SunnyYoshimitsu/CelestiCall/Hardwares/IPModules/USB 1.1/USB 1.1.runs/synth_1/.vivado.begin.rst

<?xml version="1.0"?>
<ProcessHandle Version="1" Minor="0">
    <Process Command="vivado.bat" Owner="Hatsu" Host="DESKTOP-I4589KT" Pid="29064" HostCore="12" HostMemory="034246979584">
    </Process>
</ProcessHandle>
