SunnyYoshimitsu/CelestiCall/Hardwares/IPModules/Sound/Sound Processor/Sound Processor.runs/impl_1/.vivado.begin.rst

<?xml version="1.0"?>
<ProcessHandle Version="1" Minor="0">
    <Process Command="vivado.bat" Owner="Hatsu" Host="DESKTOP-I4589KT" Pid="4896" HostCore="12" HostMemory="034246979584">
    </Process>
</ProcessHandle>
<?xml version="1.0"?>
<ProcessHandle Version="1" Minor="0">
    <Process Command="vivado.bat" Owner="Hatsu" Host="DESKTOP-I4589KT" Pid="36952" HostCore="12" HostMemory="034246979584">
    </Process>
</ProcessHandle>
<?xml version="1.0"?>
<ProcessHandle Version="1" Minor="0">
    <Process Command="vivado.bat" Owner="Hatsu" Host="DESKTOP-I4589KT" Pid="32116" HostCore="12" HostMemory="034246979584">
    </Process>
</ProcessHandle>
<?xml version="1.0"?>
<ProcessHandle Version="1" Minor="0">
    <Process Command="vivado.bat" Owner="Hatsu" Host="DESKTOP-I4589KT" Pid="14284" HostCore="12" HostMemory="034246979584">
    </Process>
</ProcessHandle>
<?xml version="1.0"?>
<ProcessHandle Version="1" Minor="0">
    <Process Command="vivado.bat" Owner="Hatsu" Host="DESKTOP-I4589KT" Pid="36900" HostCore="12" HostMemory="034246979584">
    </Process>
</ProcessHandle>
<?xml version="1.0"?>
<ProcessHandle Version="1" Minor="0">
    <Process Command="vivado.bat" Owner="Hatsu" Host="DESKTOP-I4589KT" Pid="37376" HostCore="12" HostMemory="034246979584">
    </Process>
</ProcessHandle>
<?xml version="1.0"?>
<ProcessHandle Version="1" Minor="0">
    <Process Command="vivado.bat" Owner="Hatsu" Host="DESKTOP-I4589KT" Pid="20940" HostCore="12" HostMemory="034246979584">
    </Process>
</ProcessHandle>
<?xml version="1.0"?>
<ProcessHandle Version="1" Minor="0">
    <Process Command="vivado.bat" Owner="Hatsu" Host="DESKTOP-I4589KT" Pid="10028" HostCore="12" HostMemory="034246979584">
    </Process>
</ProcessHandle>
<?xml version="1.0"?>
<ProcessHandle Version="1" Minor="0">
    <Process Command="vivado.bat" Owner="Hatsu" Host="DESKTOP-I4589KT" Pid="37008" HostCore="12" HostMemory="034246979584">
    </Process>
</ProcessHandle>
<?xml version="1.0"?>
<ProcessHandle Version="1" Minor="0">
    <Process Command="vivado.bat" Owner="Hatsu" Host="DESKTOP-I4589KT" Pid="36076" HostCore="12" HostMemory="034246979584">
    </Process>
</ProcessHandle>
<?xml version="1.0"?>
<ProcessHandle Version="1" Minor="0">
    <Process Command="vivado.bat" Owner="Hatsu" Host="DESKTOP-I4589KT" Pid="30560" HostCore="12" HostMemory="034246979584">
    </Process>
</ProcessHandle>
