SunnyYoshimitsu/CelestiCall/Hardwares/IPModules/Sound/Sound Processor/Sound Processor.runs/impl_1/clockInfo.txt

-------------------------------------
| Tool Version : Vivado v.2024.1
| Date         : Thu Jan  9 15:50:44 2025
| Host         : DESKTOP-I4589KT
| Design       : design_1
| Device       : xc7a100t-csg324-1--
-------------------------------------

For more information on clockInfo.txt clock routing debug file see https://support.xilinx.com/s/article/000035660?language=en_US
