SunnyYoshimitsu/CelestiCall/Hardwares/IPModules/Sound/Sound Processor/Sound Processor.runs/synth_1/.vivado.begin.rst

<?xml version="1.0"?>
<ProcessHandle Version="1" Minor="0">
    <Process Command="vivado.bat" Owner="Hatsu" Host="DESKTOP-I4589KT" Pid="4352" HostCore="12" HostMemory="034246979584">
    </Process>
</ProcessHandle>
