SunnyYoshimitsu/CelestiCall/Hardwares/Library_vivado/ip/hls_gamma_correction_1_0/doc/HLS_Gamma Correction_v1_0.pdf

1300 Henley Court
Pullman, WA 99163
509.334.6306
www.digilentinc.com

## HLS Gamma Correction 1.0 IP Core User Guide

Revised June 21, 2018; Author Ciprian Hegbeli

DOC#: 516-003 | Copyright Digilent, Inc. All rights reserved.
Other product and company names mentioned may be trademarks of their respective owners. | Page 1 of 5

## 1 Introduction

This user guide describes the Digilent Gamma Correction Intellectual Property. This IP interfaces to both the Axi-Lite and Axi-Stream in order to process a video stream and control the resolution and the gamma factor.

## 2 Features

- Axi- Stream 24-bit video input and output
- Axi-Lite interface for gamma and resolution control
- Resolution supported: up to 1920x1080/60Hz (clock: 148.5 MHz)
- Gamma adjustment: 0.4, 0.2, 1, 1.2, 1.4, 1.6, 1.8, 2.0, 2.2

## 3 Performance

The IP has been written in HLS with a target clock frequency of 150 MHz (6.67 ns) for a maximum resolution
of 1920x1080. The maximum latency is at 2081164 ns with
an initiation interval of 2081164 ns which is approximately
one frame. The latency and initiation interval are scaled with the input resolution, meaning that a lower resolution the latency will also be lower.

## 4 Usage

The IP has been initially designed for a xc7z020clg400-1 target device, the resource usage for this FPGA are illustrated in

IP quick facts

Supported device
families | Zynq®-7000, 7 series
Supported user interfaces | Axi-Lite
| Axi-Stream

Provided with core

Design files | C++
Simulation model | HLS Simulation
Constraints file | XDC
Software driver | Automatically
| generated

Tested design flows

Design entry | Vivado™ Design
| Suite 2017.4
Synthesis | Vivado Synthesis
| 2017.4

Sync 1.0 IP Core User Guide
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
