SunnyYoshimitsu/CelestiCall/Possible FPGA SoC Graphics/CelestiSoC.jpg

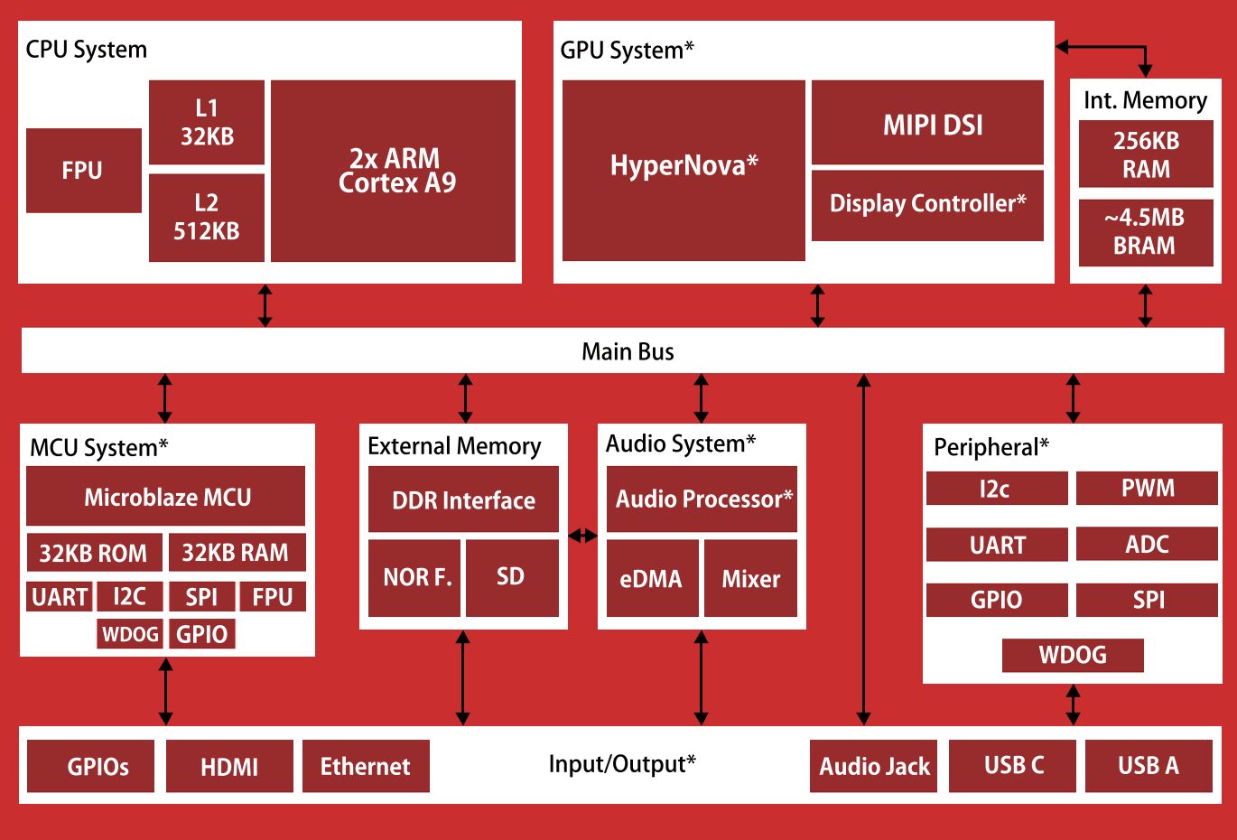
Possible FPGA SoC Graphics/CelestiSoC.jpg
