SunnyYoshimitsu/CelestiCall/Possible FPGA SoC Graphics/Rough Project Timeline.png

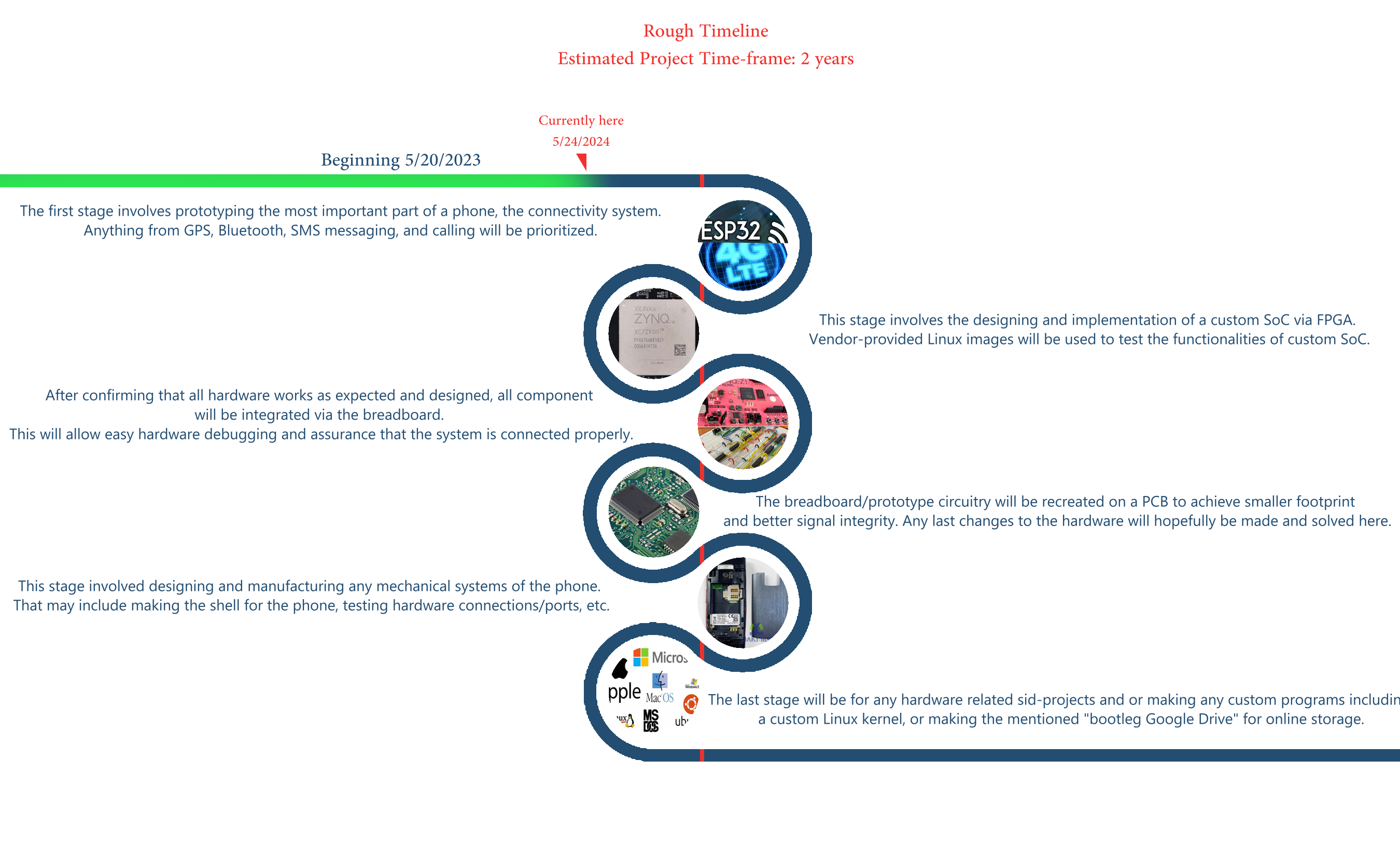
Possible FPGA SoC Graphics/Rough Project Timeline.png
