SunnyYoshimitsu/CelestiCall/Schematic & PCB (pending fixing)/zynqPCB-master/footprints/ESP32-C3 supermini v5.step

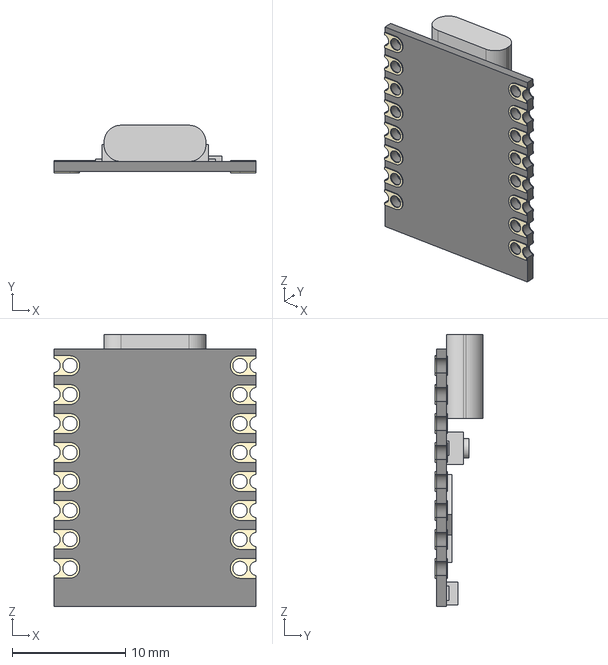
[picture p47: CAD file, 2024-06-05]
Schematic & PCB (pending fixing)/zynqPCB-master/footprints/ESP32-C3 supermini v5.step
17.8 x 4.20 x 24.0 mm
