SunnyYoshimitsu/CelestiCall/Schematic & PCB (pending fixing)/zynqPCB-master/footprints/SIM7100-6-1-15-00-A_REVC.step

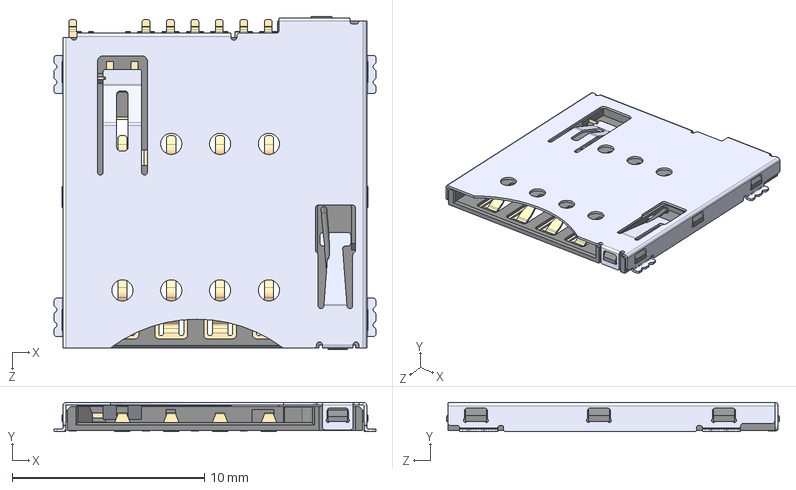
[picture p48: CAD file, 2024-06-05]
Schematic & PCB (pending fixing)/zynqPCB-master/footprints/SIM7100-6-1-15-00-A_REVC.step
16.8 x 1.53 x 17.3 mm
