SunnyYoshimitsu/CelestiCall/Hardwares/Library_vivado/ip/rgb2vga_v1_0/docs/rgb2vga_v1_0.pdf

1300 Henley Court
Pullman, WA 99163
509.334.6306
www.digilentinc.com

## RGB-to-VGA 1.0 IP Core User Guide

Revised April 23, 2015; Author Elod Gyorgy

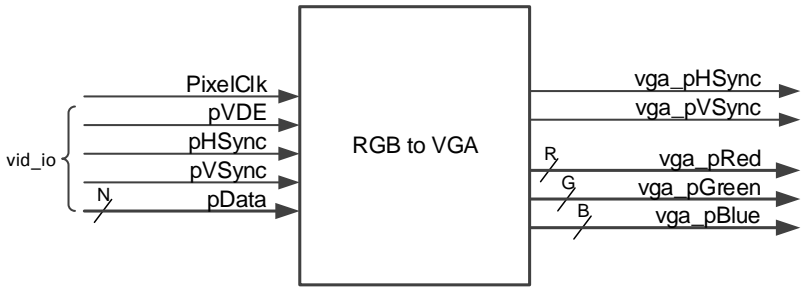
[picture p50: figure]
RGB to VGA; vga_pRed vga_pGreen vga_pBlue; vga_pHSync vga_pVSync; PixelClk pVDE pHSync pVSync pData; vid_io

DOC#: 506-031 | Copyright Digilent, Inc. All rights reserved.
Other product and company names mentioned may be trademarks of their respective owners. | Page 1 of 2

## 1 Overview

This user guide describes the Digilent RGB-to-VGA Intellectual Property. This IP accepts a Xilinx vid_io input and outputs an independently customizable color depth, properly blanked RGB pixel bus to connect to a VGA DAC. On Digilent boards the outputs directly connect to the on-board resistor ladder that serves as VGA DAC. The supported color depth varies between boards and the IP should be configured to match it.

## 2 Performance

The IP itself does not include timing constrains. PixelClk is still expected to be period-constrained from outside.

## 3 Port descriptions

Figure 1. IP top-level diagram.

The signals of the RGB-to-VGA Core are listed and described in Table 1.

IP quick facts

Supported device
families | Zynq®-7000, 7 series

Supported user
interfaces | Xilinx: vid_io

Provided with core

Design files | VHDL
Simulation model | VHDL Behavioral
Constraints file | N/A
Software driver | N/A

Tested design flows

Design entry | Vivado™ Design
| Suite 2014.4
Synthesis | Vivado Synthesis
| 2014.4

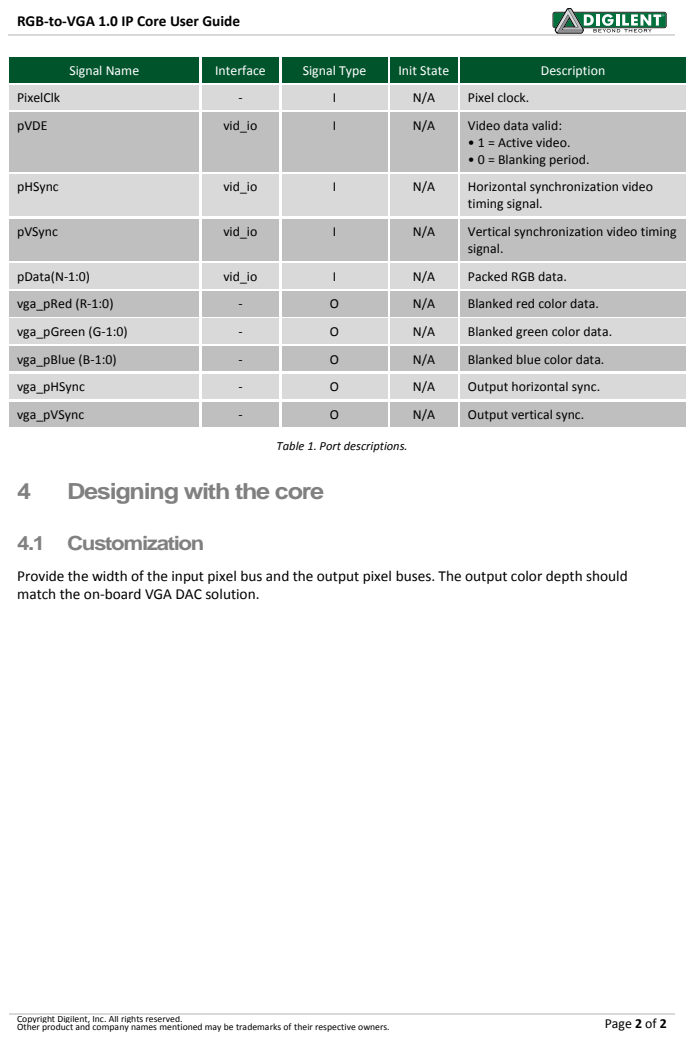
[picture p51: page 2]
Other product and company names mentioned may be trademarks of their respective owners.; Page 2 of 2; Signal Name; Interface; Signal Type; Init State; Description; PixelClk; Pixel clock.; pVDE; vid_io; Video data valid:; • 1 = Active video. • 0 = Blanking period.; pHSync; Horizontal synchronization video; timing signal.; pVSync; Vertical synchronization video timing; signal.; pData(N-1:0); Packed RGB data.; vga_pRed (R-1:0); Blanked red color data.; vga_pGreen (G-1:0)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

RGB-to-VGA 1.0 IP Core User Guide

Table 1. Port descriptions.

4 Designing with the core

Provide the width of the input pixel bus and the output pixel buses. The output color depth should
match the on-board VGA DAC solution.

Copyright Digilent, Inc. All rights reserved.
