SunnyYoshimitsu/CelestiCall/Hardwares/Library_vivado/ip/video_scaler/doc/video_scaler.pdf

1300 Henley Court
Pullman, WA 99163
509.334.6306
www.digilentinc.com

## Video Scaler 1.0 IP Core User Guide

Revised January 28, 2019; Author Elod Gyorgy

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

## 1 Introduction

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

## 2 Features

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

## 3 Designing with the core

## 3.1 Constraints 3.2 Customization

## 4 Register map

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

IP quick facts

Supported device
families | Zynq®-7000, 7 series
Supported user interfaces | Xilinx®: AXI4-Lite,
| AXI-Stream

Provided with core

Design files | VHDL
Simulation model | VHDL Behavioral
Constraints file | XDC
Software driver | standalone

Tested design flows

Design entry | Vivado™ HLS 2018.2
Synthesis | Vivado Synthesis
| 2018.2

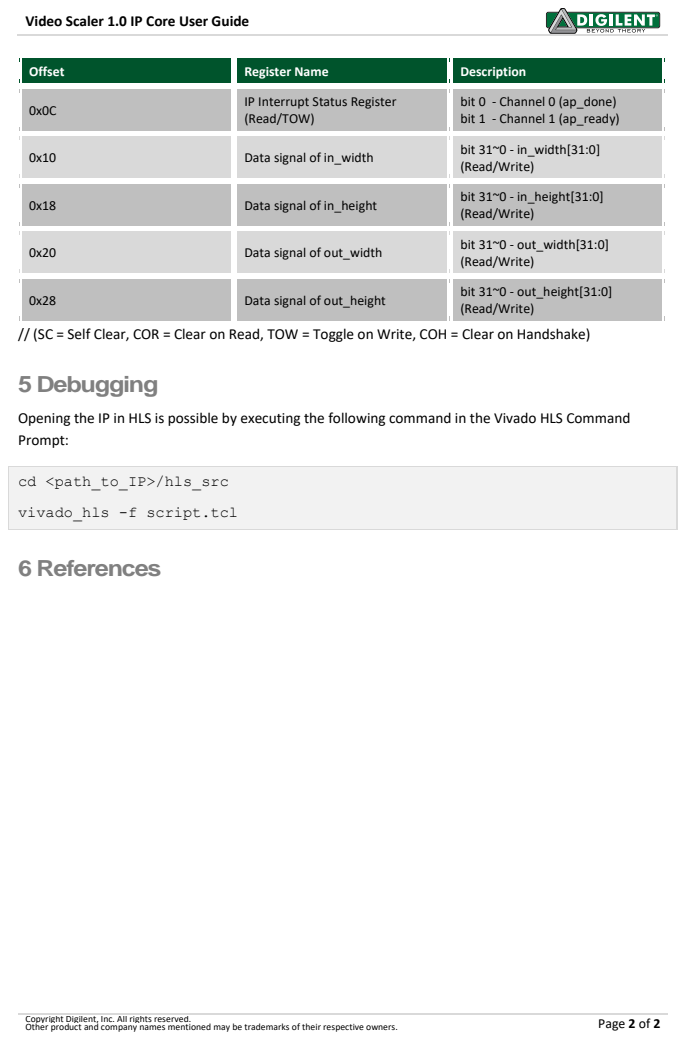
[picture p52: page 2]
Other product and company names mentioned may be trademarks of their respective owners.; Page 2 of 2; Offset; Register Name; Description; IP Interrupt Status Register; (Read/TOW); bit 0 - Channel 0 (ap_done) bit 1 - Channel 1 (ap_ready); Data signal of in_width; bit 31~0 - in_width[31:0]; (Read/Write); Data signal of in_height; bit 31~0 - in_height[31:0]; Data signal of out_width; bit 31~0 - out_width[31:0]; Data signal of out_height; bit 31~0 - out_height[31:0]; 5 Debugging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

Video Scaler 1.0 IP Core User Guide

// (SC = Self Clear, COR = Clear on Read, TOW = Toggle on Write, COH = Clear on Handshake)

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

Copyright Digilent, Inc. All rights reserved.
