SunnyYoshimitsu/CelestiCall/Hardwares/Library_vivado/ip/rgb2dpvid_v1_0/docs/rgb2dpvid_v1_0.pdf

## RGB-to-DPVID 1.0 IP Core User Guide

## 1 Introduction

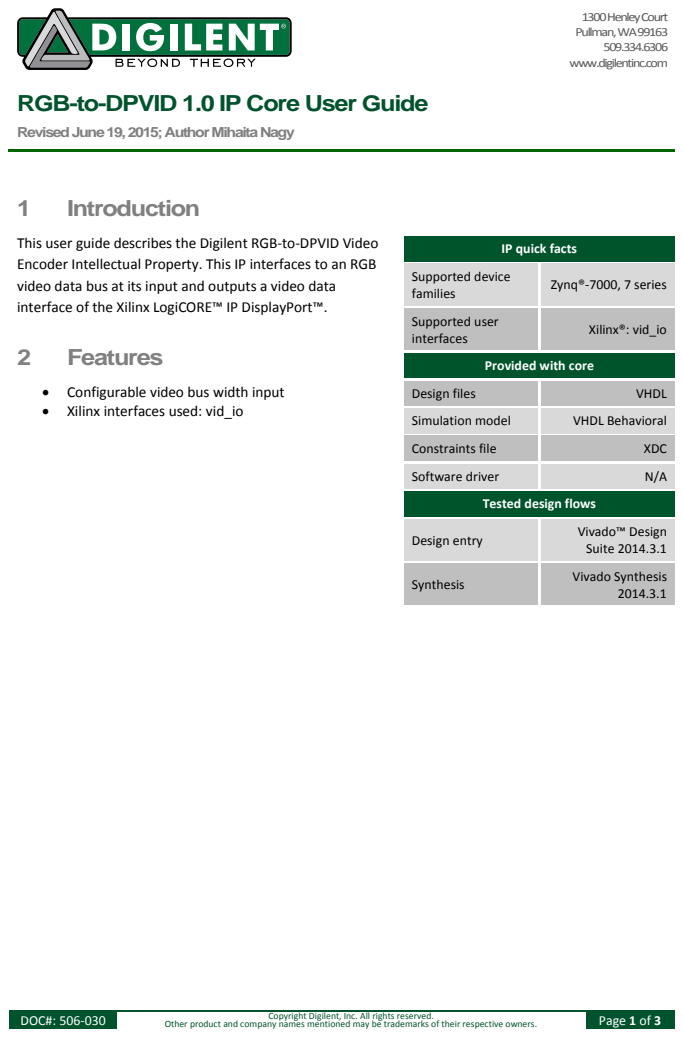
[picture p53: page 1]
DOC#: 506-030; Copyright Digilent, Inc. All rights reserved.; Other product and company names mentioned may be trademarks of their respective owners.; Page 1 of 3; 2 Features; Supported device; families; Zynq®-7000, 7 series; Supported user; interfaces; Xilinx®: vid_io; Design files; VHDL; Simulation model; VHDL Behavioral; Constraints file; XDC; Software driver; Design entry; Vivado™ Design; Suite 2014.3.1; Synthesis; Vivado Synthesis

1300 Henley Court
Pullman, WA 99163
www.digilentinc.com

Revised June 19, 2015; Author Mihaita Nagy

This user guide describes the Digilent RGB-to-DPVID Video
Encoder Intellectual Property. This IP interfaces to an RGB
video data bus at its input and outputs a video data
interface of the Xilinx LogiCORE™ IP DisplayPort™.

IP quick facts

Provided with core

• Configurable video bus width input
• Xilinx interfaces used: vid_io

Tested design flows

## 3 Overview

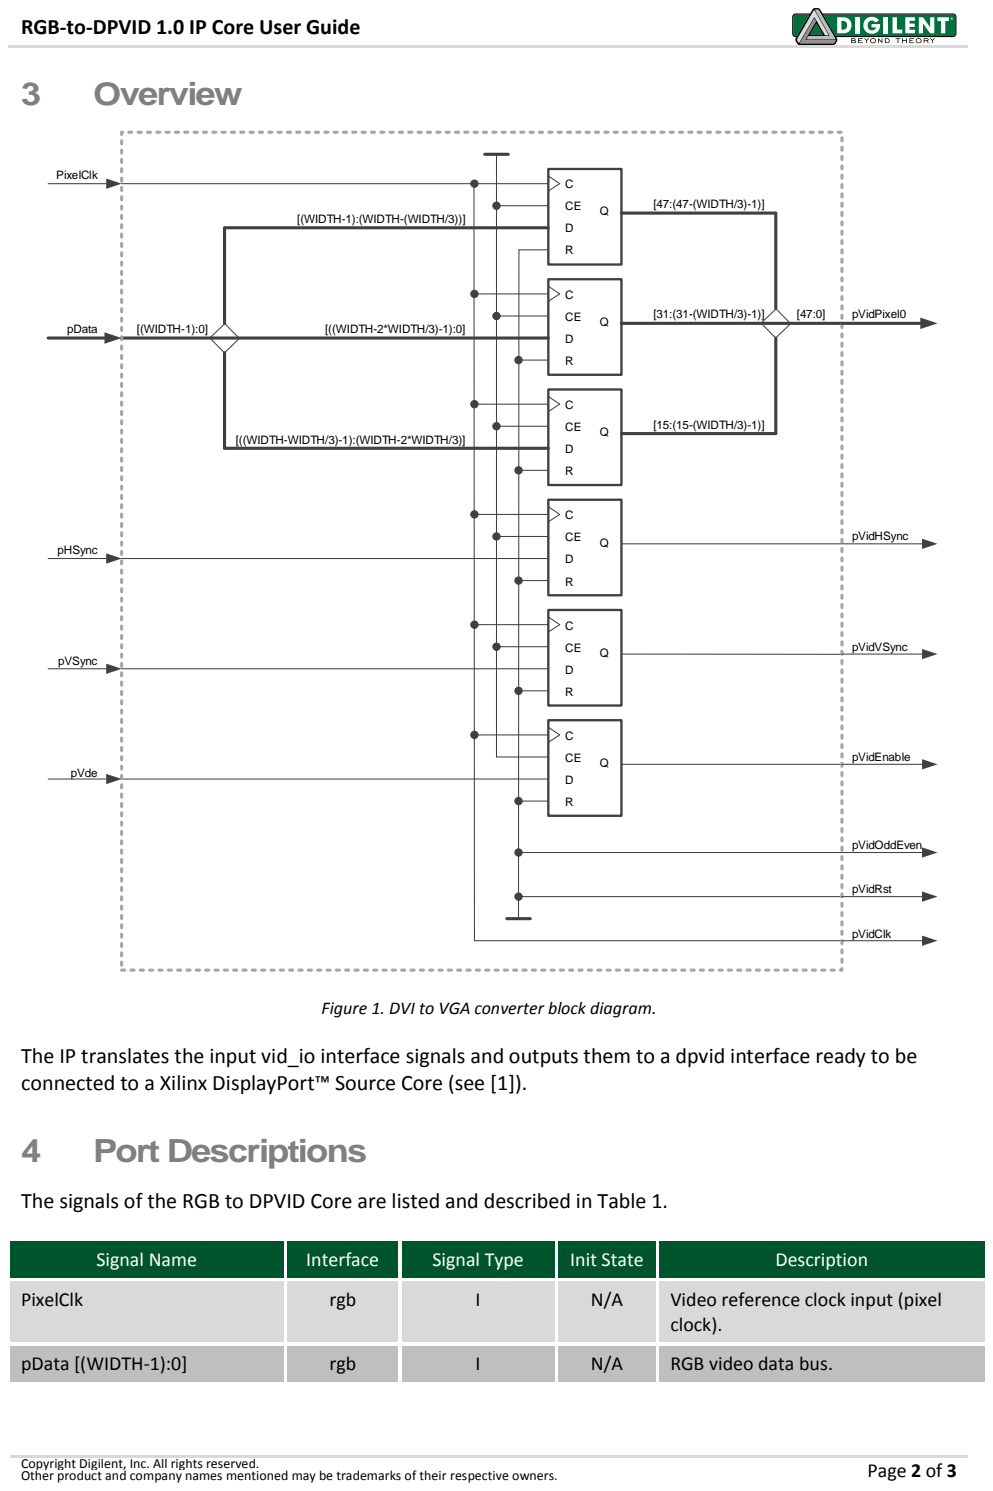
[picture p54: page 2]
Other product and company names mentioned may be trademarks of their respective owners.; Page 2 of 3; [((WIDTH-2*WIDTH/3)-1):0]; [47:(47-(WIDTH/3)-1)]; [31:(31-(WIDTH/3)-1)]; [15:(15-(WIDTH/3)-1)]; [(WIDTH-1):0]; PixelClk; pData; pHSync; pVSync; pVde; pVidPixel0; pVidHSync; pVidVSync; pVidEnable; pVidOddEven; pVidRst; pVidClk; 4 Port Descriptions; Signal Name; Interface; Signal Type; Init State; Description; rgb; Video reference clock input (pixel; clock).; pData [(WIDTH-1):0]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

RGB-to-DPVID 1.0 IP Core User Guide

[(WIDTH-1):(WIDTH-(WIDTH/3))]

[((WIDTH-WIDTH/3)-1):(WIDTH-2*WIDTH/3)]

Figure 1. DVI to VGA converter block diagram.

The IP translates the input vid_io interface signals and outputs them to a dpvid interface ready to be
connected to a Xilinx DisplayPort™ Source Core (see [1]).

The signals of the RGB to DPVID Core are listed and described in Table 1.

Copyright Digilent, Inc. All rights reserved.

RGB-to-DPVID 1.0 IP Core User Guide

Copyright Digilent, Inc. All rights reserved.
Other product and company names mentioned may be trademarks of their respective owners. | Page 3 of 3
pHSync | rgb | I | N/A | Horizontal synchronization video timing signal.
pVSync | rgb | I | N/A | Vertical synchronization video timing signal.
pVde | rgb | I | N/A | Video data valid: • 1 = Active video. • 0 = Blanking period.
pVidClk | dpvid | O | 0 | Forwarded PixelClk signal.
pVidPixel0 [47:0] | dpvid | O | zeros | Video data output.
pVidHSync | dpvid | O | 0 | Horizontal synchronization video timing signal.
pVidVSync | dpvid | O | 0 | Vertical synchronization video timing signal.
pVidEnable | dpvid | O | 0 | Video data qualifier: • 1 = Video data valid. • 0 = Video data not valid.
pVidOddEven | dpvid | O | 0 | Unused.
pVidRst | dpvid | O | 0 | Unused.

Table 1. Port descriptions.

## 5 Parameter Descriptions

The parameters of the RGB to DPVID Core are listed and described in Table 12 below.

Parameter Name | Range | Type | Default | Description
kDataWidth | 0 - 47 | integer | 24 | Sets the input video data bus width containing already the video components. It is limited at a maximum of 48 which is the limit of the dpvid-interface data signal input (see Table 3-3 of [1]).

Table 2. Parameter descriptions.

## 6 References

The following documents provide additional information on the subjects discussed:

1. Xilinx Inc., PG064: DisplayPort LogiCORE IP Product Guide, v6.0, April 1, 2015.
