SunnyYoshimitsu/CelestiCall/Schematic & PCB (pending fixing)/zynqPCB-master/Audio.kicad_sch

## KiCad design Schematic & PCB (pending fixing)/zynqPCB-master/Audio.kicad_sch (2024-07-29)

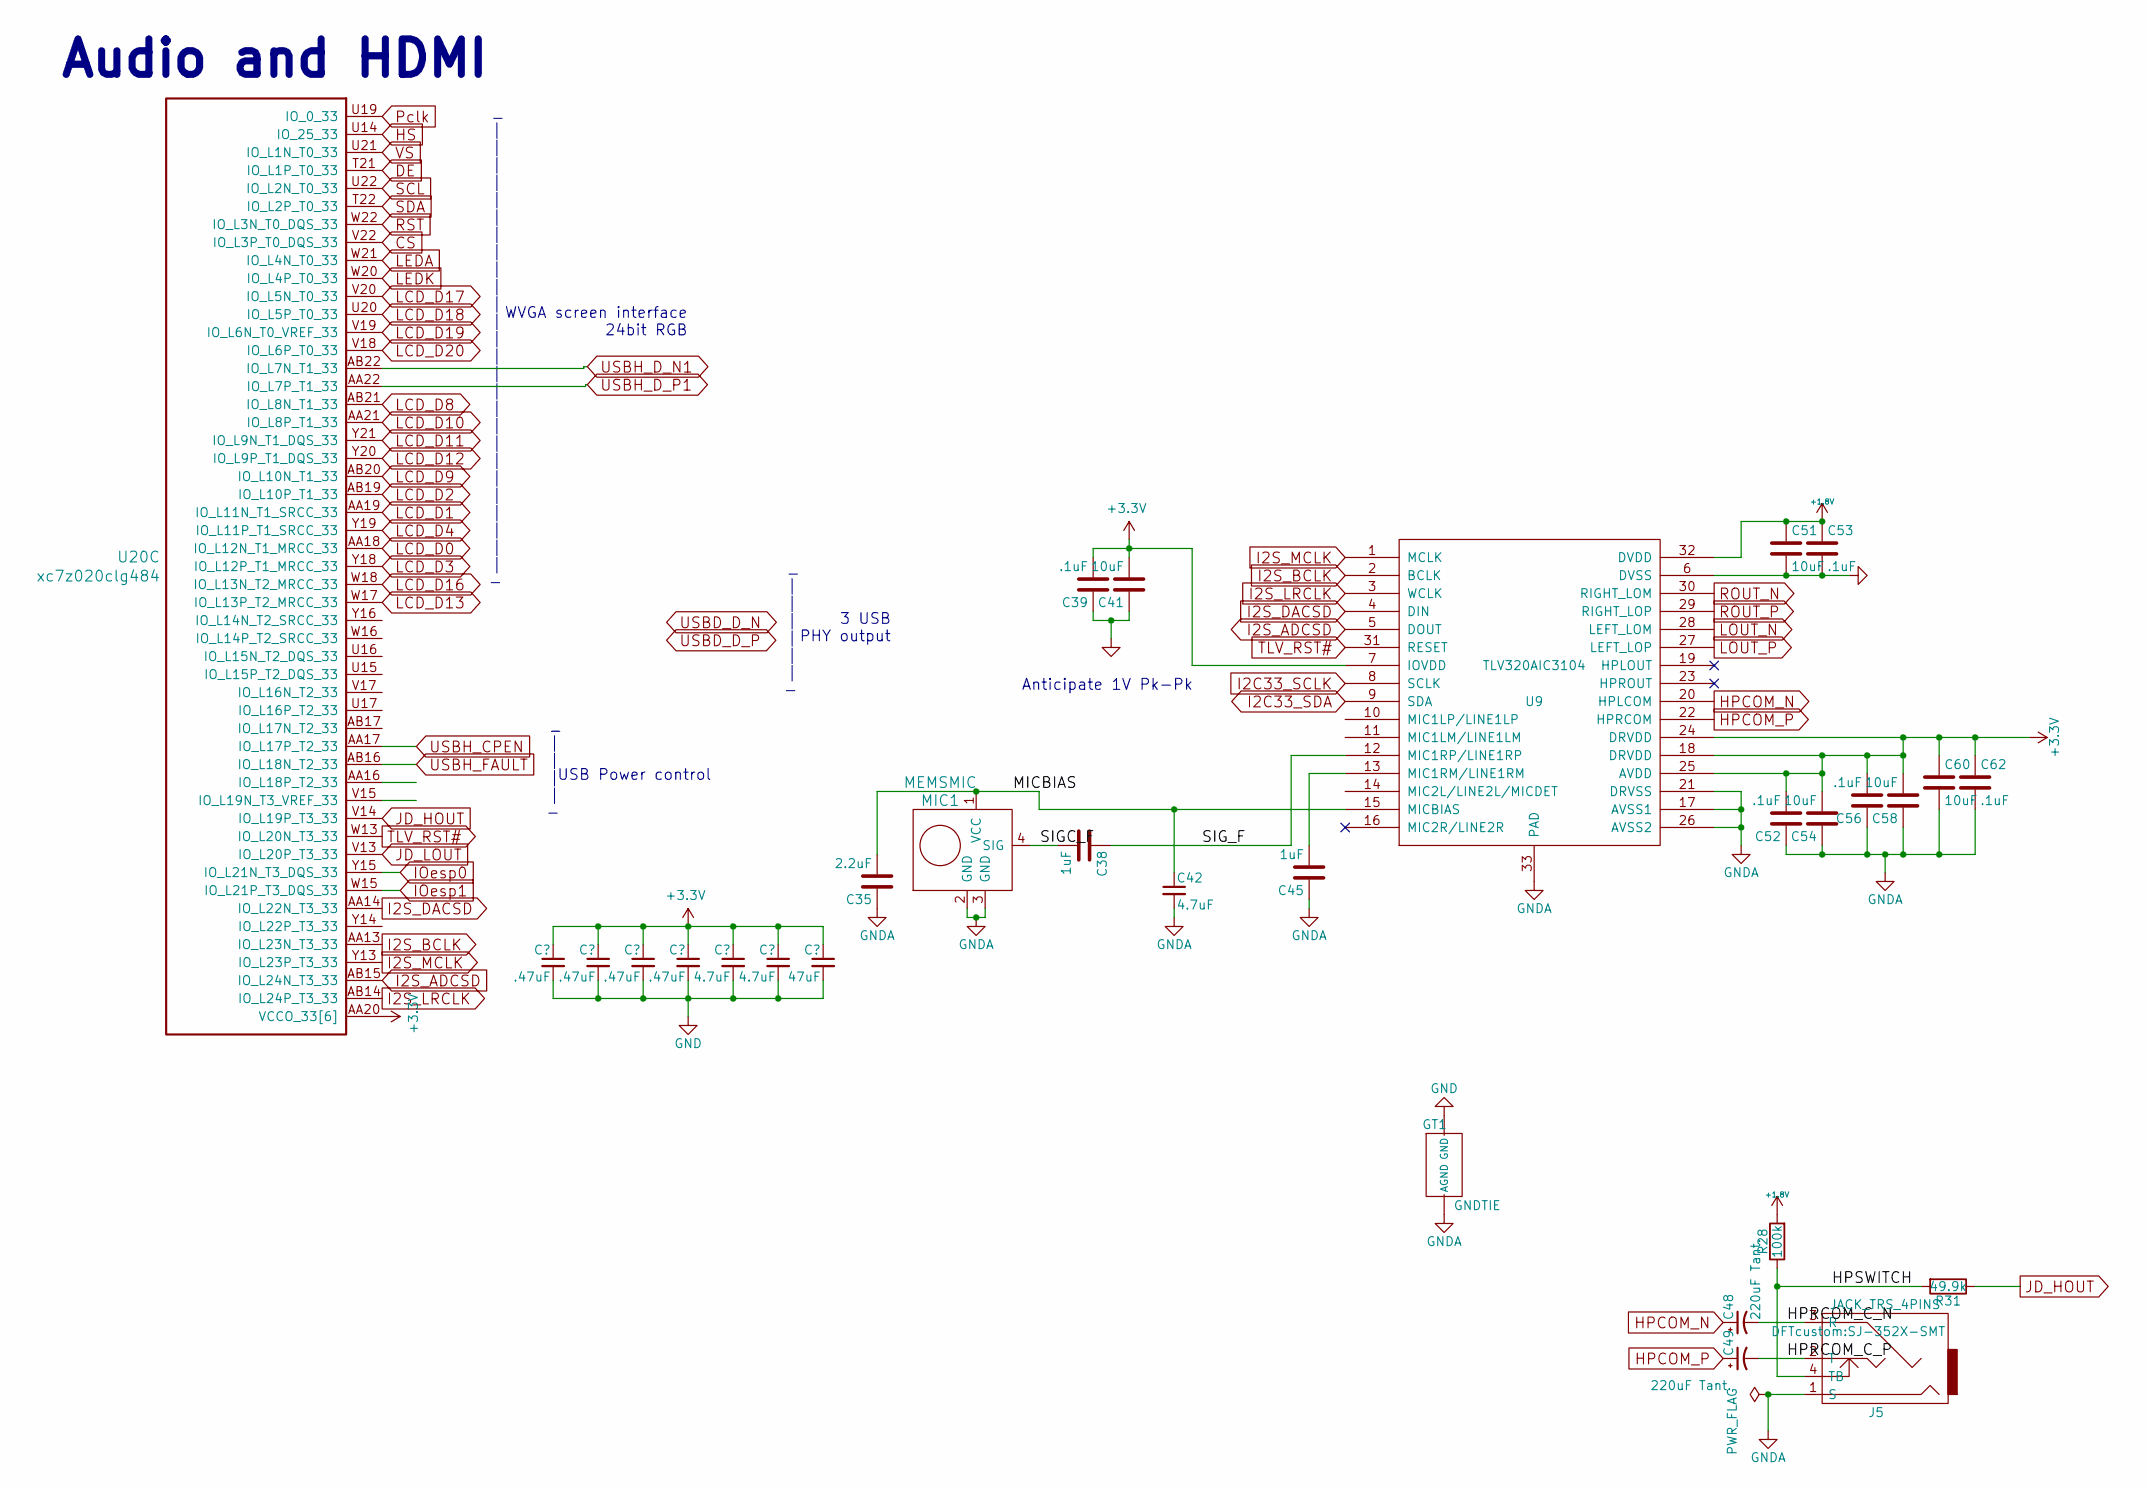
[picture p72: schematic Audio.kicad_sch]

Parts:
C35: 2.2uF; C_0402_1005Metric; MPN GRM155R61A225KE95D
C38, C45: 1uF; C_0402_1005Metric; MPN CC0402KRX5R6BB105
C39, C52, C53, C56, C62: .1uF; C_0402_1005Metric; MPN CC0402KRX7R6BB104
C41, C51, C54, C58, C60: 10uF; C_0603_1608Metric; MPN GRM188R61A106KE69J
C42, C57, C59: 4.7uF; C_0402_1005Metric; MPN GRM155R60G475ME47D
C46, C47, C50, C55: .47uF; C_0402_1005Metric; MPN CC0402KRX5R5BB474
C48, C49: 220uF Tant.; CP_EIA-3528-12_Kemet-T; MPN F930G227KBA
C61: 47uF; C_0805_2012Metric; MPN GRM219R60J476ME44D
GT1: GNDTIE; gndtie
J5: JACK_TRS_4PINS; SJ-352X-SMT; MPN SJ-3524-SMT-TR
MIC1: MEMSMIC; MIC_SPW2430HR5H-B; MPN SPW2430HR5H-B
R28: 100k; R_0402_1005Metric; MPN RC0402FR-07100KL
R31: 49.9k; R_0402_1005Metric; MPN RC0402FR-0749K9L
U9: TLV320AIC3104; QFN-32-1EP_5x5mm_P0.5mm_EP3.65x3.65mm; MPN TLV320AIC3104IRHBR
U20: xc7z020clg484; BGA-484_19.0x19.0mm_Layout22x22_P0.80mm_dia0.40mm; MPN XC7Z020-1CLG484C

Connections:
+1.8V: C51.1, C53.1, R28.2, U9.32 (DVDD)
+3.3V: C39.2, C41.2, C46.1, C47.1, C50.1, C52.2, C54.2, C55.1, C56.2, C57.1, C58.2, C59.1, C60.1, C61.1, C62.1, U9.7 (IOVDD), U9.18 (DRVDD), U9.24 (DRVDD), U9.25 (AVDD), U20.AA20 (VCCO_33[6]), U20.AB13 (VCCO_33[6]), U20.U18 (VCCO_33[6]), U20.V21 (VCCO_33[6]), U20.W14 (VCCO_33[6]), U20.Y17 (VCCO_33[6])
CS: U20.V22 (IO_L3P_T0_DQS_33)
DE: U20.T21 (IO_L1P_T0_33)
GND: C39.1, C41.1, C46.2, C47.2, C50.2, C51.2, C53.2, C55.2, C57.2, C59.2, C61.2, GT1.1 (GND), U9.6 (DVSS)
GNDA: C35.1, C42.2, C45.1, C52.1, C54.1, C56.1, C58.1, C60.2, C62.2, GT1.2 (AGND), J5.1 (S), MIC1.2 (GND), MIC1.3 (GND), U9.17 (AVSS1), U9.21 (DRVSS), U9.26 (AVSS2), U9.33 (PAD)
HPCOM_N: C48.1, U9.20 (HPLCOM)
HPCOM_P: C49.1, U9.22 (HPRCOM)
HPRCOM_C_N: C48.2, J5.3 (R)
HPRCOM_C_P: C49.2, J5.2 (T)
HPSWITCH: J5.4 (TB), R28.1, R31.2
HS: U20.U14 (IO_25_33)
I2C33_SCLK: U9.8 (SCLK)
I2C33_SDA: U9.9 (SDA)
I2S_ADCSD: U9.5 (DOUT), U20.AB15 (IO_L24N_T3_33)
I2S_BCLK: U9.2 (BCLK), U20.AA13 (IO_L23N_T3_33)
I2S_DACSD: U9.4 (DIN), U20.AA14 (IO_L22N_T3_33)
I2S_LRCLK: U9.3 (WCLK), U20.AB14 (IO_L24P_T3_33)
I2S_MCLK: U9.1 (MCLK), U20.Y13 (IO_L23P_T3_33)
IOesp0: U20.Y15 (IO_L21N_T3_DQS_33)
IOesp1: U20.W15 (IO_L21P_T3_DQS_33)
JD_HOUT: R31.1, U20.V14 (IO_L19P_T3_33)
JD_LOUT: U20.V13 (IO_L20P_T3_33)
LCD_D0: U20.AA18 (IO_L12N_T1_MRCC_33)
LCD_D1: U20.AA19 (IO_L11N_T1_SRCC_33)
LCD_D2: U20.AB19 (IO_L10P_T1_33)
LCD_D3: U20.Y18 (IO_L12P_T1_MRCC_33)
LCD_D4: U20.Y19 (IO_L11P_T1_SRCC_33)
LCD_D8: U20.AB21 (IO_L8N_T1_33)
LCD_D9: U20.AB20 (IO_L10N_T1_33)
LCD_D10: U20.AA21 (IO_L8P_T1_33)
LCD_D11: U20.Y21 (IO_L9N_T1_DQS_33)
LCD_D12: U20.Y20 (IO_L9P_T1_DQS_33)
LCD_D13: U20.W17 (IO_L13P_T2_MRCC_33)
LCD_D16: U20.W18 (IO_L13N_T2_MRCC_33)
LCD_D17: U20.V20 (IO_L5N_T0_33)
LCD_D18: U20.U20 (IO_L5P_T0_33)
LCD_D19: U20.V19 (IO_L6N_T0_VREF_33)
LCD_D20: U20.V18 (IO_L6P_T0_33)
LEDA: U20.W21 (IO_L4N_T0_33)
LEDK: U20.W20 (IO_L4P_T0_33)
LOUT_N: U9.28 (LEFT_LOM)
LOUT_P: U9.27 (LEFT_LOP)
MICBIAS: C35.2, C42.1, MIC1.1 (VCC), U9.15 (MICBIAS)
unnamed: C45.2, U9.13 (MIC1RM/LINE1RM)
Pclk: U20.U19 (IO_0_33)
ROUT_N: U9.30 (RIGHT_LOM)
ROUT_P: U9.29 (RIGHT_LOP)
RST: U20.W22 (IO_L3N_T0_DQS_33)
SCL: U20.U22 (IO_L2N_T0_33)
SDA: U20.T22 (IO_L2P_T0_33)
SIGC_F: C38.2, MIC1.4 (SIG)
SIG_F: C38.1, U9.12 (MIC1RP/LINE1RP)
TLV_RST#: U9.31 (RESET), U20.W13 (IO_L20N_T3_33)
USBH_CPEN: U20.AA17 (IO_L17P_T2_33)
USBH_D_N1: U20.AB22 (IO_L7N_T1_33)
USBH_D_P1: U20.AA22 (IO_L7P_T1_33)
USBH_FAULT: U20.AB16 (IO_L18N_T2_33)
VS: U20.U21 (IO_L1N_T0_33)

Notes on the sheet:
USB Power control
_ | | | | | | -
3 USB PHY output
_ | | | | -
Anticipate 1V Pk-Pk
Audio and HDMI
_ | | | | | | | | | | | | | | | | | | | | | | | | | | -
WVGA screen interface 24bit RGB
