SunnyYoshimitsu/CelestiCall/Schematic & PCB (pending fixing)/zynqPCB-master/LCD50.kicad_sch

## KiCad design Schematic & PCB (pending fixing)/zynqPCB-master/LCD50.kicad_sch (2024-07-29)

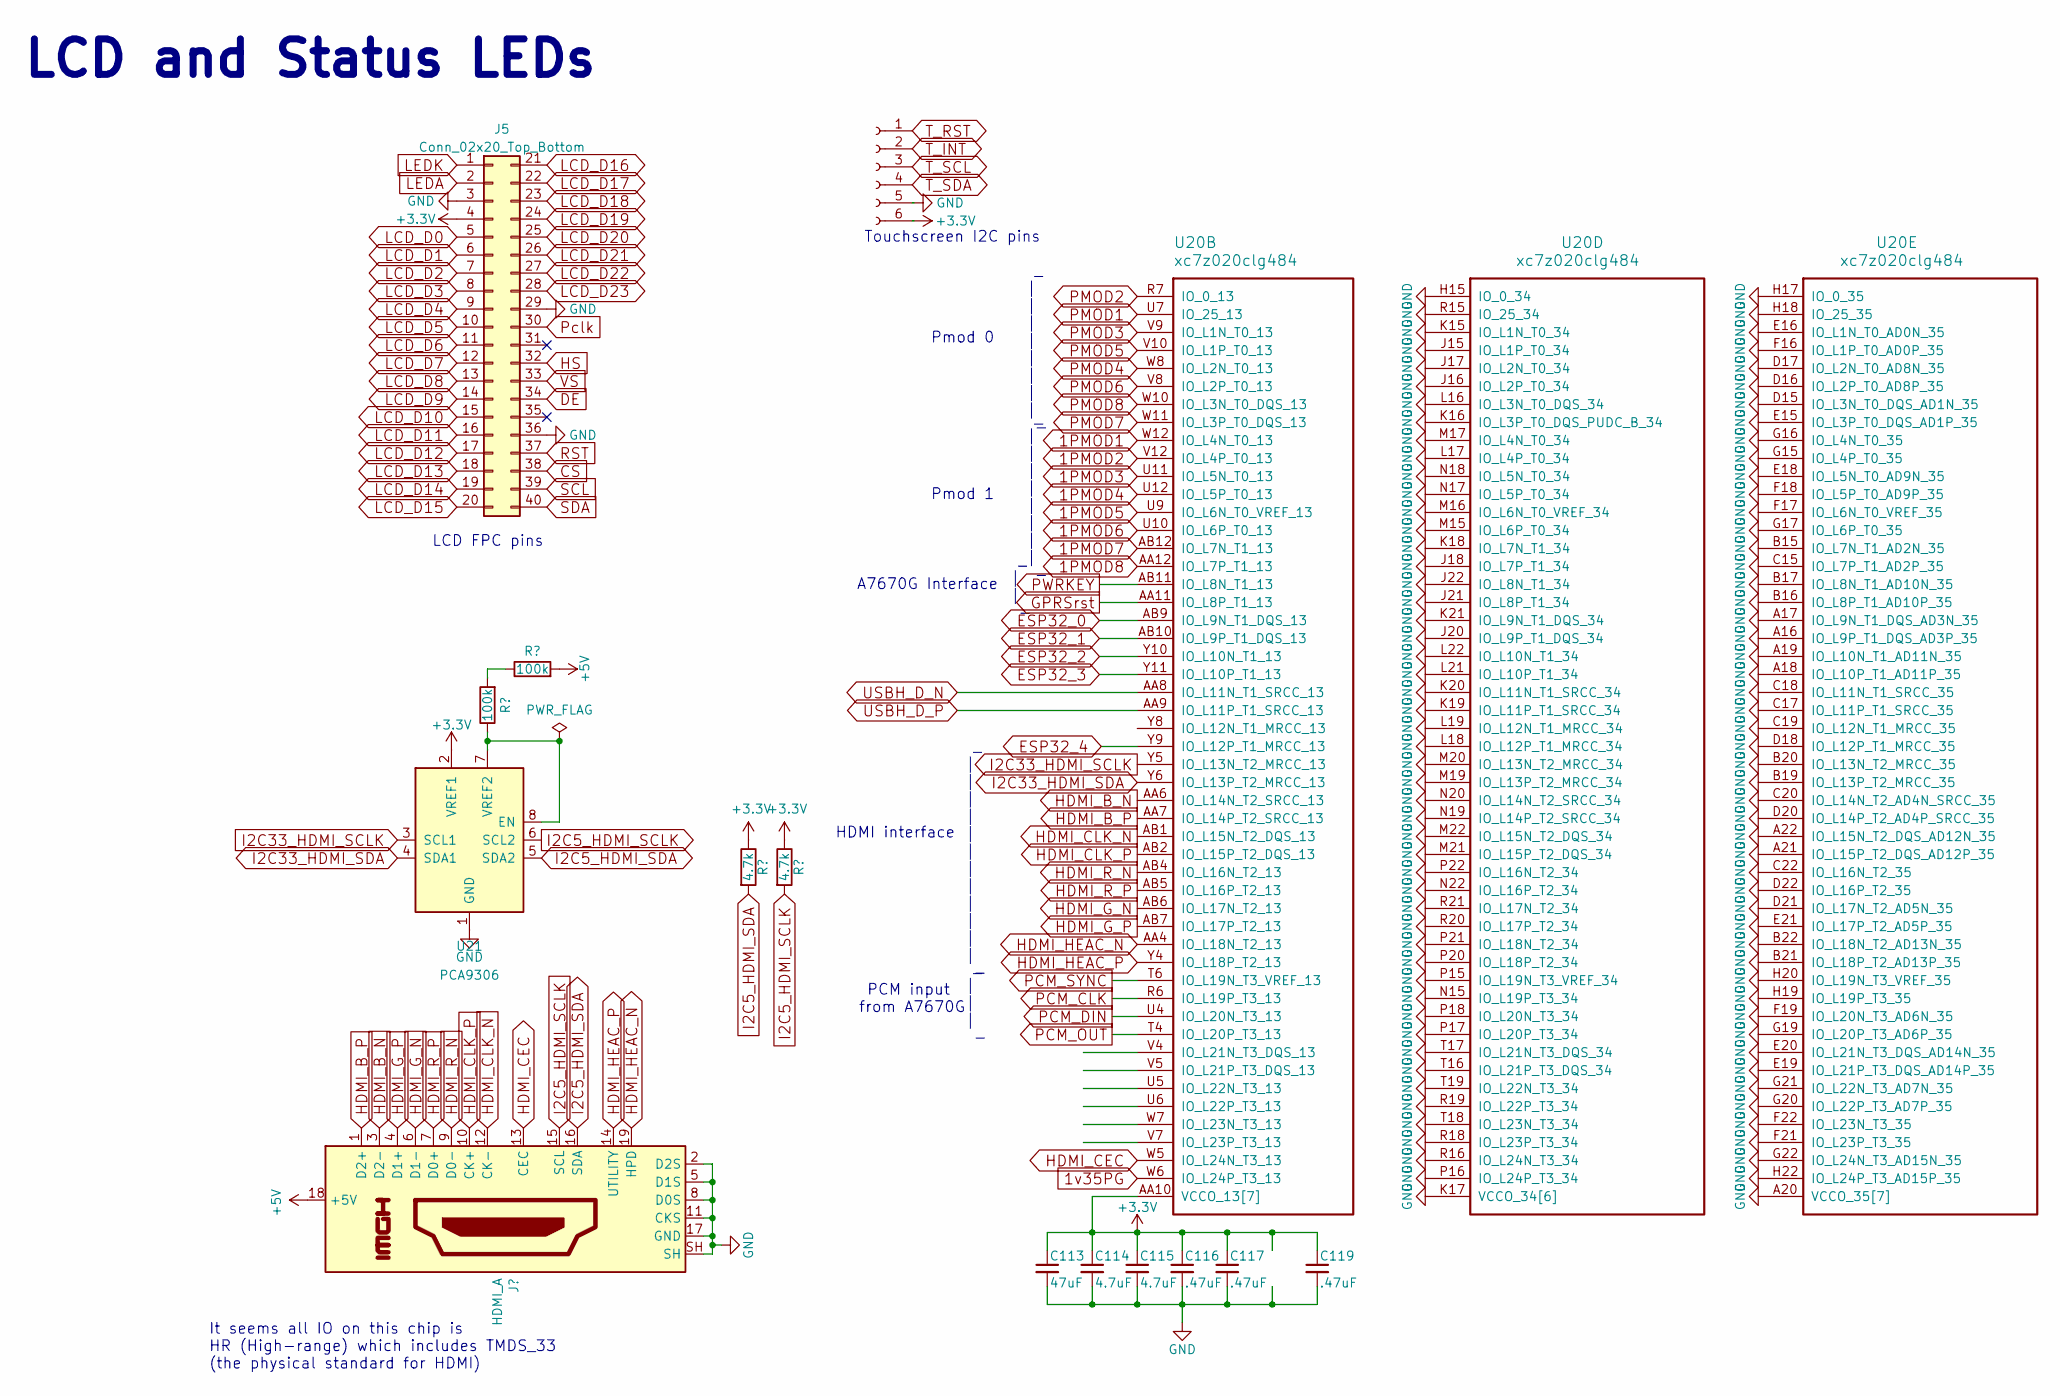
[picture p74: schematic LCD50.kicad_sch]

Parts:
C113: 47uF; C_1210_3225Metric; MPN GRM32ER70J476ME20L
C114, C115: 4.7uF; C_0402_1005Metric; MPN GRM155R60G475ME47D
C116, C117, C119: .47uF; C_0402_1005Metric; MPN CC0402KRX5R5BB474
J4: Conn_01x06_Female; Hirose_FH12-6S-0.5SH_1x06-1MP_P0.50mm_Horizontal
J5: Conn_02x20_Top_Bottom; TE_4-1734839-0_1x40-1MP_P0.5mm_Horizontal
J9: HDMI_A; 10029449-111RLF; MPN 10029449-111RLF
R34, R81: 100k; R_0402_1005Metric; MPN RC0402FR-07100KL
R82, R83: 4.7k; R_0402_1005Metric; MPN RC0402JR-074K7L
U20: xc7z020clg484; BGA-484_19.0x19.0mm_Layout22x22_P0.80mm_dia0.40mm; MPN XC7Z020-1CLG484C
U21: PCA9306; SSOP-8_2.95x2.8mm_P0.65mm; MPN PCA9306DCTR

Connections:
1PMOD1: U20.W12 (IO_L4N_T0_13)
1PMOD2: U20.V12 (IO_L4P_T0_13)
1PMOD3: U20.U11 (IO_L5N_T0_13)
1PMOD4: U20.U12 (IO_L5P_T0_13)
1PMOD5: U20.U9 (IO_L6N_T0_VREF_13)
1PMOD6: U20.U10 (IO_L6P_T0_13)
1PMOD7: U20.AB12 (IO_L7N_T1_13)
1PMOD8: U20.AA12 (IO_L7P_T1_13)
1v35PG: U20.W6 (IO_L24P_T3_13)
+3.3V: C113.1, C114.1, C115.1, C116.1, C117.1, C119.1, J4.6, J5.4, R82.1, R83.1, U20.AA10 (VCCO_13[7]), U20.AB3 (VCCO_13[7]), U20.T5 (VCCO_13[7]), U20.U8 (VCCO_13[7]), U20.V11 (VCCO_13[7]), U20.W4 (VCCO_13[7]), U20.Y7 (VCCO_13[7]), U21.2 (VREF1)
+5V: J9.18 (+5V), R81.2
CS: J5.38
DE: J5.34
ESP32_0: U20.AB9 (IO_L9N_T1_DQS_13)
ESP32_1: U20.AB10 (IO_L9P_T1_DQS_13)
ESP32_2: U20.Y10 (IO_L10N_T1_13)
ESP32_3: U20.Y11 (IO_L10P_T1_13)
ESP32_4: U20.Y9 (IO_L12P_T1_MRCC_13)
GND: C113.2, C114.2, C115.2, C116.2, C117.2, C119.2, J4.5, J5.3, J5.29, J5.36, J9.2 (D2S), J9.5 (D1S), J9.8 (D0S), J9.11 (CKS), J9.17 (GND), J9.SH, U20.A16 (IO_L9P_T1_DQS_AD3P_35), U20.A17 (IO_L9N_T1_DQS_AD3N_35), U20.A18 (IO_L10P_T1_AD11P_35), U20.A19 (IO_L10N_T1_AD11N_35), U20.A20 (VCCO_35[7]), U20.A21 (IO_L15P_T2_DQS_AD12P_35), U20.A22 (IO_L15N_T2_DQS_AD12N_35), U20.B15 (IO_L7N_T1_AD2N_35), U20.B16 (IO_L8P_T1_AD10P_35), U20.B17 (IO_L8N_T1_AD10N_35), U20.B19 (IO_L13P_T2_MRCC_35), U20.B20 (IO_L13N_T2_MRCC_35), U20.B21 (IO_L18P_T2_AD13P_35), U20.B22 (IO_L18N_T2_AD13N_35), U20.C15 (IO_L7P_T1_AD2P_35), U20.C16 (VCCO_35[7]), U20.C17 (IO_L11P_T1_SRCC_35), U20.C18 (IO_L11N_T1_SRCC_35), U20.C19 (IO_L12N_T1_MRCC_35), U20.C20 (IO_L14N_T2_AD4N_SRCC_35), U20.C22 (IO_L16N_T2_35), U20.D15 (IO_L3N_T0_DQS_AD1N_35), U20.D16 (IO_L2P_T0_AD8P_35), U20.D17 (IO_L2N_T0_AD8N_35), U20.D18 (IO_L12P_T1_MRCC_35), U20.D19 (VCCO_35[7]), U20.D20 (IO_L14P_T2_AD4P_SRCC_35), U20.D21 (IO_L17N_T2_AD5N_35), U20.D22 (IO_L16P_T2_35), U20.E15 (IO_L3P_T0_DQS_AD1P_35), U20.E16 (IO_L1N_T0_AD0N_35), U20.E18 (IO_L5N_T0_AD9N_35), U20.E19 (IO_L21P_T3_DQS_AD14P_35), U20.E20 (IO_L21N_T3_DQS_AD14N_35), U20.E21 (IO_L17P_T2_AD5P_35), U20.E22 (VCCO_35[7]), U20.F15 (VCCO_35[7]), U20.F16 (IO_L1P_T0_AD0P_35), U20.F17 (IO_L6N_T0_VREF_35), U20.F18 (IO_L5P_T0_AD9P_35), U20.F19 (IO_L20N_T3_AD6N_35), U20.F21 (IO_L23P_T3_35), U20.F22 (IO_L23N_T3_35), U20.G15 (IO_L4P_T0_35), U20.G16 (IO_L4N_T0_35), U20.G17 (IO_L6P_T0_35), U20.G18 (VCCO_35[7]), U20.G19 (IO_L20P_T3_AD6P_35), U20.G20 (IO_L22P_T3_AD7P_35), U20.G21 (IO_L22N_T3_AD7N_35), U20.G22 (IO_L24N_T3_AD15N_35), U20.H15 (IO_0_34), U20.H17 (IO_0_35), U20.H18 (IO_25_35), U20.H19 (IO_L19P_T3_35), U20.H20 (IO_L19N_T3_VREF_35), U20.H21 (VCCO_35[7]), U20.H22 (IO_L24P_T3_AD15P_35), U20.J15 (IO_L1P_T0_34), U20.J16 (IO_L2P_T0_34), U20.J17 (IO_L2N_T0_34), U20.J18 (IO_L7P_T1_34), U20.J20 (IO_L9P_T1_DQS_34), U20.J21 (IO_L8P_T1_34), U20.J22 (IO_L8N_T1_34), U20.K15 (IO_L1N_T0_34), U20.K16 (IO_L3P_T0_DQS_PUDC_B_34), U20.K17 (VCCO_34[6]), U20.K18 (IO_L7N_T1_34), U20.K19 (IO_L11P_T1_SRCC_34), U20.K20 (IO_L11N_T1_SRCC_34), U20.K21 (IO_L9N_T1_DQS_34), U20.L16 (IO_L3N_T0_DQS_34), U20.L17 (IO_L4P_T0_34), U20.L18 (IO_L12P_T1_MRCC_34), U20.L19 (IO_L12N_T1_MRCC_34), U20.L20 (VCCO_34[6]), U20.L21 (IO_L10P_T1_34), U20.L22 (IO_L10N_T1_34), U20.M15 (IO_L6P_T0_34), U20.M16 (IO_L6N_T0_VREF_34), U20.M17 (IO_L4N_T0_34), U20.M19 (IO_L13P_T2_MRCC_34), U20.M20 (IO_L13N_T2_MRCC_34), U20.M21 (IO_L15P_T2_DQS_34), U20.M22 (IO_L15N_T2_DQS_34), U20.N15 (IO_L19P_T3_34), U20.N16 (VCCO_34[6]), U20.N17 (IO_L5P_T0_34), U20.N18 (IO_L5N_T0_34), U20.N19 (IO_L14P_T2_SRCC_34), U20.N20 (IO_L14N_T2_SRCC_34), U20.N22 (IO_L16P_T2_34), U20.P15 (IO_L19N_T3_VREF_34), U20.P16 (IO_L24P_T3_34), U20.P17 (IO_L20P_T3_34), U20.P18 (IO_L20N_T3_34), U20.P19 (VCCO_34[6]), U20.P20 (IO_L18P_T2_34), U20.P21 (IO_L18N_T2_34), U20.P22 (IO_L16N_T2_34), U20.R15 (IO_25_34), U20.R16 (IO_L24N_T3_34), U20.R18 (IO_L23P_T3_34), U20.R19 (IO_L22P_T3_34), U20.R20 (IO_L17P_T2_34), U20.R21 (IO_L17N_T2_34), U20.R22 (VCCO_34[6]), U20.T15 (VCCO_34[6]), U20.T16 (IO_L21P_T3_DQS_34), U20.T17 (IO_L21N_T3_DQS_34), U20.T18 (IO_L23N_T3_34), U20.T19 (IO_L22N_T3_34), U21.1 (GND)
GPRSrst: U20.AA11 (IO_L8P_T1_13)
HDMI_B_N: J9.3 (D2-), U20.AA6 (IO_L14N_T2_SRCC_13)
HDMI_B_P: J9.1 (D2+), U20.AA7 (IO_L14P_T2_SRCC_13)
HDMI_CEC: J9.13 (CEC), U20.W5 (IO_L24N_T3_13)
HDMI_CLK_N: J9.12 (CK-), U20.AB1 (IO_L15N_T2_DQS_13)
HDMI_CLK_P: J9.10 (CK+), U20.AB2 (IO_L15P_T2_DQS_13)
HDMI_G_N: J9.6 (D1-), U20.AB6 (IO_L17N_T2_13)
HDMI_G_P: J9.4 (D1+), U20.AB7 (IO_L17P_T2_13)
HDMI_HEAC_N: J9.19 (HPD), U20.AA4 (IO_L18N_T2_13)
HDMI_HEAC_P: J9.14 (UTILITY), U20.Y4 (IO_L18P_T2_13)
HDMI_R_N: J9.9 (D0-), U20.AB4 (IO_L16N_T2_13)
HDMI_R_P: J9.7 (D0+), U20.AB5 (IO_L16P_T2_13)
HS: J5.32
I2C5_HDMI_SCLK: J9.15 (SCL), R83.2, U21.6 (SCL2)
I2C5_HDMI_SDA: J9.16 (SDA), R82.2, U21.5 (SDA2)
I2C33_HDMI_SCLK: U20.Y5 (IO_L13N_T2_MRCC_13), U21.3 (SCL1)
I2C33_HDMI_SDA: U20.Y6 (IO_L13P_T2_MRCC_13), U21.4 (SDA1)
LCD_D0: J5.5
LCD_D1: J5.6
LCD_D2: J5.7
LCD_D3: J5.8
LCD_D4: J5.9
LCD_D5: J5.10
LCD_D6: J5.11
LCD_D7: J5.12
LCD_D8: J5.13
LCD_D9: J5.14
LCD_D10: J5.15
LCD_D11: J5.16
LCD_D12: J5.17
LCD_D13: J5.18
LCD_D14: J5.19
LCD_D15: J5.20
LCD_D16: J5.21
LCD_D17: J5.22
LCD_D18: J5.23
LCD_D19: J5.24
LCD_D20: J5.25
LCD_D21: J5.26
LCD_D22: J5.27
LCD_D23: J5.28
LEDA: J5.2
LEDK: J5.1
unnamed: R34.1, U21.7 (VREF2), U21.8 (EN)
unnamed: R34.2, R81.1
PCM_CLK: U20.R6 (IO_L19P_T3_13)
PCM_DIN: U20.U4 (IO_L20N_T3_13)
PCM_OUT: U20.T4 (IO_L20P_T3_13)
PCM_SYNC: U20.T6 (IO_L19N_T3_VREF_13)
PMOD1: U20.U7 (IO_25_13)
PMOD2: U20.R7 (IO_0_13)
PMOD3: U20.V9 (IO_L1N_T0_13)
PMOD4: U20.W8 (IO_L2N_T0_13)
PMOD5: U20.V10 (IO_L1P_T0_13)
PMOD6: U20.V8 (IO_L2P_T0_13)
PMOD7: U20.W11 (IO_L3P_T0_DQS_13)
PMOD8: U20.W10 (IO_L3N_T0_DQS_13)
PWRKEY: U20.AB11 (IO_L8N_T1_13)
Pclk: J5.30
RST: J5.37
SCL: J5.39
SDA: J5.40
T_INT: J4.2
T_RST: J4.1
T_SCL: J4.3
T_SDA: J4.4
USBH_D_N: U20.AA8 (IO_L11N_T1_SRCC_13)
USBH_D_P: U20.AA9 (IO_L11P_T1_SRCC_13)
VS: J5.33

Notes on the sheet:
Pmod 0
PCM input from A7670G
It seems all IO on this chip is HR (High-range) which includes TMDS_33 (the physical standard for HDMI)
_ | | | | | | | | -
LCD FPC pins
A7670G Interface
_ | | | | | | | | | | | | -
Touchscreen I2C pins
_ | | -
LCD and Status LEDs
_ | | | -
Pmod 1
HDMI interface
