SunnyYoshimitsu/CelestiCall/Schematic & PCB (pending fixing)/zynqPCB-master/USB.kicad_sch

## KiCad design Schematic & PCB (pending fixing)/zynqPCB-master/USB.kicad_sch (2024-07-29)

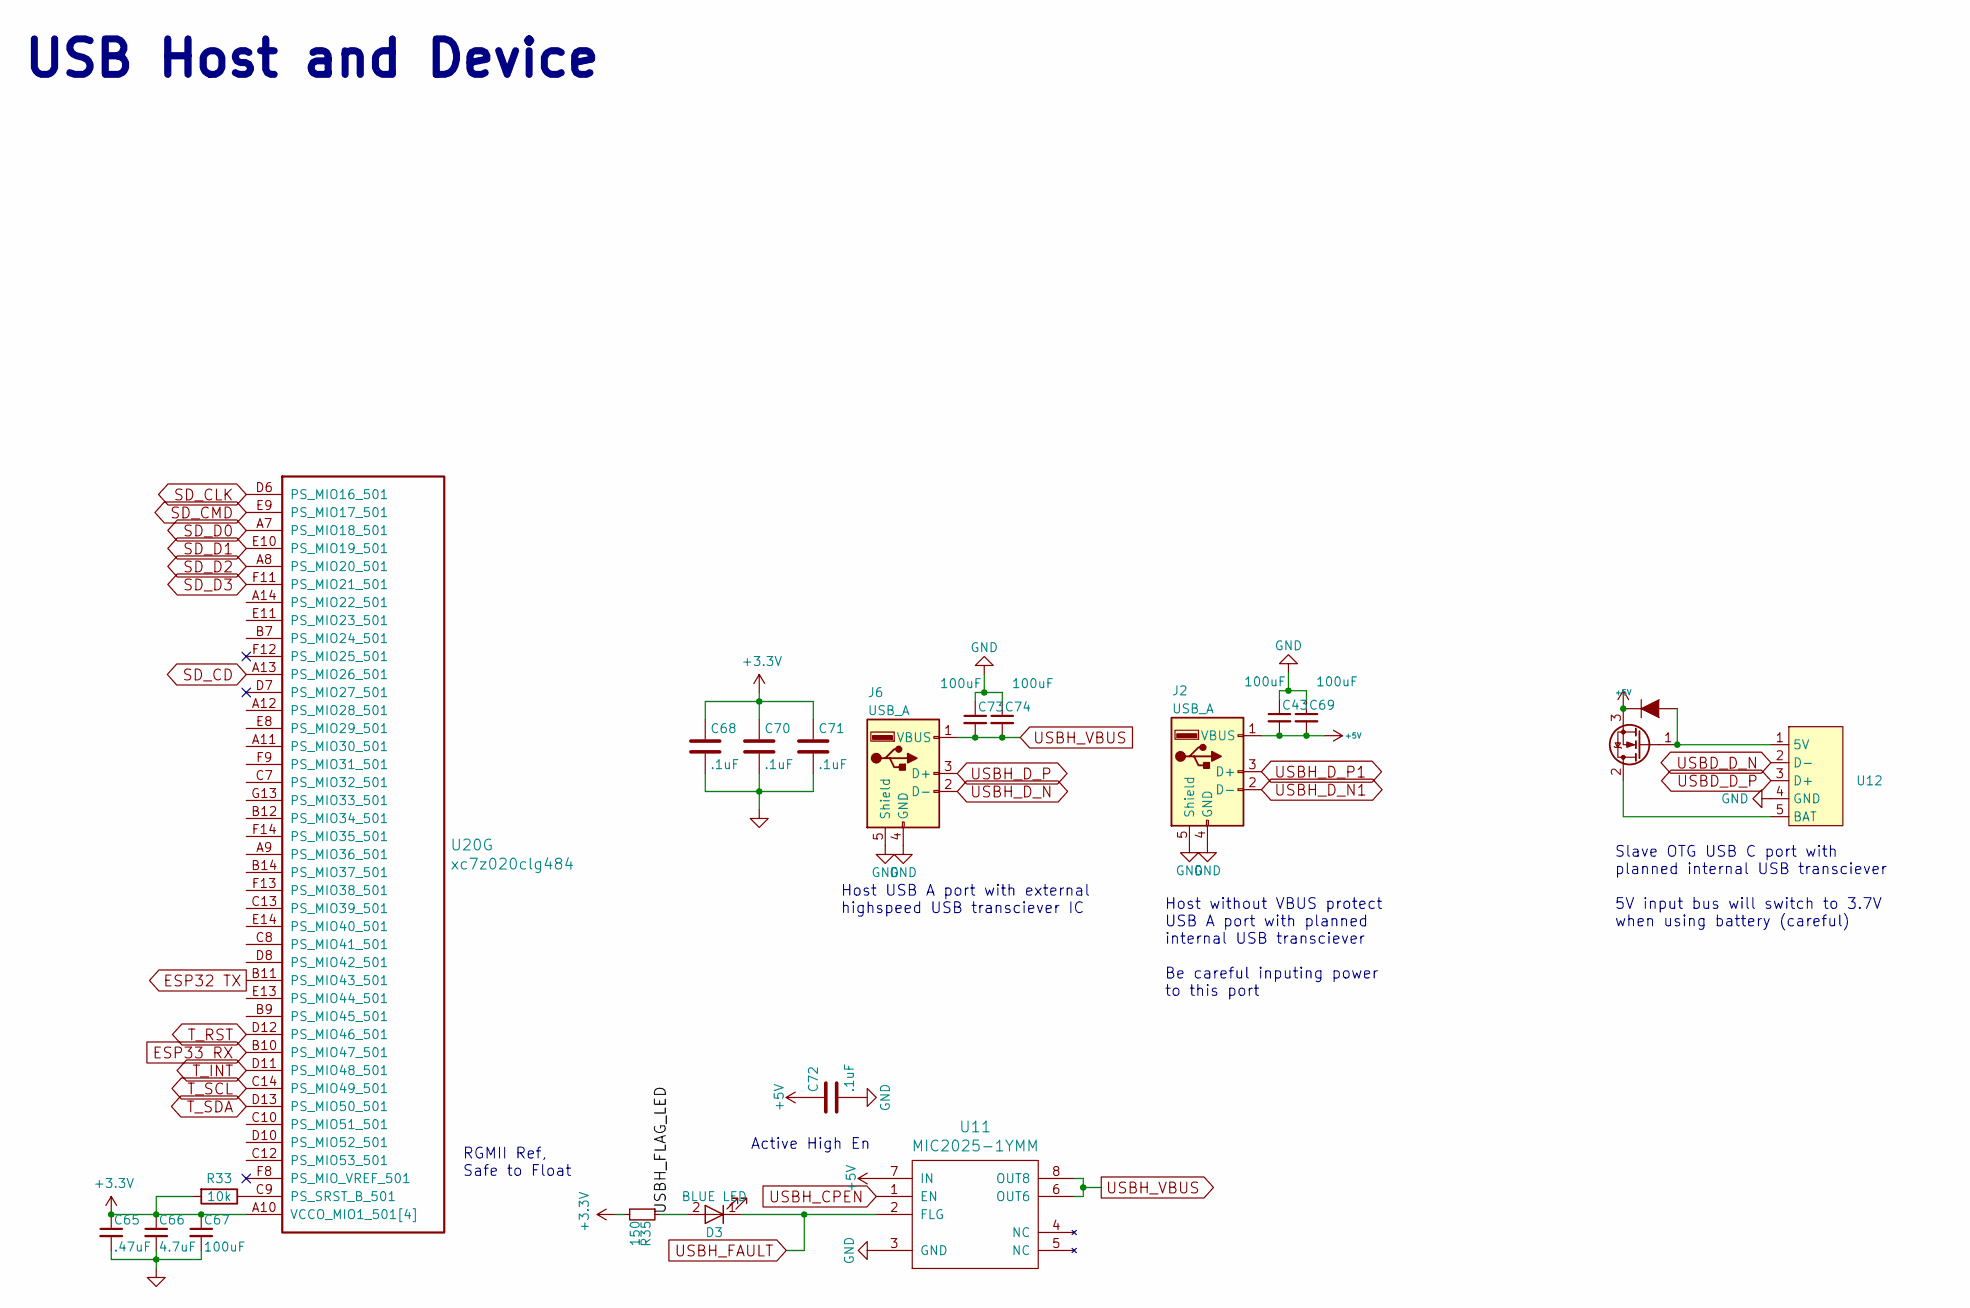
[picture p76: schematic USB.kicad_sch]

Parts:
C43, C67, C69, C73, C74: 100uF; C_1210_3225Metric; MPN JMK325ABJ107MM-P
C65: .47uF; C_0402_1005Metric; MPN CC0402KRX5R5BB474
C66: 4.7uF; C_0402_1005Metric; MPN GRM155R60G475ME47D
C68, C70, C71, C72: .1uF; C_0402_1005Metric; MPN CC0402KRX7R6BB104
D3: BLUE LED; C_0603_1608Metric; MPN VLMB1300-GS08
J2, J6: USB_A; USB-A-Receptacle-FCI_87583; MPN 87583-2010RLF
Q1: NDT452AP; SOT-223-3_TabPin2
R33: 10k; R_0402_1005Metric; MPN RC0402FR-0710KL
R35: 150; R_0402_1005Metric; MPN RC0402FR-07150RL
S8KC-13: D; D_SMC
U11: MIC2025-1YMM; SOP65P490X110-8N; MPN MIC2025-1YMM-TR
U12: Micro Lipo
U20: xc7z020clg484; BGA-484_19.0x19.0mm_Layout22x22_P0.80mm_dia0.40mm; MPN XC7Z020-1CLG484C

Connections:
+3.3V: C65.1, C66.1, C67.1, C68.1, C70.1, C71.1, R33.2, R35.2, U20.A10 (VCCO_MIO1_501[4]), U20.B13 (VCCO_MIO1_501[4]), U20.D9 (VCCO_MIO1_501[4]), U20.E12 (VCCO_MIO1_501[4])
+5V: C43.2, C69.2, C72.1, J2.1 (VBUS), Q1.3 (S), S8KC-13.1 (K), U11.7 (IN)
ESP32 TX: U20.B11 (PS_MIO43_501)
ESP33 RX: U20.B10 (PS_MIO47_501)
GND: C43.1, C65.2, C66.2, C67.2, C68.2, C69.1, C70.2, C71.2, C72.2, C73.1, C74.1, J2.4 (GND), J2.5 (Shield), J6.4 (GND), J6.5 (Shield), U11.3 (GND), U12.4 (GND)
unnamed: Q1.1 (G), S8KC-13.2 (A), U12.1 (5V)
unnamed: Q1.2 (D), U12.5 (BAT)
unnamed: R33.1, U20.C9 (PS_SRST_B_501)
SD_CD: U20.A13 (PS_MIO26_501)
SD_CLK: U20.D6 (PS_MIO16_501)
SD_CMD: U20.E9 (PS_MIO17_501)
SD_D0: U20.A7 (PS_MIO18_501)
SD_D1: U20.E10 (PS_MIO19_501)
SD_D2: U20.A8 (PS_MIO20_501)
SD_D3: U20.F11 (PS_MIO21_501)
T_INT: U20.D11 (PS_MIO48_501)
T_RST: U20.D12 (PS_MIO46_501)
T_SCL: U20.C14 (PS_MIO49_501)
T_SDA: U20.D13 (PS_MIO50_501)
USBD_D_N: U12.2 (D-)
USBD_D_P: U12.3 (D+)
USBH_CPEN: U11.1 (EN)
USBH_D_N: J6.2 (D-)
USBH_D_N1: J2.2 (D-)
USBH_D_P: J6.3 (D+)
USBH_D_P1: J2.3 (D+)
USBH_FAULT: D3.1 (K), U11.2 (FLG)
USBH_FLAG_LED: D3.2 (A), R35.1
USBH_VBUS: C73.2, C74.2, J6.1 (VBUS), U11.6 (OUT6), U11.8 (OUT8)

Notes on the sheet:
Host without VBUS protect USB A port with planned internal USB transciever Be careful inputing power to this port
RGMII Ref, Safe to Float
Active High En
USB Host and Device
Slave OTG USB C port with planned internal USB transciever 5V input bus will switch to 3.7V when using battery (careful)
Host USB A port with external highspeed USB transciever IC
