SunnyYoshimitsu/CelestiCall/Schematic & PCB (pending fixing)/zynqPCB-master/comm_sch.kicad_sch

## KiCad design Schematic & PCB (pending fixing)/zynqPCB-master/comm_sch.kicad_sch (2024-07-29)

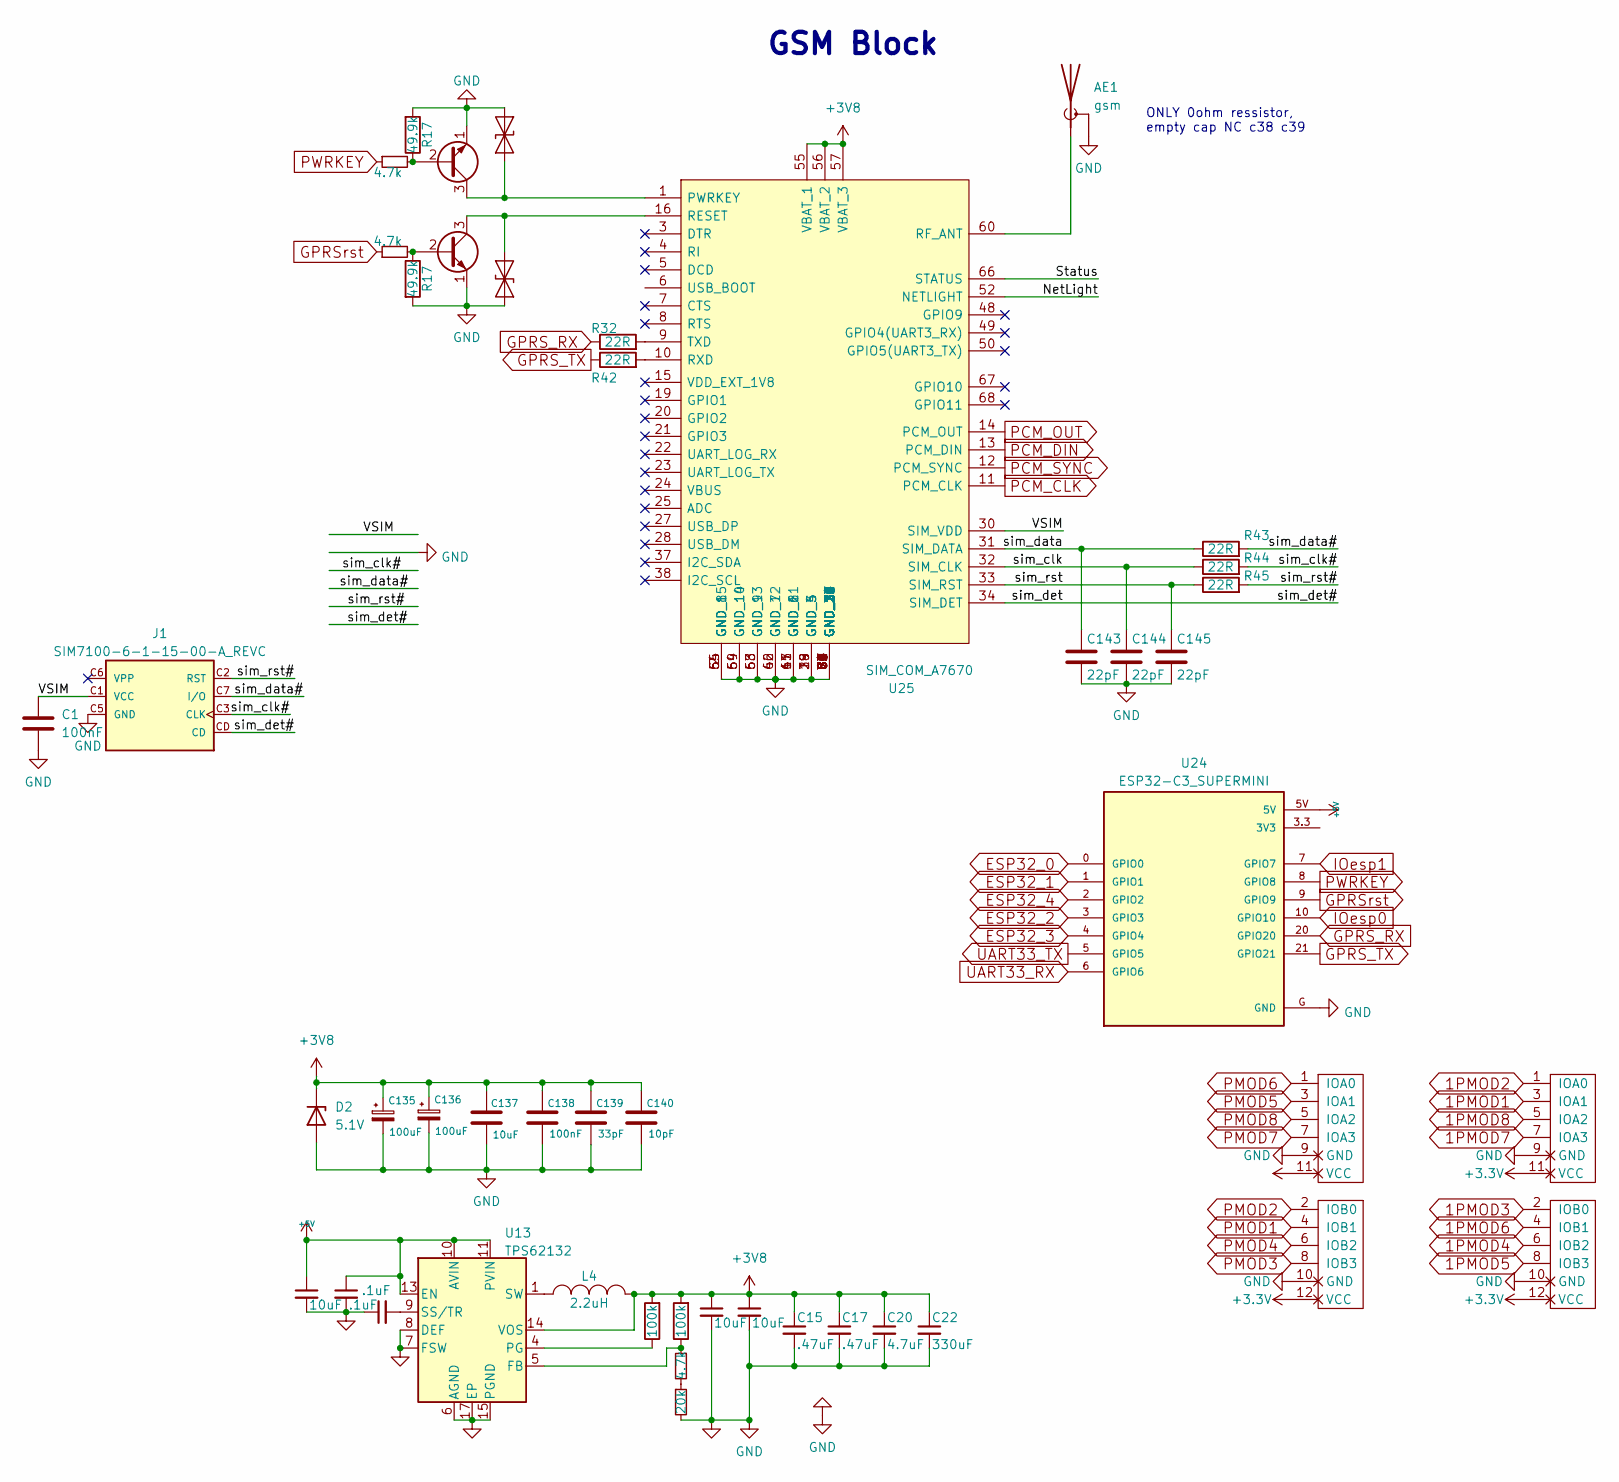
[picture p77: schematic comm_sch.kicad_sch]

Parts:
AE1: gsm; IPEX
C1, C138: 100nF; C_0805_2012Metric
C3: 10uF; C_0603_1608Metric; MPN GRM188R61A106KE69J
C15, C17: .47uF; C_0402_1005Metric; MPN CC0402KRX5R5BB474
C16: .1uF; C_0402_1005Metric; MPN CC0402KRX7R6BB104
C20: 4.7uF; C_0402_1005Metric; MPN GRM155R60G475ME47D
C22: 330uF; C_1206_3216Metric; MPN F950G337MAAAQ2
C135, C136: 100uF; CP_EIA-6032-15_Kemet-U
C137: 10uF; C_0805_2012Metric
C139: 33pF; C_0805_2012Metric
C140: 10pF; C_0805_2012Metric
C143, C144, C145: 22pF; R_0805_2012Metric
D2: 5.1V; D_SOD-123
D10, D11: ESD9B5.0ST5G; D_SOD-923
J1: SIM7100-6-1-15-00-A_REVC; nanoSIM; PARTREV C
L4: 2.2uH; C_1812_4532Metric; MPN LQH43PN2R2M26L
PMOD1: PMOD-Host-x2-GPIO; SAMTEC-SMH-106-02-X-D
Q2, Q11: MMBTA14-7-F; SOT-23-3
R5: 100k; R_0402_1005Metric; MPN RC0402FR-07100KL
R8, R9: 4.7k; R_0402_1005Metric; MPN RC0402JR-074K7L
R17: 49.9k; R_0402_1005Metric; MPN RC0402FR-0749K9L
R32, R42, R43, R44, R45: 22R; R_0805_2012Metric
R91: 20k; R_0402_1005Metric; MPN RT0402BRD0720KL
U13: TPS62132; VQFN-16-1EP_3x3mm_P0.5mm_EP1.68x1.68mm_ThermalVias
U24: ESP32-C3_SUPERMINI; MODULE_ESP32-C3_SUPERMINI
U25: SIM_COM_A7670; A7670C; Manufacturer_Part_Number SIM COM A7670

Connections:
1PMOD1: PMOD1.3 (IOA1)
1PMOD2: PMOD1.1 (IOA0)
1PMOD3: PMOD1.2 (IOB0)
1PMOD4: PMOD1.6 (IOB2)
1PMOD5: PMOD1.8 (IOB3)
1PMOD6: PMOD1.4 (IOB1)
1PMOD7: PMOD1.7 (IOA3)
1PMOD8: PMOD1.5 (IOA2)
+3.3V: PMOD1.11 (VCC), PMOD1.12 (VCC)
+3V8: C3.1, C15.1, C17.1, C20.1, C22.1, C135.1, C136.1, C137.1, C138.1, C139.1, C140.1, D2.1 (K), L4.2, R5.2, U13.14 (VOS), U25.55 (VBAT_1), U25.56 (VBAT_2), U25.57 (VBAT_3)
+5V: C3.1, C16.1, U13.10 (AVIN), U13.11 (PVIN), U13.12 (PVIN), U13.13 (EN), U24.5V
ESP32_0: U24.0 (GPIO0)
ESP32_1: U24.1 (GPIO1)
ESP32_2: U24.3 (GPIO3)
ESP32_3: U24.4 (GPIO4)
ESP32_4: U24.2 (GPIO2)
GND: AE1.2 (Shield), AE1.3 (Shield), C1.2, C3.2, C15.2, C16.1, C16.2, C17.2, C20.2, C22.2, C135.2, C136.2, C137.2, C138.2, C139.2, C140.2, C143.2, C144.2, C145.2, D2.2 (A), D10.1 (A1), D11.1 (A1), J1.1 (GND), J1.C5 (GND), PMOD1.9 (GND), PMOD1.10 (GND), Q2.1 (E), Q11.1 (E), R17.2, R91.2, U13.6 (AGND), U13.7 (FSW), U13.8 (DEF), U13.15 (PGND), U13.16 (PGND), U13.17 (EP), U24.G (GND), U25.2 (GND_1), U25.17 (GND_2), U25.18 (GND_3), U25.29 (GND_4), U25.39 (GND_5), U25.45 (GND_6), U25.46 (GND_7), U25.54 (GND_8), U25.58 (GND_9), U25.59 (GND_10), U25.61 (GND_11), U25.62 (GND_12), U25.63 (GND_13), U25.64 (GND_14), U25.65 (GND_15), U25.69 (GND_16), U25.70 (GND_17), U25.71 (GND_18), U25.72 (GND_19), U25.73 (GND_20), U25.74 (GND_21), U25.75 (GND_22), U25.76 (GND_23), U25.77 (GND_24), U25.78 (GND_25), U25.79 (GND_26), U25.80 (GND_27), U25.81 (GND_28), U25.82 (GND_29), U25.83 (GND_30), U25.84 (GND_31), U25.85 (GND_32), U25.86 (GND_33), U25.87 (GND_34), U25.88 (GND_35)
GPRS_RX: R32.1, U24.20 (GPIO20)
GPRS_TX: R42.1, U24.21 (GPIO21)
GPRSrst: R8.1, U24.9 (GPIO9)
IOesp0: U24.10 (GPIO10)
IOesp1: U24.7 (GPIO7)
unnamed: AE1.1 (A), U25.60 (RF_ANT)
unnamed: C16.2, U13.9 (SS/TR)
unnamed: D10.2 (A2), Q2.3 (C), U25.1 (PWRKEY)
unnamed: D11.2 (A2), Q11.3 (C), U25.16 (RESET)
unnamed: L4.1, U13.1 (SW), U13.2 (SW), U13.3 (SW)
unnamed: Q2.2 (B), R8.2, R17.1
unnamed: Q11.2 (B), R8.2, R17.1
unnamed: R5.1, R9.1, U13.4 (PG), U13.5 (FB)
unnamed: R9.2, R91.1
unnamed: R32.2, U25.9 (TXD)
unnamed: R42.2, U25.10 (RXD)
unnamed: U25.26 (NC_1), U25.41 (NC_5), U25.42 (NC_6), U25.43 (NC_7), U25.44 (NC_8)
unnamed: U25.35 (NC_2), U25.51 (NC_10)
unnamed: U25.36 (NC_3), U25.53 (NC_11)
unnamed: U25.40 (NC_4), U25.47 (NC_9)
NetLight: U25.52 (NETLIGHT)
PCM_CLK: U25.11 (PCM_CLK)
PCM_DIN: U25.13 (PCM_DIN)
PCM_OUT: U25.14 (PCM_OUT)
PCM_SYNC: U25.12 (PCM_SYNC)
PMOD1: PMOD1.4 (IOB1)
PMOD2: PMOD1.2 (IOB0)
PMOD3: PMOD1.8 (IOB3)
PMOD4: PMOD1.6 (IOB2)
PMOD5: PMOD1.3 (IOA1)
PMOD6: PMOD1.1 (IOA0)
PMOD7: PMOD1.7 (IOA3)
PMOD8: PMOD1.5 (IOA2)
PWRKEY: R8.1, U24.8 (GPIO8)
Status: U25.66 (STATUS)
UART33_RX: U24.6 (GPIO6)
UART33_TX: U24.5 (GPIO5)
VSIM: C1.1, J1.C1 (VCC), U25.30 (SIM_VDD)
sim_clk: C144.1, R44.1, U25.32 (SIM_CLK)
sim_clk#: J1.C3 (CLK), R44.2
sim_data: C143.1, R43.1, U25.31 (SIM_DATA)
sim_data#: J1.C7 (I/O), R43.2
sim_det: J1.CD, U25.34 (SIM_DET)
sim_rst: C145.1, R45.1, U25.33 (SIM_RST)
sim_rst#: J1.C2 (RST), R45.2

Notes on the sheet:
ONLY 0ohm ressistor, empty cap NC c38 c39
GSM Block
