SunnyYoshimitsu/CelestiCall/Schematic & PCB (pending fixing)/zynqPCB-master/hdmi.sch

## KiCad design Schematic & PCB (pending fixing)/zynqPCB-master/hdmi.sch (2024-05-25)

Schematic: hdmi.sch

Parts:
C108: 47uF; C_1210
C109, C110: 4.7uF; C_0805
C111, C112, C113, C114: .47uF; C_0603_1608Metric
C115: .01uF; C_0402
C151: 15pF; C_0402
U1: xc7a50tftg256; BGA-256
X1: FXO-HC73; 4-SMD
