SunnyYoshimitsu/CelestiCall/Schematic & PCB (pending fixing)/zynqPCB-master/sensors.kicad_sch

## KiCad design Schematic & PCB (pending fixing)/zynqPCB-master/sensors.kicad_sch (2024-06-05)

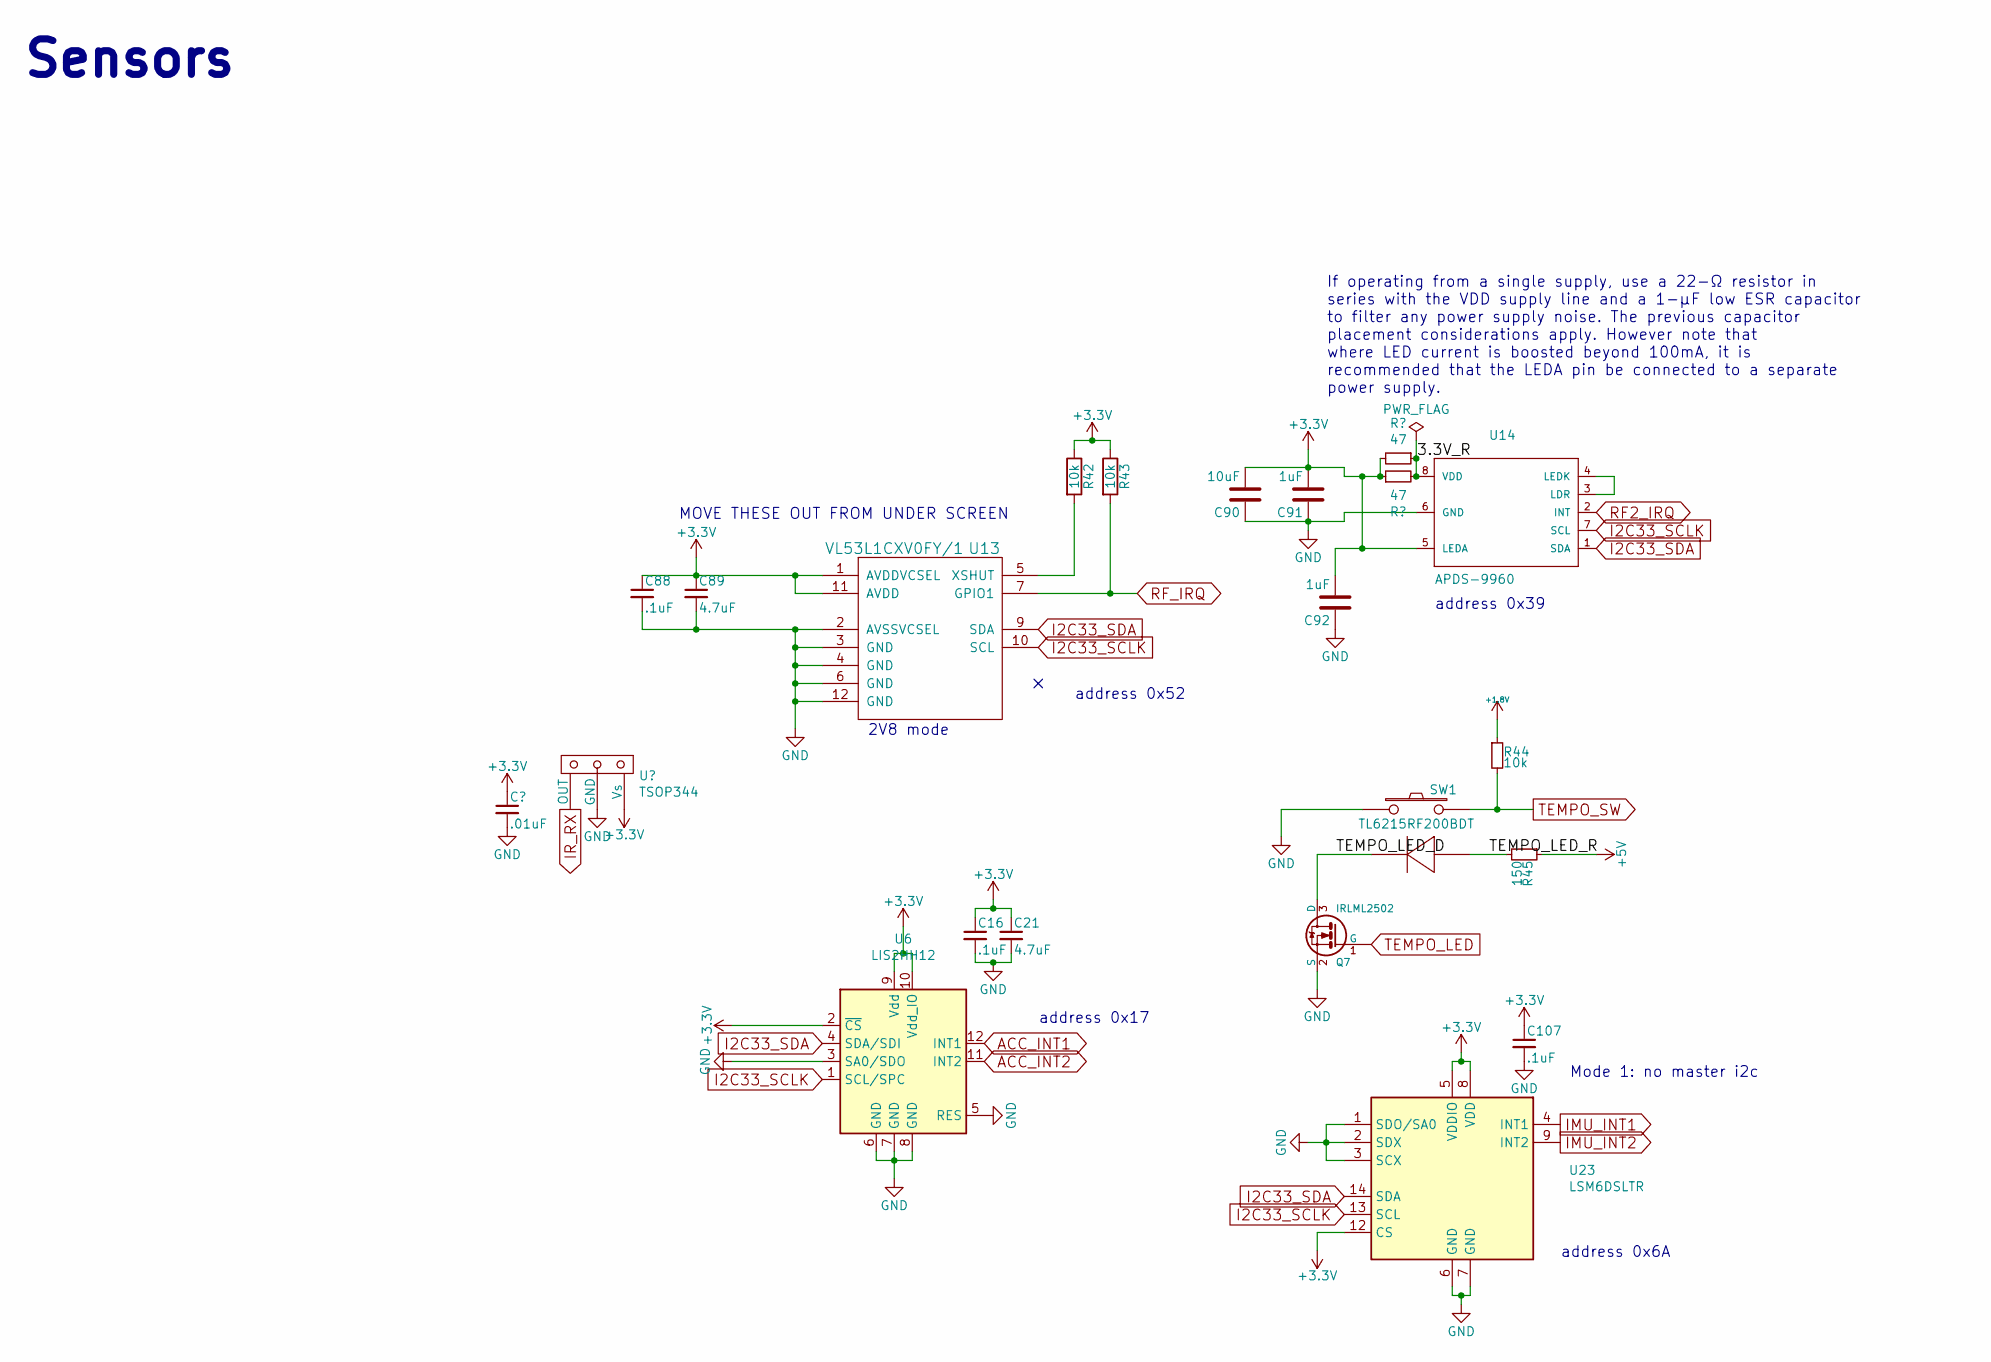
[picture p79: schematic sensors.kicad_sch]

Parts:
C16, C88, C107: .1uF; C_0402_1005Metric; MPN CC0402KRX7R6BB104
C21, C89: 4.7uF; C_0402_1005Metric; MPN GRM155R60G475ME47D
C90: 10uF; C_0603_1608Metric; MPN GRM188R61A106KE69J
C91, C92: 1uF; C_0402_1005Metric; MPN CC0402KRX5R6BB105
C111: .01uF; C_0402_1005Metric; MPN GRM155R71H103KA88J
Q7: IRLML2502; SOT-23; MPN IRLML2502TRPBF
R42, R43, R44: 10k; R_0402_1005Metric; MPN RC0402FR-0710KL
R45: 150; R_0402_1005Metric; MPN RC0402FR-07150RL
R84, R87: 47; R_0402_1005Metric; MPN RC0402JR-0747RL
SW1: TL6215RF200BDT; tl6215_right_angle; MPN TL6215RF200BDT
U6: LIS2HH12; LGA-12_2x2mm_P0.5mm; MPN LIS2HH12TR
U13: VL53L1CXV0FY/1; Optical_LGA12; MPN VL53L1CXV0FY/1
U14: APDS-9960; APDS_9960; MPN APDS-9960
U22: TSOP344; JUMPER_3PIN; MPN TSOP34438
U23: LSM6DSLTR; LGA-14_3x2.5mm_P0.5mm_LayoutBorder3x4y; MPN LSM6DSLTR

Connections:
3.3V_R: R84.1, R87.2, U14.8 (VDD)
+1.8V: R44.1
+3.3V: C16.1, C21.1, C88.1, C89.1, C90.2, C91.2, C92.2, C107.1, C111.1, R42.1, R43.1, R84.2, R87.1, U6.2 (~CS), U6.9 (Vdd), U6.10 (Vdd_IO), U13.1 (AVDDVCSEL), U13.11 (AVDD), U14.5 (LEDA), U22.3 (Vs), U23.5 (VDDIO), U23.8 (VDD), U23.12 (CS)
+5V: R45.1
ACC_INT1: U6.12 (INT1)
ACC_INT2: U6.11 (INT2)
GND: C16.2, C21.2, C88.2, C89.2, C90.1, C91.1, C92.1, C107.2, C111.2, Q7.2 (S), SW1.1, U6.3 (SA0/SDO), U6.5 (RES), U6.6 (GND), U6.7 (GND), U6.8 (GND), U13.2 (AVSSVCSEL), U13.3 (GND), U13.4 (GND), U13.6 (GND), U13.12 (GND), U14.6 (GND), U22.2 (GND), U23.1 (SDO/SA0), U23.2 (SDX), U23.3 (SCX), U23.6 (GND), U23.7 (GND)
I2C33_SCLK: U6.1 (SCL/SPC), U13.10 (SCL), U14.7 (SCL), U23.13 (SCL)
I2C33_SDA: U6.4 (SDA/SDI), U13.9 (SDA), U14.1 (SDA), U23.14 (SDA)
IMU_INT1: U23.4 (INT1)
IMU_INT2: U23.9 (INT2)
IR_RX: U22.1 (OUT)
unnamed: R42.2, U13.5 (XSHUT)
unnamed: U14.3 (LDR), U14.4 (LEDK)
RF2_IRQ: U14.2 (INT)
RF_IRQ: R43.2, U13.7 (GPIO1)
TEMPO_LED: Q7.1 (G)
TEMPO_LED_D: Q7.3 (D), SW1.3
TEMPO_LED_R: R45.2, SW1.4
TEMPO_SW: R44.2, SW1.2

Notes on the sheet:
2V8 mode
address 0x52
MOVE THESE OUT FROM UNDER SCREEN
address 0x6A
Mode 1: no master i2c
address 0x17
address 0x39
Sensors
If operating from a single supply, use a 22-Ω resistor in series with the VDD supply line and a 1-μF low ESR capacitor to filter any power supply noise. The previous capacitor placement considerations apply. However note that where LED current is boosted beyond 100mA, it is recommended that the LED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
