SunnyYoshimitsu/CelestiCall/Hardwares/IPModules/Sound Processor/Sound Processor.runs/synth_1/.Xil/I2S_Mic_Wrapper_propImpl.xdc

set_property SRC_FILE_INFO {cfile:{D:/CelestiCall/Hardwares/IPModules/Sound Processor/Sound Processor.srcs/constrs_1/new/xdcfix.xdc} rfile:{../../../Sound Processor.srcs/constrs_1/new/xdcfix.xdc} id:1} [current_design]
set_property src_info {type:XDC file:1 line:7 export:INPUT save:INPUT read:READ} [current_design]
set_property -dict { PACKAGE_PIN E3    IOSTANDARD LVCMOS33 } [get_ports { clk }]; #IO_L12P_T1_MRCC_35 Sch=clk100mhz
set_property src_info {type:XDC file:1 line:13 export:INPUT save:INPUT read:READ} [current_design]
set_property -dict { PACKAGE_PIN J15   IOSTANDARD LVCMOS33 } [get_ports { reset }]; #IO_L24N_T3_RS0_15 Sch=sw[0]
set_property src_info {type:XDC file:1 line:95 export:INPUT save:INPUT read:READ} [current_design]
set_property -dict { PACKAGE_PIN C17   IOSTANDARD LVCMOS33 } [get_ports { mclk }]; #IO_L20N_T3_A19_15 Sch=ja[1]
set_property src_info {type:XDC file:1 line:96 export:INPUT save:INPUT read:READ} [current_design]
set_property -dict { PACKAGE_PIN D18   IOSTANDARD LVCMOS33 } [get_ports { i2s_data }]; #IO_L21N_T3_DQS_A18_15 Sch=ja[2]
set_property src_info {type:XDC file:1 line:97 export:INPUT save:INPUT read:READ} [current_design]
set_property -dict { PACKAGE_PIN E18   IOSTANDARD LVCMOS33 } [get_ports { 1 }]; #IO_L21P_T3_DQS_15 Sch=ja[3]
set_property src_info {type:XDC file:1 line:212 export:INPUT save:INPUT read:READ} [current_design]
set_property -dict { PACKAGE_PIN A11   IOSTANDARD LVCMOS33 } [get_ports { data_o }]; #IO_L4N_T0_15 Sch=aud_pwm
set_property src_info {type:XDC file:1 line:213 export:INPUT save:INPUT read:READ} [current_design]
set_property -dict { PACKAGE_PIN D12   IOSTANDARD LVCMOS33 } [get_ports { 1 }]; #IO_L6P_T0_15 Sch=aud_sd
