SunnyYoshimitsu/CelestiCall/Hardwares/IPModules/HyperNovae GPU/HyperNovae GPU.gen/sources_1/ip/clk_wiz_0/clk_wiz_0.v

// file: clk_wiz_0.v
// (c) Copyright 2017-2018, 2023 Advanced Micro Devices, Inc. All rights reserved.
//
// This file contains confidential and proprietary information
// of AMD and is protected under U.S. and international copyright
// and other intellectual property laws.
//
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
// CRITICAL APPLICATIONS
// AMD products are not designed or intended to be fail-
// safe, or for use in any application requiring fail-safe
// performance, such as life-support or safety devices or
// systems, Class III medical devices, nuclear facilities,
// applications related to the deployment of airbags, or any
// other applications that could lead to death, personal
// injury, or severe property or environmental damage
// (individually and collectively, "Critical
// Applications"). Customer assumes the sole risk and
// liability of any use of AMD products in Critical
// Applications, subject only to applicable laws and
// regulations governing limitations on product liability.
//
// THIS COPYRIGHT NOTICE AND DISCLAIMER MUST BE RETAINED AS
// PART OF THIS FILE AT ALL TIMES.
//----------------------------------------------------------------------------
// User entered comments
//----------------------------------------------------------------------------
// None
//
//----------------------------------------------------------------------------
//  Output     Output      Phase    Duty Cycle   Pk-to-Pk     Phase
//   Clock     Freq (MHz)  (degrees)    (%)     Jitter (ps)  Error (ps)
//----------------------------------------------------------------------------
// clk_out1__25.00000______0.000______50.0______181.828____104.359
//
//----------------------------------------------------------------------------
// Input Clock   Freq (MHz)    Input Jitter (UI)
//----------------------------------------------------------------------------
// __primary_________100.000____________0.010

`timescale 1ps/1ps

(* CORE_GENERATION_INFO = "clk_wiz_0,clk_wiz_v6_0_13_0_0,{component_name=clk_wiz_0,use_phase_alignment=true,use_min_o_jitter=false,use_max_i_jitter=false,use_dyn_phase_shift=false,use_inclk_switchover=false,use_dyn_reconfig=false,enable_axi=0,feedback_source=FDBK_AUTO,PRIMITIVE=MMCM,num_out_clk=1,clkin1_period=10.000,clkin2_period=10.000,use_power_down=false,use_reset=true,use_locked=true,use_inclk_stopped=false,feedback_type=SINGLE,CLOCK_MGR_TYPE=NA,manual_override=false}" *)

module clk_wiz_0 
 (
  // Clock out ports
  output        clk_out1,
  // Status and control signals
  input         reset,
  output        locked,
 // Clock in ports
  input         clk_in1
 );

  clk_wiz_0_clk_wiz inst
  (
  // Clock out ports  
  .clk_out1(clk_out1),
  // Status and control signals               
  .reset(reset), 
  .locked(locked),
 // Clock in ports
  .clk_in1(clk_in1)
  );

endmodule
