SunnyYoshimitsu/CelestiCall/Hardwares/IPModules/Sound Processor/Sound Processor.gen/sources_1/ip/microblaze_mcs_0/bd_0/ip/ip_6/synth/bd_fc5c_0_lmb_bram_I_0.vhd

-- (c) Copyright 1986-2022 Xilinx, Inc. All Rights Reserved.
-- (c) Copyright 2022-2025 Advanced Micro Devices, Inc. All rights reserved.
-- 
-- This file contains confidential and proprietary information
-- of AMD and is protected under U.S. and international copyright
-- and other intellectual property laws.
-- 
-- DISCLAIMER
-- This disclaimer is not a license and does not grant any
-- rights to the materials distributed herewith. Except as
-- otherwise provided in a valid license issued to you by
-- AMD, and to the maximum extent permitted by applicable
-- law: (1) THESE MATERIALS ARE MADE AVAILABLE "AS IS" AND
-- WITH ALL FAULTS, AND AMD HEREBY DISCLAIMS ALL WARRANTIES
-- AND CONDITIONS, EXPRESS, IMPLIED, OR STATUTORY, INCLUDING
-- BUT NOT LIMITED TO WARRANTIES OF MERCHANTABILITY, NON-
-- INFRINGEMENT, OR FITNESS FOR ANY PARTICULAR PURPOSE; and
-- (2) AMD shall not be liable (whether in contract or tort,
-- including negligence, or under any other theory of
-- liability) for any loss or damage of any kind or nature
-- related to, arising under or in connection with these
-- materials, including for any direct, or any indirect,
-- special, incidental, or consequential loss or damage
-- (including loss of data, profits, goodwill, or any type of
-- loss or damage suffered as a result of any action brought
-- by a third party) even if such damage or loss was
-- reasonably foreseeable or AMD had been advised of the
-- possibility of the same.
-- 
-- CRITICAL APPLICATIONS
-- AMD products are not designed or intended to be fail-
-- safe, or for use in any application requiring fail-safe
-- performance, such as life-support or safety devices or
-- systems, Class III medical devices, nuclear facilities,
-- applications related to the deployment of airbags, or any
-- other applications that could lead to death, personal
-- injury, or severe property or environmental damage
-- (individually and collectively, "Critical
-- Applications"). Customer assumes the sole risk and
-- liability of any use of AMD products in Critical
-- Applications, subject only to applicable laws and
-- regulations governing limitations on product liability.
-- 
-- THIS COPYRIGHT NOTICE AND DISCLAIMER MUST BE RETAINED AS
-- PART OF THIS FILE AT ALL TIMES.
-- 
-- DO NOT MODIFY THIS FILE.

-- IP VLNV: xilinx.com:ip:blk_mem_gen:8.4
-- IP Revision: 7

LIBRARY ieee;
USE ieee.std_logic_1164.ALL;
USE ieee.numeric_std.ALL;

LIBRARY blk_mem_gen_v8_4_7;
USE blk_mem_gen_v8_4_7.blk_mem_gen_v8_4_7;

ENTITY bd_fc5c_0_lmb_bram_I_0 IS
  PORT (
    clka : IN STD_LOGIC;
    rsta : IN STD_LOGIC;
    ena : IN STD_LOGIC;
    wea : IN STD_LOGIC_VECTOR(3 DOWNTO 0);
    addra : IN STD_LOGIC_VECTOR(31 DOWNTO 0);
    dina : IN STD_LOGIC_VECTOR(31 DOWNTO 0);
    douta : OUT STD_LOGIC_VECTOR(31 DOWNTO 0);
    clkb : IN STD_LOGIC;
    rstb : IN STD_LOGIC;
    enb : IN STD_LOGIC;
    web : IN STD_LOGIC_VECTOR(3 DOWNTO 0);
    addrb : IN STD_LOGIC_VECTOR(31 DOWNTO 0);
    dinb : IN STD_LOGIC_VECTOR(31 DOWNTO 0);
    doutb : OUT STD_LOGIC_VECTOR(31 DOWNTO 0);
    rsta_busy : OUT STD_LOGIC;
    rstb_busy : OUT STD_LOGIC
  );
END bd_fc5c_0_lmb_bram_I_0;

ARCHITECTURE bd_fc5c_0_lmb_bram_I_0_arch OF bd_fc5c_0_lmb_bram_I_0 IS
  ATTRIBUTE DowngradeIPIdentifiedWarnings : STRING;
  ATTRIBUTE DowngradeIPIdentifiedWarnings OF bd_fc5c_0_lmb_bram_I_0_arch: ARCHITECTURE IS "yes";
  COMPONENT blk_mem_gen_v8_4_7 IS
    GENERIC (
      C_FAMILY : STRING;
      C_XDEVICEFAMILY : STRING;
      C_ELABORATION_DIR : STRING;
      C_INTERFACE_TYPE : INTEGER;
      C_AXI_TYPE : INTEGER;
      C_AXI_SLAVE_TYPE : INTEGER;
      C_USE_BRAM_BLOCK : INTEGER;
      C_ENABLE_32BIT_ADDRESS : INTEGER;
      C_CTRL_ECC_ALGO : STRING;
      C_HAS_AXI_ID : INTEGER;
      C_AXI_ID_WIDTH : INTEGER;
      C_MEM_TYPE : INTEGER;
      C_BYTE_SIZE : INTEGER;
      C_ALGORITHM : INTEGER;
      C_PRIM_TYPE : INTEGER;
      C_LOAD_INIT_FILE : INTEGER;
      C_INIT_FILE_NAME : STRING;
      C_INIT_FILE : STRING;
      C_USE_DEFAULT_DATA : INTEGER;
      C_DEFAULT_DATA : STRING;
      C_HAS_RSTA : INTEGER;
      C_RST_PRIORITY_A : STRING;
      C_RSTRAM_A : INTEGER;
      C_INITA_VAL : STRING;
      C_HAS_ENA : INTEGER;
      C_HAS_REGCEA : INTEGER;
      C_USE_BYTE_WEA : INTEGER;
      C_WEA_WIDTH : INTEGER;
      C_WRITE_MODE_A : STRING;
      C_WRITE_WIDTH_A : INTEGER;
      C_READ_WIDTH_A : INTEGER;
      C_WRITE_DEPTH_A : INTEGER;
      C_READ_DEPTH_A : INTEGER;
      C_ADDRA_WIDTH : INTEGER;
      C_HAS_RSTB : INTEGER;
      C_RST_PRIORITY_B : STRING;
      C_RSTRAM_B : INTEGER;
      C_INITB_VAL : STRING;
      C_HAS_ENB : INTEGER;
      C_HAS_REGCEB : INTEGER;
      C_USE_BYTE_WEB : INTEGER;
      C_WEB_WIDTH : INTEGER;
      C_WRITE_MODE_B : STRING;
      C_WRITE_WIDTH_B : INTEGER;
      C_READ_WIDTH_B : INTEGER;
      C_WRITE_DEPTH_B : INTEGER;
      C_READ_DEPTH_B : INTEGER;
      C_ADDRB_WIDTH : INTEGER;
      C_HAS_MEM_OUTPUT_REGS_A : INTEGER;
      C_HAS_MEM_OUTPUT_REGS_B : INTEGER;
      C_HAS_MUX_OUTPUT_REGS_A : INTEGER;
      C_HAS_MUX_OUTPUT_REGS_B : INTEGER;
      C_MUX_PIPELINE_STAGES : INTEGER;
      C_HAS_SOFTECC_INPUT_REGS_A : INTEGER;
      C_HAS_SOFTECC_OUTPUT_REGS_B : INTEGER;
      C_USE_SOFTECC : INTEGER;
      C_USE_ECC : INTEGER;
      C_EN_ECC_PIPE : INTEGER;
      C_READ_LATENCY_A : INTEGER;
      C_READ_LATENCY_B : INTEGER;
      C_HAS_INJECTERR : INTEGER;
      C_SIM_COLLISION_CHECK : STRING;
      C_COMMON_CLK : INTEGER;
      C_DISABLE_WARN_BHV_COLL : INTEGER;
      C_EN_SLEEP_PIN : INTEGER;
      C_USE_URAM : INTEGER;
      C_EN_RDADDRA_CHG : INTEGER;
      C_EN_RDADDRB_CHG : INTEGER;
      C_EN_DEEPSLEEP_PIN : INTEGER;
      C_EN_SHUTDOWN_PIN : INTEGER;
      C_EN_SAFETY_CKT : INTEGER;
      C_DISABLE_WARN_BHV_RANGE : INTEGER;
      C_COUNT_36K_BRAM : STRING;
      C_COUNT_18K_BRAM : STRING;
      C_EST_POWER_SUMMARY : STRING
    );
    PORT (
      clka : IN STD_LOGIC;
      rsta : IN STD_LOGIC;
      ena : IN STD_LOGIC;
      regcea : IN STD_LOGIC;
      wea : IN STD_LOGIC_VECTOR(3 DOWNTO 0);
      addra : IN STD_LOGIC_VECTOR(31 DOWNTO 0);
      dina : IN STD_LOGIC_VECTOR(31 DOWNTO 0);
      douta : OUT STD_LOGIC_VECTOR(31 DOWNTO 0);
      clkb : IN STD_LOGIC;
      rstb : IN STD_LOGIC;
      enb : IN STD_LOGIC;
      regceb : IN STD_LOGIC;
      web : IN STD_LOGIC_VECTOR(3 DOWNTO 0);
      addrb : IN STD_LOGIC_VECTOR(31 DOWNTO 0);
      dinb : IN STD_LOGIC_VECTOR(31 DOWNTO 0);
      doutb : OUT STD_LOGIC_VECTOR(31 DOWNTO 0);
      injectsbiterr : IN STD_LOGIC;
      injectdbiterr : IN STD_LOGIC;
      eccpipece : IN STD_LOGIC;
      sbiterr : OUT STD_LOGIC;
      dbiterr : OUT STD_LOGIC;
      rdaddrecc : OUT STD_LOGIC_VECTOR(31 DOWNTO 0);
      sleep : IN STD_LOGIC;
      deepsleep : IN STD_LOGIC;
      shutdown : IN STD_LOGIC;
      rsta_busy : OUT STD_LOGIC;
      rstb_busy : OUT STD_LOGIC;
      s_aclk : IN STD_LOGIC;
      s_aresetn : IN STD_LOGIC;
      s_axi_awid : IN STD_LOGIC_VECTOR(3 DOWNTO 0);
      s_axi_awaddr : IN STD_LOGIC_VECTOR(31 DOWNTO 0);
      s_axi_awlen : IN STD_LOGIC_VECTOR(7 DOWNTO 0);
      s_axi_awsize : IN STD_LOGIC_VECTOR(2 DOWNTO 0);
      s_axi_awburst : IN STD_LOGIC_VECTOR(1 DOWNTO 0);
      s_axi_awvalid : IN STD_LOGIC;
      s_axi_awready : OUT STD_LOGIC;
      s_axi_wdata : IN STD_LOGIC_VECTOR(31 DOWNTO 0);
      s_axi_wstrb : IN STD_LOGIC_VECTOR(3 DOWNTO 0);
      s_axi_wlast : IN STD_LOGIC;
      s_axi_wvalid : IN STD_LOGIC;
      s_axi_wready : OUT STD_LOGIC;
      s_axi_bid : OUT STD_LOGIC_VECTOR(3 DOWNTO 0);
      s_axi_bresp : OUT STD_LOGIC_VECTOR(1 DOWNTO 0);
      s_axi_bvalid : OUT STD_LOGIC;
      s_axi_bready : IN STD_LOGIC;
      s_axi_arid : IN STD_LOGIC_VECTOR(3 DOWNTO 0);
      s_axi_araddr : IN STD_LOGIC_VECTOR(31 DOWNTO 0);
      s_axi_arlen : IN STD_LOGIC_VECTOR(7 DOWNTO 0);
      s_axi_arsize : IN STD_LOGIC_VECTOR(2 DOWNTO 0);
      s_axi_arburst : IN STD_LOGIC_VECTOR(1 DOWNTO 0);
      s_axi_arvalid : IN STD_LOGIC;
      s_axi_arready : OUT STD_LOGIC;
      s_axi_rid : OUT STD_LOGIC_VECTOR(3 DOWNTO 0);
      s_axi_rdata : OUT STD_LOGIC_VECTOR(31 DOWNTO 0);
      s_axi_rresp : OUT STD_LOGIC_VECTOR(1 DOWNTO 0);
      s_axi_rlast : OUT STD_LOGIC;
      s_axi_rvalid : OUT STD_LOGIC;
      s_axi_rready : IN STD_LOGIC;
      s_axi_injectsbiterr : IN STD_LOGIC;
      s_axi_injectdbiterr : IN STD_LOGIC;
      s_axi_sbiterr : OUT STD_LOGIC;
      s_axi_dbiterr : OUT STD_LOGIC;
      s_axi_rdaddrecc : OUT STD_LOGIC_VECTOR(31 DOWNTO 0)
    );
  END COMPONENT blk_mem_gen_v8_4_7;
  ATTRIBUTE X_CORE_INFO : STRING;
  ATTRIBUTE X_CORE_INFO OF bd_fc5c_0_lmb_bram_I_0_arch: ARCHITECTURE IS "blk_mem_gen_v8_4_7,Vivado 2023.2";
  ATTRIBUTE CHECK_LICENSE_TYPE : STRING;
  ATTRIBUTE CHECK_LICENSE_TYPE OF bd_fc5c_0_lmb_bram_I_0_arch : ARCHITECTURE IS "bd_fc5c_0_lmb_bram_I_0,blk_mem_gen_v8_4_7,{}";
  ATTRIBUTE CORE_GENERATION_INFO : STRING;
  ATTRIBUTE CORE_GENERATION_INFO OF bd_fc5c_0_lmb_bram_I_0_arch: ARCHITECTURE IS "bd_fc5c_0_lmb_bram_I_0,blk_mem_gen_v8_4_7,{x_ipProduct=Vivado 2023.2,x_ipVendor=xilinx.com,x_ipLibrary=ip,x_ipName=blk_mem_gen,x_ipVersion=8.4,x_ipCoreRevision=7,x_ipLanguage=VERILOG,x_ipSimLanguage=MIXED,C_FAMILY=zynq,C_XDEVICEFAMILY=zynq,C_ELABORATION_DIR=./,C_INTERFACE_TYPE=0,C_AXI_TYPE=1,C_AXI_SLAVE_TYPE=0,C_USE_BRAM_BLOCK=1,C_ENABLE_32BIT_ADDRESS=1,C_CTRL_ECC_ALGO=NONE,C_HAS_AXI_ID=0,C_AXI_ID_WIDTH=4,C_MEM_TYPE=2,C_BYTE_SIZE=8,C_ALGORITHM=1,C_PRIM_TYPE=1,C_LOAD_INIT_FILE=0,C_INIT_FILE_NAME=" & 
"no_coe_file_loaded,C_INIT_FILE=bd_fc5c_0_lmb_bram_I_0.mem,C_USE_DEFAULT_DATA=0,C_DEFAULT_DATA=0,C_HAS_RSTA=1,C_RST_PRIORITY_A=CE,C_RSTRAM_A=0,C_INITA_VAL=0,C_HAS_ENA=1,C_HAS_REGCEA=0,C_USE_BYTE_WEA=1,C_WEA_WIDTH=4,C_WRITE_MODE_A=WRITE_FIRST,C_WRITE_WIDTH_A=32,C_READ_WIDTH_A=32,C_WRITE_DEPTH_A=32768,C_READ_DEPTH_A=32768,C_ADDRA_WIDTH=32,C_HAS_RSTB=1,C_RST_PRIORITY_B=CE,C_RSTRAM_B=0,C_INITB_VAL=0,C_HAS_ENB=1,C_HAS_REGCEB=0,C_USE_BYTE_WEB=1,C_WEB_WIDTH=4,C_WRITE_MODE_B=WRITE_FIRST,C_WRITE_WIDTH_B=3" & 
"2,C_READ_WIDTH_B=32,C_WRITE_DEPTH_B=32768,C_READ_DEPTH_B=32768,C_ADDRB_WIDTH=32,C_HAS_MEM_OUTPUT_REGS_A=0,C_HAS_MEM_OUTPUT_REGS_B=0,C_HAS_MUX_OUTPUT_REGS_A=0,C_HAS_MUX_OUTPUT_REGS_B=0,C_MUX_PIPELINE_STAGES=0,C_HAS_SOFTECC_INPUT_REGS_A=0,C_HAS_SOFTECC_OUTPUT_REGS_B=0,C_USE_SOFTECC=0,C_USE_ECC=0,C_EN_ECC_PIPE=0,C_READ_LATENCY_A=1,C_READ_LATENCY_B=1,C_HAS_INJECTERR=0,C_SIM_COLLISION_CHECK=ALL,C_COMMON_CLK=0,C_DISABLE_WARN_BHV_COLL=0,C_EN_SLEEP_PIN=0,C_USE_URAM=0,C_EN_RDADDRA_CHG=0,C_EN_RDADDRB_CHG=" & 
"0,C_EN_DEEPSLEEP_PIN=0,C_EN_SHUTDOWN_PIN=0,C_EN_SAFETY_CKT=1,C_DISABLE_WARN_BHV_RANGE=0,C_COUNT_36K_BRAM=32,C_COUNT_18K_BRAM=0,C_EST_POWER_SUMMARY=Estimated Power for IP     _     20.388 mW}";
  ATTRIBUTE X_INTERFACE_INFO : STRING;
  ATTRIBUTE X_INTERFACE_PARAMETER : STRING;
  ATTRIBUTE X_INTERFACE_INFO OF addra: SIGNAL IS "xilinx.com:interface:bram:1.0 BRAM_PORTA ADDR";
  ATTRIBUTE X_INTERFACE_INFO OF addrb: SIGNAL IS "xilinx.com:interface:bram:1.0 BRAM_PORTB ADDR";
  ATTRIBUTE X_INTERFACE_PARAMETER OF clka: SIGNAL IS "XIL_INTERFACENAME BRAM_PORTA, MEM_SIZE 131072, MEM_WIDTH 32, MEM_ECC NONE, MASTER_TYPE BRAM_CTRL, READ_WRITE_MODE READ_WRITE, READ_LATENCY 1";
  ATTRIBUTE X_INTERFACE_INFO OF clka: SIGNAL IS "xilinx.com:interface:bram:1.0 BRAM_PORTA CLK";
  ATTRIBUTE X_INTERFACE_PARAMETER OF clkb: SIGNAL IS "XIL_INTERFACENAME BRAM_PORTB, MEM_SIZE 131072, MEM_WIDTH 32, MEM_ECC NONE, MASTER_TYPE BRAM_CTRL, READ_WRITE_MODE READ_WRITE, READ_LATENCY 1";
  ATTRIBUTE X_INTERFACE_INFO OF clkb: SIGNAL IS "xilinx.com:interface:bram:1.0 BRAM_PORTB CLK";
  ATTRIBUTE X_INTERFACE_INFO OF dina: SIGNAL IS "xilinx.com:interface:bram:1.0 BRAM_PORTA DIN";
  ATTRIBUTE X_INTERFACE_INFO OF dinb: SIGNAL IS "xilinx.com:interface:bram:1.0 BRAM_PORTB DIN";
  ATTRIBUTE X_INTERFACE_INFO OF douta: SIGNAL IS "xilinx.com:interface:bram:1.0 BRAM_PORTA DOUT";
  ATTRIBUTE X_INTERFACE_INFO OF doutb: SIGNAL IS "xilinx.com:interface:bram:1.0 BRAM_PORTB DOUT";
  ATTRIBUTE X_INTERFACE_INFO OF ena: SIGNAL IS "xilinx.com:interface:bram:1.0 BRAM_PORTA EN";
  ATTRIBUTE X_INTERFACE_INFO OF enb: SIGNAL IS "xilinx.com:interface:bram:1.0 BRAM_PORTB EN";
  ATTRIBUTE X_INTERFACE_INFO OF rsta: SIGNAL IS "xilinx.com:interface:bram:1.0 BRAM_PORTA RST";
  ATTRIBUTE X_INTERFACE_INFO OF rstb: SIGNAL IS "xilinx.com:interface:bram:1.0 BRAM_PORTB RST";
  ATTRIBUTE X_INTERFACE_INFO OF wea: SIGNAL IS "xilinx.com:interface:bram:1.0 BRAM_PORTA WE";
  ATTRIBUTE X_INTERFACE_INFO OF web: SIGNAL IS "xilinx.com:interface:bram:1.0 BRAM_PORTB WE";
BEGIN
  U0 : blk_mem_gen_v8_4_7
    GENERIC MAP (
      C_FAMILY => "zynq",
      C_XDEVICEFAMILY => "zynq",
      C_ELABORATION_DIR => "./",
      C_INTERFACE_TYPE => 0,
      C_AXI_TYPE => 1,
      C_AXI_SLAVE_TYPE => 0,
      C_USE_BRAM_BLOCK => 1,
      C_ENABLE_32BIT_ADDRESS => 1,
      C_CTRL_ECC_ALGO => "NONE",
      C_HAS_AXI_ID => 0,
      C_AXI_ID_WIDTH => 4,
      C_MEM_TYPE => 2,
      C_BYTE_SIZE => 8,
      C_ALGORITHM => 1,
      C_PRIM_TYPE => 1,
      C_LOAD_INIT_FILE => 0,
      C_INIT_FILE_NAME => "no_coe_file_loaded",
      C_INIT_FILE => "bd_fc5c_0_lmb_bram_I_0.mem",
      C_USE_DEFAULT_DATA => 0,
      C_DEFAULT_DATA => "0",
      C_HAS_RSTA => 1,
      C_RST_PRIORITY_A => "CE",
      C_RSTRAM_A => 0,
      C_INITA_VAL => "0",
      C_HAS_ENA => 1,
      C_HAS_REGCEA => 0,
      C_USE_BYTE_WEA => 1,
      C_WEA_WIDTH => 4,
      C_WRITE_MODE_A => "WRITE_FIRST",
      C_WRITE_WIDTH_A => 32,
      C_READ_WIDTH_A => 32,
      C_WRITE_DEPTH_A => 32768,
      C_READ_DEPTH_A => 32768,
      C_ADDRA_WIDTH => 32,
      C_HAS_RSTB => 1,
      C_RST_PRIORITY_B => "CE",
      C_RSTRAM_B => 0,
      C_INITB_VAL => "0",
      C_HAS_ENB => 1,
      C_HAS_REGCEB => 0,
      C_USE_BYTE_WEB => 1,
      C_WEB_WIDTH => 4,
      C_WRITE_MODE_B => "WRITE_FIRST",
      C_WRITE_WIDTH_B => 32,
      C_READ_WIDTH_B => 32,
      C_WRITE_DEPTH_B => 32768,
      C_READ_DEPTH_B => 32768,
      C_ADDRB_WIDTH => 32,
      C_HAS_MEM_OUTPUT_REGS_A => 0,
      C_HAS_MEM_OUTPUT_REGS_B => 0,
      C_HAS_MUX_OUTPUT_REGS_A => 0,
      C_HAS_MUX_OUTPUT_REGS_B => 0,
      C_MUX_PIPELINE_STAGES => 0,
      C_HAS_SOFTECC_INPUT_REGS_A => 0,
      C_HAS_SOFTECC_OUTPUT_REGS_B => 0,
      C_USE_SOFTECC => 0,
      C_USE_ECC => 0,
      C_EN_ECC_PIPE => 0,
      C_READ_LATENCY_A => 1,
      C_READ_LATENCY_B => 1,
      C_HAS_INJECTERR => 0,
      C_SIM_COLLISION_CHECK => "ALL",
      C_COMMON_CLK => 0,
      C_DISABLE_WARN_BHV_COLL => 0,
      C_EN_SLEEP_PIN => 0,
      C_USE_URAM => 0,
      C_EN_RDADDRA_CHG => 0,
      C_EN_RDADDRB_CHG => 0,
      C_EN_DEEPSLEEP_PIN => 0,
      C_EN_SHUTDOWN_PIN => 0,
      C_EN_SAFETY_CKT => 1,
      C_DISABLE_WARN_BHV_RANGE => 0,
      C_COUNT_36K_BRAM => "32",
      C_COUNT_18K_BRAM => "0",
      C_EST_POWER_SUMMARY => "Estimated Power for IP     :     20.388 mW"
    )
    PORT MAP (
      clka => clka,
      rsta => rsta,
      ena => ena,
      regcea => '0',
      wea => wea,
      addra => addra,
      dina => dina,
      douta => douta,
      clkb => clkb,
      rstb => rstb,
      enb => enb,
      regceb => '0',
      web => web,
      addrb => addrb,
      dinb => dinb,
      doutb => doutb,
      injectsbiterr => '0',
      injectdbiterr => '0',
      eccpipece => '0',
      sleep => '0',
      deepsleep => '0',
      shutdown => '0',
      rsta_busy => rsta_busy,
      rstb_busy => rstb_busy,
      s_aclk => '0',
      s_aresetn => '0',
      s_axi_awid => STD_LOGIC_VECTOR(TO_UNSIGNED(0, 4)),
      s_axi_awaddr => STD_LOGIC_VECTOR(TO_UNSIGNED(0, 32)),
      s_axi_awlen => STD_LOGIC_VECTOR(TO_UNSIGNED(0, 8)),
      s_axi_awsize => STD_LOGIC_VECTOR(TO_UNSIGNED(0, 3)),
      s_axi_awburst => STD_LOGIC_VECTOR(TO_UNSIGNED(0, 2)),
      s_axi_awvalid => '0',
      s_axi_wdata => STD_LOGIC_VECTOR(TO_UNSIGNED(0, 32)),
      s_axi_wstrb => STD_LOGIC_VECTOR(TO_UNSIGNED(0, 4)),
      s_axi_wlast => '0',
      s_axi_wvalid => '0',
      s_axi_bready => '0',
      s_axi_arid => STD_LOGIC_VECTOR(TO_UNSIGNED(0, 4)),
      s_axi_araddr => STD_LOGIC_VECTOR(TO_UNSIGNED(0, 32)),
      s_axi_arlen => STD_LOGIC_VECTOR(TO_UNSIGNED(0, 8)),
      s_axi_arsize => STD_LOGIC_VECTOR(TO_UNSIGNED(0, 3)),
      s_axi_arburst => STD_LOGIC_VECTOR(TO_UNSIGNED(0, 2)),
      s_axi_arvalid => '0',
      s_axi_rready => '0',
      s_axi_injectsbiterr => '0',
      s_axi_injectdbiterr => '0'
    );
END bd_fc5c_0_lmb_bram_I_0_arch;
