SunnyYoshimitsu/CelestiCall/Hardwares/IPModules/Sound Processor/Sound Processor.gen/sources_1/ip/processing_system7_0/synth/processing_system7_0.v

// (c) Copyright 1986-2022 Xilinx, Inc. All Rights Reserved.
// (c) Copyright 2022-2025 Advanced Micro Devices, Inc. All rights reserved.
// 
// This file contains confidential and proprietary information
// of AMD and is protected under U.S. and international copyright
// and other intellectual property laws.
// 
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
// CRITICAL APPLICATIONS
// AMD products are not designed or intended to be fail-
// safe, or for use in any application requiring fail-safe
// performance, such as life-support or safety devices or
// systems, Class III medical devices, nuclear facilities,
// applications related to the deployment of airbags, or any
// other applications that could lead to death, personal
// injury, or severe property or environmental damage
// (individually and collectively, "Critical
// Applications"). Customer assumes the sole risk and
// liability of any use of AMD products in Critical
// Applications, subject only to applicable laws and
// regulations governing limitations on product liability.
// 
// THIS COPYRIGHT NOTICE AND DISCLAIMER MUST BE RETAINED AS
// PART OF THIS FILE AT ALL TIMES.
// 
// DO NOT MODIFY THIS FILE.


// IP VLNV: xilinx.com:ip:processing_system7:5.5
// IP Revision: 6

(* X_CORE_INFO = "processing_system7_v5_5_processing_system7,Vivado 2023.2" *)
(* CHECK_LICENSE_TYPE = "processing_system7_0,processing_system7_v5_5_processing_system7,{}" *)
(* CORE_GENERATION_INFO = "processing_system7_0,processing_system7_v5_5_processing_system7,{x_ipProduct=Vivado 2023.2,x_ipVendor=xilinx.com,x_ipLibrary=ip,x_ipName=processing_system7,x_ipVersion=5.5,x_ipCoreRevision=6,x_ipLanguage=VERILOG,x_ipSimLanguage=MIXED,C_EN_EMIO_PJTAG=0,C_EN_EMIO_ENET0=0,C_EN_EMIO_ENET1=0,C_EN_EMIO_TRACE=0,C_INCLUDE_TRACE_BUFFER=0,C_TRACE_BUFFER_FIFO_SIZE=128,USE_TRACE_DATA_EDGE_DETECTOR=0,C_TRACE_PIPELINE_WIDTH=8,C_TRACE_BUFFER_CLOCK_DELAY=12,C_EMIO_GPIO_WIDTH=64,C_INCLUDE_ACP_TRANS_CHECK=0,C_USE\
_DEFAULT_ACP_USER_VAL=0,C_S_AXI_ACP_ARUSER_VAL=31,C_S_AXI_ACP_AWUSER_VAL=31,C_M_AXI_GP0_ID_WIDTH=12,C_M_AXI_GP0_ENABLE_STATIC_REMAP=0,C_M_AXI_GP1_ID_WIDTH=12,C_M_AXI_GP1_ENABLE_STATIC_REMAP=0,C_S_AXI_GP0_ID_WIDTH=6,C_S_AXI_GP1_ID_WIDTH=6,C_S_AXI_ACP_ID_WIDTH=3,C_S_AXI_HP0_ID_WIDTH=6,C_S_AXI_HP0_DATA_WIDTH=64,C_S_AXI_HP1_ID_WIDTH=6,C_S_AXI_HP1_DATA_WIDTH=64,C_S_AXI_HP2_ID_WIDTH=6,C_S_AXI_HP2_DATA_WIDTH=64,C_S_AXI_HP3_ID_WIDTH=6,C_S_AXI_HP3_DATA_WIDTH=64,C_M_AXI_GP0_THREAD_ID_WIDTH=12,C_M_AXI_GP1_\
THREAD_ID_WIDTH=12,C_NUM_F2P_INTR_INPUTS=1,C_IRQ_F2P_MODE=DIRECT,C_DQ_WIDTH=16,C_DQS_WIDTH=2,C_DM_WIDTH=2,C_MIO_PRIMITIVE=32,C_TRACE_INTERNAL_WIDTH=2,C_USE_AXI_NONSECURE=0,C_USE_M_AXI_GP0=1,C_USE_M_AXI_GP1=0,C_USE_S_AXI_GP0=1,C_USE_S_AXI_GP1=1,C_USE_S_AXI_HP0=0,C_USE_S_AXI_HP1=0,C_USE_S_AXI_HP2=0,C_USE_S_AXI_HP3=0,C_USE_S_AXI_ACP=0,C_PS7_SI_REV=PRODUCTION,C_FCLK_CLK0_BUF=TRUE,C_FCLK_CLK1_BUF=FALSE,C_FCLK_CLK2_BUF=FALSE,C_FCLK_CLK3_BUF=FALSE,C_PACKAGE_NAME=clg225,C_GP0_EN_MODIFIABLE_TXN=1,C_GP1_E\
N_MODIFIABLE_TXN=1}" *)
(* DowngradeIPIdentifiedWarnings = "yes" *)
module processing_system7_0 (
  M_AXI_GP0_ARVALID,
  M_AXI_GP0_AWVALID,
  M_AXI_GP0_BREADY,
  M_AXI_GP0_RREADY,
  M_AXI_GP0_WLAST,
  M_AXI_GP0_WVALID,
  M_AXI_GP0_ARID,
  M_AXI_GP0_AWID,
  M_AXI_GP0_WID,
  M_AXI_GP0_ARBURST,
  M_AXI_GP0_ARLOCK,
  M_AXI_GP0_ARSIZE,
  M_AXI_GP0_AWBURST,
  M_AXI_GP0_AWLOCK,
  M_AXI_GP0_AWSIZE,
  M_AXI_GP0_ARPROT,
  M_AXI_GP0_AWPROT,
  M_AXI_GP0_ARADDR,
  M_AXI_GP0_AWADDR,
  M_AXI_GP0_WDATA,
  M_AXI_GP0_ARCACHE,
  M_AXI_GP0_ARLEN,
  M_AXI_GP0_ARQOS,
  M_AXI_GP0_AWCACHE,
  M_AXI_GP0_AWLEN,
  M_AXI_GP0_AWQOS,
  M_AXI_GP0_WSTRB,
  M_AXI_GP0_ACLK,
  M_AXI_GP0_ARREADY,
  M_AXI_GP0_AWREADY,
  M_AXI_GP0_BVALID,
  M_AXI_GP0_RLAST,
  M_AXI_GP0_RVALID,
  M_AXI_GP0_WREADY,
  M_AXI_GP0_BID,
  M_AXI_GP0_RID,
  M_AXI_GP0_BRESP,
  M_AXI_GP0_RRESP,
  M_AXI_GP0_RDATA,
  S_AXI_GP0_ARREADY,
  S_AXI_GP0_AWREADY,
  S_AXI_GP0_BVALID,
  S_AXI_GP0_RLAST,
  S_AXI_GP0_RVALID,
  S_AXI_GP0_WREADY,
  S_AXI_GP0_BRESP,
  S_AXI_GP0_RRESP,
  S_AXI_GP0_RDATA,
  S_AXI_GP0_BID,
  S_AXI_GP0_RID,
  S_AXI_GP0_ACLK,
  S_AXI_GP0_ARVALID,
  S_AXI_GP0_AWVALID,
  S_AXI_GP0_BREADY,
  S_AXI_GP0_RREADY,
  S_AXI_GP0_WLAST,
  S_AXI_GP0_WVALID,
  S_AXI_GP0_ARBURST,
  S_AXI_GP0_ARLOCK,
  S_AXI_GP0_ARSIZE,
  S_AXI_GP0_AWBURST,
  S_AXI_GP0_AWLOCK,
  S_AXI_GP0_AWSIZE,
  S_AXI_GP0_ARPROT,
  S_AXI_GP0_AWPROT,
  S_AXI_GP0_ARADDR,
  S_AXI_GP0_AWADDR,
  S_AXI_GP0_WDATA,
  S_AXI_GP0_ARCACHE,
  S_AXI_GP0_ARLEN,
  S_AXI_GP0_ARQOS,
  S_AXI_GP0_AWCACHE,
  S_AXI_GP0_AWLEN,
  S_AXI_GP0_AWQOS,
  S_AXI_GP0_WSTRB,
  S_AXI_GP0_ARID,
  S_AXI_GP0_AWID,
  S_AXI_GP0_WID,
  S_AXI_GP1_ARREADY,
  S_AXI_GP1_AWREADY,
  S_AXI_GP1_BVALID,
  S_AXI_GP1_RLAST,
  S_AXI_GP1_RVALID,
  S_AXI_GP1_WREADY,
  S_AXI_GP1_BRESP,
  S_AXI_GP1_RRESP,
  S_AXI_GP1_RDATA,
  S_AXI_GP1_BID,
  S_AXI_GP1_RID,
  S_AXI_GP1_ACLK,
  S_AXI_GP1_ARVALID,
  S_AXI_GP1_AWVALID,
  S_AXI_GP1_BREADY,
  S_AXI_GP1_RREADY,
  S_AXI_GP1_WLAST,
  S_AXI_GP1_WVALID,
  S_AXI_GP1_ARBURST,
  S_AXI_GP1_ARLOCK,
  S_AXI_GP1_ARSIZE,
  S_AXI_GP1_AWBURST,
  S_AXI_GP1_AWLOCK,
  S_AXI_GP1_AWSIZE,
  S_AXI_GP1_ARPROT,
  S_AXI_GP1_AWPROT,
  S_AXI_GP1_ARADDR,
  S_AXI_GP1_AWADDR,
  S_AXI_GP1_WDATA,
  S_AXI_GP1_ARCACHE,
  S_AXI_GP1_ARLEN,
  S_AXI_GP1_ARQOS,
  S_AXI_GP1_AWCACHE,
  S_AXI_GP1_AWLEN,
  S_AXI_GP1_AWQOS,
  S_AXI_GP1_WSTRB,
  S_AXI_GP1_ARID,
  S_AXI_GP1_AWID,
  S_AXI_GP1_WID,
  FCLK_CLK0,
  FCLK_RESET0_N,
  MIO,
  DDR_CAS_n,
  DDR_CKE,
  DDR_Clk_n,
  DDR_Clk,
  DDR_CS_n,
  DDR_DRSTB,
  DDR_ODT,
  DDR_RAS_n,
  DDR_WEB,
  DDR_BankAddr,
  DDR_Addr,
  DDR_VRN,
  DDR_VRP,
  DDR_DM,
  DDR_DQ,
  DDR_DQS_n,
  DDR_DQS,
  PS_SRSTB,
  PS_CLK,
  PS_PORB
);

(* X_INTERFACE_INFO = "xilinx.com:interface:aximm:1.0 M_AXI_GP0 ARVALID" *)
output wire M_AXI_GP0_ARVALID;
(* X_INTERFACE_INFO = "xilinx.com:interface:aximm:1.0 M_AXI_GP0 AWVALID" *)
output wire M_AXI_GP0_AWVALID;
(* X_INTERFACE_INFO = "xilinx.com:interface:aximm:1.0 M_AXI_GP0 BREADY" *)
output wire M_AXI_GP0_BREADY;
(* X_INTERFACE_INFO = "xilinx.com:interface:aximm:1.0 M_AXI_GP0 RREADY" *)
output wire M_AXI_GP0_RREADY;
(* X_INTERFACE_INFO = "xilinx.com:interface:aximm:1.0 M_AXI_GP0 WLAST" *)
output wire M_AXI_GP0_WLAST;
(* X_INTERFACE_INFO = "xilinx.com:interface:aximm:1.0 M_AXI_GP0 WVALID" *)
output wire M_AXI_GP0_WVALID;
(* X_INTERFACE_INFO = "xilinx.com:interface:aximm:1.0 M_AXI_GP0 ARID" *)
output wire [11 : 0] M_AXI_GP0_ARID;
(* X_INTERFACE_INFO = "xilinx.com:interface:aximm:1.0 M_AXI_GP0 AWID" *)
output wire [11 : 0] M_AXI_GP0_AWID;
(* X_INTERFACE_INFO = "xilinx.com:interface:aximm:1.0 M_AXI_GP0 WID" *)
output wire [11 : 0] M_AXI_GP0_WID;
(* X_INTERFACE_INFO = "xilinx.com:interface:aximm:1.0 M_AXI_GP0 ARBURST" *)
output wire [1 : 0] M_AXI_GP0_ARBURST;
(* X_INTERFACE_INFO = "xilinx.com:interface:aximm:1.0 M_AXI_GP0 ARLOCK" *)
output wire [1 : 0] M_AXI_GP0_ARLOCK;
(* X_INTERFACE_INFO = "xilinx.com:interface:aximm:1.0 M_AXI_GP0 ARSIZE" *)
output wire [2 : 0] M_AXI_GP0_ARSIZE;
(* X_INTERFACE_INFO = "xilinx.com:interface:aximm:1.0 M_AXI_GP0 AWBURST" *)
output wire [1 : 0] M_AXI_GP0_AWBURST;
(* X_INTERFACE_INFO = "xilinx.com:interface:aximm:1.0 M_AXI_GP0 AWLOCK" *)
output wire [1 : 0] M_AXI_GP0_AWLOCK;
(* X_INTERFACE_INFO = "xilinx.com:interface:aximm:1.0 M_AXI_GP0 AWSIZE" *)
output wire [2 : 0] M_AXI_GP0_AWSIZE;
(* X_INTERFACE_INFO = "xilinx.com:interface:aximm:1.0 M_AXI_GP0 ARPROT" *)
output wire [2 : 0] M_AXI_GP0_ARPROT;
(* X_INTERFACE_INFO = "xilinx.com:interface:aximm:1.0 M_AXI_GP0 AWPROT" *)
output wire [2 : 0] M_AXI_GP0_AWPROT;
(* X_INTERFACE_INFO = "xilinx.com:interface:aximm:1.0 M_AXI_GP0 ARADDR" *)
output wire [31 : 0] M_AXI_GP0_ARADDR;
(* X_INTERFACE_INFO = "xilinx.com:interface:aximm:1.0 M_AXI_GP0 AWADDR" *)
output wire [31 : 0] M_AXI_GP0_AWADDR;
(* X_INTERFACE_INFO = "xilinx.com:interface:aximm:1.0 M_AXI_GP0 WDATA" *)
output wire [31 : 0] M_AXI_GP0_WDATA;
(* X_INTERFACE_INFO = "xilinx.com:interface:aximm:1.0 M_AXI_GP0 ARCACHE" *)
output wire [3 : 0] M_AXI_GP0_ARCACHE;
(* X_INTERFACE_INFO = "xilinx.com:interface:aximm:1.0 M_AXI_GP0 ARLEN" *)
output wire [3 : 0] M_AXI_GP0_ARLEN;
(* X_INTERFACE_INFO = "xilinx.com:interface:aximm:1.0 M_AXI_GP0 ARQOS" *)
output wire [3 : 0] M_AXI_GP0_ARQOS;
(* X_INTERFACE_INFO = "xilinx.com:interface:aximm:1.0 M_AXI_GP0 AWCACHE" *)
output wire [3 : 0] M_AXI_GP0_AWCACHE;
(* X_INTERFACE_INFO = "xilinx.com:interface:aximm:1.0 M_AXI_GP0 AWLEN" *)
output wire [3 : 0] M_AXI_GP0_AWLEN;
(* X_INTERFACE_INFO = "xilinx.com:interface:aximm:1.0 M_AXI_GP0 AWQOS" *)
output wire [3 : 0] M_AXI_GP0_AWQOS;
(* X_INTERFACE_INFO = "xilinx.com:interface:aximm:1.0 M_AXI_GP0 WSTRB" *)
output wire [3 : 0] M_AXI_GP0_WSTRB;
(* X_INTERFACE_PARAMETER = "XIL_INTERFACENAME M_AXI_GP0_ACLK, ASSOCIATED_BUSIF M_AXI_GP0, FREQ_HZ 100000000, FREQ_TOLERANCE_HZ 0, PHASE 0.0, INSERT_VIP 0" *)
(* X_INTERFACE_INFO = "xilinx.com:signal:clock:1.0 M_AXI_GP0_ACLK CLK" *)
input wire M_AXI_GP0_ACLK;
(* X_INTERFACE_INFO = "xilinx.com:interface:aximm:1.0 M_AXI_GP0 ARREADY" *)
input wire M_AXI_GP0_ARREADY;
(* X_INTERFACE_INFO = "xilinx.com:interface:aximm:1.0 M_AXI_GP0 AWREADY" *)
input wire M_AXI_GP0_AWREADY;
(* X_INTERFACE_INFO = "xilinx.com:interface:aximm:1.0 M_AXI_GP0 BVALID" *)
input wire M_AXI_GP0_BVALID;
(* X_INTERFACE_INFO = "xilinx.com:interface:aximm:1.0 M_AXI_GP0 RLAST" *)
input wire M_AXI_GP0_RLAST;
(* X_INTERFACE_INFO = "xilinx.com:interface:aximm:1.0 M_AXI_GP0 RVALID" *)
input wire M_AXI_GP0_RVALID;
(* X_INTERFACE_INFO = "xilinx.com:interface:aximm:1.0 M_AXI_GP0 WREADY" *)
input wire M_AXI_GP0_WREADY;
(* X_INTERFACE_INFO = "xilinx.com:interface:aximm:1.0 M_AXI_GP0 BID" *)
input wire [11 : 0] M_AXI_GP0_BID;
(* X_INTERFACE_INFO = "xilinx.com:interface:aximm:1.0 M_AXI_GP0 RID" *)
input wire [11 : 0] M_AXI_GP0_RID;
(* X_INTERFACE_INFO = "xilinx.com:interface:aximm:1.0 M_AXI_GP0 BRESP" *)
input wire [1 : 0] M_AXI_GP0_BRESP;
(* X_INTERFACE_INFO = "xilinx.com:interface:aximm:1.0 M_AXI_GP0 RRESP" *)
input wire [1 : 0] M_AXI_GP0_RRESP;
(* X_INTERFACE_PARAMETER = "XIL_INTERFACENAME M_AXI_GP0, SUPPORTS_NARROW_BURST 1, NUM_WRITE_OUTSTANDING 8, NUM_READ_OUTSTANDING 8, DATA_WIDTH 32, PROTOCOL AXI3, FREQ_HZ 100000000, ID_WIDTH 12, ADDR_WIDTH 32, AWUSER_WIDTH 0, ARUSER_WIDTH 0, WUSER_WIDTH 0, RUSER_WIDTH 0, BUSER_WIDTH 0, READ_WRITE_MODE READ_WRITE, HAS_BURST 1, HAS_LOCK 1, HAS_PROT 1, HAS_CACHE 1, HAS_QOS 1, HAS_REGION 0, HAS_WSTRB 1, HAS_BRESP 1, HAS_RRESP 1, MAX_BURST_LENGTH 16, PHASE 0.0, NUM_READ_THREADS 1, NUM_WRITE_THREADS 1, RUSER_BITS_PER_BYTE 0, WUSER\
_BITS_PER_BYTE 0, INSERT_VIP 0" *)
(* X_INTERFACE_INFO = "xilinx.com:interface:aximm:1.0 M_AXI_GP0 RDATA" *)
input wire [31 : 0] M_AXI_GP0_RDATA;
(* X_INTERFACE_INFO = "xilinx.com:interface:aximm:1.0 S_AXI_GP0 ARREADY" *)
output wire S_AXI_GP0_ARREADY;
(* X_INTERFACE_INFO = "xilinx.com:interface:aximm:1.0 S_AXI_GP0 AWREADY" *)
output wire S_AXI_GP0_AWREADY;
(* X_INTERFACE_INFO = "xilinx.com:interface:aximm:1.0 S_AXI_GP0 BVALID" *)
output wire S_AXI_GP0_BVALID;
(* X_INTERFACE_INFO = "xilinx.com:interface:aximm:1.0 S_AXI_GP0 RLAST" *)
output wire S_AXI_GP0_RLAST;
(* X_INTERFACE_INFO = "xilinx.com:interface:aximm:1.0 S_AXI_GP0 RVALID" *)
output wire S_AXI_GP0_RVALID;
(* X_INTERFACE_INFO = "xilinx.com:interface:aximm:1.0 S_AXI_GP0 WREADY" *)
output wire S_AXI_GP0_WREADY;
(* X_INTERFACE_INFO = "xilinx.com:interface:aximm:1.0 S_AXI_GP0 BRESP" *)
output wire [1 : 0] S_AXI_GP0_BRESP;
(* X_INTERFACE_INFO = "xilinx.com:interface:aximm:1.0 S_AXI_GP0 RRESP" *)
output wire [1 : 0] S_AXI_GP0_RRESP;
(* X_INTERFACE_INFO = "xilinx.com:interface:aximm:1.0 S_AXI_GP0 RDATA" *)
output wire [31 : 0] S_AXI_GP0_RDATA;
(* X_INTERFACE_INFO = "xilinx.com:interface:aximm:1.0 S_AXI_GP0 BID" *)
output wire [5 : 0] S_AXI_GP0_BID;
(* X_INTERFACE_INFO = "xilinx.com:interface:aximm:1.0 S_AXI_GP0 RID" *)
output wire [5 : 0] S_AXI_GP0_RID;
(* X_INTERFACE_PARAMETER = "XIL_INTERFACENAME S_AXI_GP0_ACLK, ASSOCIATED_BUSIF S_AXI_GP0, FREQ_HZ 100000000, FREQ_TOLERANCE_HZ 0, PHASE 0.0, INSERT_VIP 0" *)
(* X_INTERFACE_INFO = "xilinx.com:signal:clock:1.0 S_AXI_GP0_ACLK CLK" *)
input wire S_AXI_GP0_ACLK;
(* X_INTERFACE_INFO = "xilinx.com:interface:aximm:1.0 S_AXI_GP0 ARVALID" *)
input wire S_AXI_GP0_ARVALID;
(* X_INTERFACE_INFO = "xilinx.com:interface:aximm:1.0 S_AXI_GP0 AWVALID" *)
input wire S_AXI_GP0_AWVALID;
(* X_INTERFACE_INFO = "xilinx.com:interface:aximm:1.0 S_AXI_GP0 BREADY" *)
input wire S_AXI_GP0_BREADY;
(* X_INTERFACE_INFO = "xilinx.com:interface:aximm:1.0 S_AXI_GP0 RREADY" *)
input wire S_AXI_GP0_RREADY;
(* X_INTERFACE_INFO = "xilinx.com:interface:aximm:1.0 S_AXI_GP0 WLAST" *)
input wire S_AXI_GP0_WLAST;
(* X_INTERFACE_INFO = "xilinx.com:interface:aximm:1.0 S_AXI_GP0 WVALID" *)
input wire S_AXI_GP0_WVALID;
(* X_INTERFACE_INFO = "xilinx.com:interface:aximm:1.0 S_AXI_GP0 ARBURST" *)
input wire [1 : 0] S_AXI_GP0_ARBURST;
(* X_INTERFACE_INFO = "xilinx.com:interface:aximm:1.0 S_AXI_GP0 ARLOCK" *)
input wire [1 : 0] S_AXI_GP0_ARLOCK;
(* X_INTERFACE_INFO = "xilinx.com:interface:aximm:1.0 S_AXI_GP0 ARSIZE" *)
input wire [2 : 0] S_AXI_GP0_ARSIZE;
(* X_INTERFACE_INFO = "xilinx.com:interface:aximm:1.0 S_AXI_GP0 AWBURST" *)
input wire [1 : 0] S_AXI_GP0_AWBURST;
(* X_INTERFACE_INFO = "xilinx.com:interface:aximm:1.0 S_AXI_GP0 AWLOCK" *)
input wire [1 : 0] S_AXI_GP0_AWLOCK;
(* X_INTERFACE_INFO = "xilinx.com:interface:aximm:1.0 S_AXI_GP0 AWSIZE" *)
input wire [2 : 0] S_AXI_GP0_AWSIZE;
(* X_INTERFACE_INFO = "xilinx.com:interface:aximm:1.0 S_AXI_GP0 ARPROT" *)
input wire [2 : 0] S_AXI_GP0_ARPROT;
(* X_INTERFACE_INFO = "xilinx.com:interface:aximm:1.0 S_AXI_GP0 AWPROT" *)
input wire [2 : 0] S_AXI_GP0_AWPROT;
(* X_INTERFACE_INFO = "xilinx.com:interface:aximm:1.0 S_AXI_GP0 ARADDR" *)
input wire [31 : 0] S_AXI_GP0_ARADDR;
(* X_INTERFACE_INFO = "xilinx.com:interface:aximm:1.0 S_AXI_GP0 AWADDR" *)
input wire [31 : 0] S_AXI_GP0_AWADDR;
(* X_INTERFACE_INFO = "xilinx.com:interface:aximm:1.0 S_AXI_GP0 WDATA" *)
input wire [31 : 0] S_AXI_GP0_WDATA;
(* X_INTERFACE_INFO = "xilinx.com:interface:aximm:1.0 S_AXI_GP0 ARCACHE" *)
input wire [3 : 0] S_AXI_GP0_ARCACHE;
(* X_INTERFACE_INFO = "xilinx.com:interface:aximm:1.0 S_AXI_GP0 ARLEN" *)
input wire [3 : 0] S_AXI_GP0_ARLEN;
(* X_INTERFACE_INFO = "xilinx.com:interface:aximm:1.0 S_AXI_GP0 ARQOS" *)
input wire [3 : 0] S_AXI_GP0_ARQOS;
(* X_INTERFACE_INFO = "xilinx.com:interface:aximm:1.0 S_AXI_GP0 AWCACHE" *)
input wire [3 : 0] S_AXI_GP0_AWCACHE;
(* X_INTERFACE_INFO = "xilinx.com:interface:aximm:1.0 S_AXI_GP0 AWLEN" *)
input wire [3 : 0] S_AXI_GP0_AWLEN;
(* X_INTERFACE_INFO = "xilinx.com:interface:aximm:1.0 S_AXI_GP0 AWQOS" *)
input wire [3 : 0] S_AXI_GP0_AWQOS;
(* X_INTERFACE_INFO = "xilinx.com:interface:aximm:1.0 S_AXI_GP0 WSTRB" *)
input wire [3 : 0] S_AXI_GP0_WSTRB;
(* X_INTERFACE_INFO = "xilinx.com:interface:aximm:1.0 S_AXI_GP0 ARID" *)
input wire [5 : 0] S_AXI_GP0_ARID;
(* X_INTERFACE_INFO = "xilinx.com:interface:aximm:1.0 S_AXI_GP0 AWID" *)
input wire [5 : 0] S_AXI_GP0_AWID;
(* X_INTERFACE_PARAMETER = "XIL_INTERFACENAME S_AXI_GP0, NUM_WRITE_OUTSTANDING 8, NUM_READ_OUTSTANDING 8, DATA_WIDTH 32, PROTOCOL AXI3, FREQ_HZ 100000000, ID_WIDTH 6, ADDR_WIDTH 32, AWUSER_WIDTH 0, ARUSER_WIDTH 0, WUSER_WIDTH 0, RUSER_WIDTH 0, BUSER_WIDTH 0, READ_WRITE_MODE READ_WRITE, HAS_BURST 1, HAS_LOCK 1, HAS_PROT 1, HAS_CACHE 1, HAS_QOS 1, HAS_REGION 0, HAS_WSTRB 1, HAS_BRESP 1, HAS_RRESP 1, SUPPORTS_NARROW_BURST 1, MAX_BURST_LENGTH 16, PHASE 0.0, NUM_READ_THREADS 1, NUM_WRITE_THREADS 1, RUSER_BITS_PER_BYTE 0, WUSER_\
BITS_PER_BYTE 0, INSERT_VIP 0" *)
(* X_INTERFACE_INFO = "xilinx.com:interface:aximm:1.0 S_AXI_GP0 WID" *)
input wire [5 : 0] S_AXI_GP0_WID;
(* X_INTERFACE_INFO = "xilinx.com:interface:aximm:1.0 S_AXI_GP1 ARREADY" *)
output wire S_AXI_GP1_ARREADY;
(* X_INTERFACE_INFO = "xilinx.com:interface:aximm:1.0 S_AXI_GP1 AWREADY" *)
output wire S_AXI_GP1_AWREADY;
(* X_INTERFACE_INFO = "xilinx.com:interface:aximm:1.0 S_AXI_GP1 BVALID" *)
output wire S_AXI_GP1_BVALID;
(* X_INTERFACE_INFO = "xilinx.com:interface:aximm:1.0 S_AXI_GP1 RLAST" *)
output wire S_AXI_GP1_RLAST;
(* X_INTERFACE_INFO = "xilinx.com:interface:aximm:1.0 S_AXI_GP1 RVALID" *)
output wire S_AXI_GP1_RVALID;
(* X_INTERFACE_INFO = "xilinx.com:interface:aximm:1.0 S_AXI_GP1 WREADY" *)
output wire S_AXI_GP1_WREADY;
(* X_INTERFACE_INFO = "xilinx.com:interface:aximm:1.0 S_AXI_GP1 BRESP" *)
output wire [1 : 0] S_AXI_GP1_BRESP;
(* X_INTERFACE_INFO = "xilinx.com:interface:aximm:1.0 S_AXI_GP1 RRESP" *)
output wire [1 : 0] S_AXI_GP1_RRESP;
(* X_INTERFACE_INFO = "xilinx.com:interface:aximm:1.0 S_AXI_GP1 RDATA" *)
output wire [31 : 0] S_AXI_GP1_RDATA;
(* X_INTERFACE_INFO = "xilinx.com:interface:aximm:1.0 S_AXI_GP1 BID" *)
output wire [5 : 0] S_AXI_GP1_BID;
(* X_INTERFACE_INFO = "xilinx.com:interface:aximm:1.0 S_AXI_GP1 RID" *)
output wire [5 : 0] S_AXI_GP1_RID;
(* X_INTERFACE_PARAMETER = "XIL_INTERFACENAME S_AXI_GP1_ACLK, ASSOCIATED_BUSIF S_AXI_GP1, FREQ_HZ 100000000, FREQ_TOLERANCE_HZ 0, PHASE 0.0, INSERT_VIP 0" *)
(* X_INTERFACE_INFO = "xilinx.com:signal:clock:1.0 S_AXI_GP1_ACLK CLK" *)
input wire S_AXI_GP1_ACLK;
(* X_INTERFACE_INFO = "xilinx.com:interface:aximm:1.0 S_AXI_GP1 ARVALID" *)
input wire S_AXI_GP1_ARVALID;
(* X_INTERFACE_INFO = "xilinx.com:interface:aximm:1.0 S_AXI_GP1 AWVALID" *)
input wire S_AXI_GP1_AWVALID;
(* X_INTERFACE_INFO = "xilinx.com:interface:aximm:1.0 S_AXI_GP1 BREADY" *)
input wire S_AXI_GP1_BREADY;
(* X_INTERFACE_INFO = "xilinx.com:interface:aximm:1.0 S_AXI_GP1 RREADY" *)
input wire S_AXI_GP1_RREADY;
(* X_INTERFACE_INFO = "xilinx.com:interface:aximm:1.0 S_AXI_GP1 WLAST" *)
input wire S_AXI_GP1_WLAST;
(* X_INTERFACE_INFO = "xilinx.com:interface:aximm:1.0 S_AXI_GP1 WVALID" *)
input wire S_AXI_GP1_WVALID;
(* X_INTERFACE_INFO = "xilinx.com:interface:aximm:1.0 S_AXI_GP1 ARBURST" *)
input wire [1 : 0] S_AXI_GP1_ARBURST;
(* X_INTERFACE_INFO = "xilinx.com:interface:aximm:1.0 S_AXI_GP1 ARLOCK" *)
input wire [1 : 0] S_AXI_GP1_ARLOCK;
(* X_INTERFACE_INFO = "xilinx.com:interface:aximm:1.0 S_AXI_GP1 ARSIZE" *)
input wire [2 : 0] S_AXI_GP1_ARSIZE;
(* X_INTERFACE_INFO = "xilinx.com:interface:aximm:1.0 S_AXI_GP1 AWBURST" *)
input wire [1 : 0] S_AXI_GP1_AWBURST;
(* X_INTERFACE_INFO = "xilinx.com:interface:aximm:1.0 S_AXI_GP1 AWLOCK" *)
input wire [1 : 0] S_AXI_GP1_AWLOCK;
(* X_INTERFACE_INFO = "xilinx.com:interface:aximm:1.0 S_AXI_GP1 AWSIZE" *)
input wire [2 : 0] S_AXI_GP1_AWSIZE;
(* X_INTERFACE_INFO = "xilinx.com:interface:aximm:1.0 S_AXI_GP1 ARPROT" *)
input wire [2 : 0] S_AXI_GP1_ARPROT;
(* X_INTERFACE_INFO = "xilinx.com:interface:aximm:1.0 S_AXI_GP1 AWPROT" *)
input wire [2 : 0] S_AXI_GP1_AWPROT;
(* X_INTERFACE_INFO = "xilinx.com:interface:aximm:1.0 S_AXI_GP1 ARADDR" *)
input wire [31 : 0] S_AXI_GP1_ARADDR;
(* X_INTERFACE_INFO = "xilinx.com:interface:aximm:1.0 S_AXI_GP1 AWADDR" *)
input wire [31 : 0] S_AXI_GP1_AWADDR;
(* X_INTERFACE_INFO = "xilinx.com:interface:aximm:1.0 S_AXI_GP1 WDATA" *)
input wire [31 : 0] S_AXI_GP1_WDATA;
(* X_INTERFACE_INFO = "xilinx.com:interface:aximm:1.0 S_AXI_GP1 ARCACHE" *)
input wire [3 : 0] S_AXI_GP1_ARCACHE;
(* X_INTERFACE_INFO = "xilinx.com:interface:aximm:1.0 S_AXI_GP1 ARLEN" *)
input wire [3 : 0] S_AXI_GP1_ARLEN;
(* X_INTERFACE_INFO = "xilinx.com:interface:aximm:1.0 S_AXI_GP1 ARQOS" *)
input wire [3 : 0] S_AXI_GP1_ARQOS;
(* X_INTERFACE_INFO = "xilinx.com:interface:aximm:1.0 S_AXI_GP1 AWCACHE" *)
input wire [3 : 0] S_AXI_GP1_AWCACHE;
(* X_INTERFACE_INFO = "xilinx.com:interface:aximm:1.0 S_AXI_GP1 AWLEN" *)
input wire [3 : 0] S_AXI_GP1_AWLEN;
(* X_INTERFACE_INFO = "xilinx.com:interface:aximm:1.0 S_AXI_GP1 AWQOS" *)
input wire [3 : 0] S_AXI_GP1_AWQOS;
(* X_INTERFACE_INFO = "xilinx.com:interface:aximm:1.0 S_AXI_GP1 WSTRB" *)
input wire [3 : 0] S_AXI_GP1_WSTRB;
(* X_INTERFACE_INFO = "xilinx.com:interface:aximm:1.0 S_AXI_GP1 ARID" *)
input wire [5 : 0] S_AXI_GP1_ARID;
(* X_INTERFACE_INFO = "xilinx.com:interface:aximm:1.0 S_AXI_GP1 AWID" *)
input wire [5 : 0] S_AXI_GP1_AWID;
(* X_INTERFACE_PARAMETER = "XIL_INTERFACENAME S_AXI_GP1, NUM_WRITE_OUTSTANDING 8, NUM_READ_OUTSTANDING 8, DATA_WIDTH 32, PROTOCOL AXI3, FREQ_HZ 100000000, ID_WIDTH 6, ADDR_WIDTH 32, AWUSER_WIDTH 0, ARUSER_WIDTH 0, WUSER_WIDTH 0, RUSER_WIDTH 0, BUSER_WIDTH 0, READ_WRITE_MODE READ_WRITE, HAS_BURST 1, HAS_LOCK 1, HAS_PROT 1, HAS_CACHE 1, HAS_QOS 1, HAS_REGION 0, HAS_WSTRB 1, HAS_BRESP 1, HAS_RRESP 1, SUPPORTS_NARROW_BURST 1, MAX_BURST_LENGTH 16, PHASE 0.0, NUM_READ_THREADS 1, NUM_WRITE_THREADS 1, RUSER_BITS_PER_BYTE 0, WUSER_\
BITS_PER_BYTE 0, INSERT_VIP 0" *)
(* X_INTERFACE_INFO = "xilinx.com:interface:aximm:1.0 S_AXI_GP1 WID" *)
input wire [5 : 0] S_AXI_GP1_WID;
(* X_INTERFACE_PARAMETER = "XIL_INTERFACENAME FCLK_CLK0, FREQ_HZ 5e+07, FREQ_TOLERANCE_HZ 0, PHASE 0.0, INSERT_VIP 0" *)
(* X_INTERFACE_INFO = "xilinx.com:signal:clock:1.0 FCLK_CLK0 CLK" *)
output wire FCLK_CLK0;
(* X_INTERFACE_PARAMETER = "XIL_INTERFACENAME FCLK_RESET0_N, POLARITY ACTIVE_LOW, INSERT_VIP 0" *)
(* X_INTERFACE_INFO = "xilinx.com:signal:reset:1.0 FCLK_RESET0_N RST" *)
output wire FCLK_RESET0_N;
(* X_INTERFACE_INFO = "xilinx.com:display_processing_system7:fixedio:1.0 FIXED_IO MIO" *)
inout wire [31 : 0] MIO;
(* X_INTERFACE_INFO = "xilinx.com:interface:ddrx:1.0 DDR CAS_N" *)
inout wire DDR_CAS_n;
(* X_INTERFACE_INFO = "xilinx.com:interface:ddrx:1.0 DDR CKE" *)
inout wire DDR_CKE;
(* X_INTERFACE_INFO = "xilinx.com:interface:ddrx:1.0 DDR CK_N" *)
inout wire DDR_Clk_n;
(* X_INTERFACE_INFO = "xilinx.com:interface:ddrx:1.0 DDR CK_P" *)
inout wire DDR_Clk;
(* X_INTERFACE_INFO = "xilinx.com:interface:ddrx:1.0 DDR CS_N" *)
inout wire DDR_CS_n;
(* X_INTERFACE_INFO = "xilinx.com:interface:ddrx:1.0 DDR RESET_N" *)
inout wire DDR_DRSTB;
(* X_INTERFACE_INFO = "xilinx.com:interface:ddrx:1.0 DDR ODT" *)
inout wire DDR_ODT;
(* X_INTERFACE_INFO = "xilinx.com:interface:ddrx:1.0 DDR RAS_N" *)
inout wire DDR_RAS_n;
(* X_INTERFACE_INFO = "xilinx.com:interface:ddrx:1.0 DDR WE_N" *)
inout wire DDR_WEB;
(* X_INTERFACE_INFO = "xilinx.com:interface:ddrx:1.0 DDR BA" *)
inout wire [2 : 0] DDR_BankAddr;
(* X_INTERFACE_INFO = "xilinx.com:interface:ddrx:1.0 DDR ADDR" *)
inout wire [14 : 0] DDR_Addr;
(* X_INTERFACE_INFO = "xilinx.com:display_processing_system7:fixedio:1.0 FIXED_IO DDR_VRN" *)
inout wire DDR_VRN;
(* X_INTERFACE_INFO = "xilinx.com:display_processing_system7:fixedio:1.0 FIXED_IO DDR_VRP" *)
inout wire DDR_VRP;
(* X_INTERFACE_INFO = "xilinx.com:interface:ddrx:1.0 DDR DM" *)
inout wire [1 : 0] DDR_DM;
(* X_INTERFACE_INFO = "xilinx.com:interface:ddrx:1.0 DDR DQ" *)
inout wire [15 : 0] DDR_DQ;
(* X_INTERFACE_INFO = "xilinx.com:interface:ddrx:1.0 DDR DQS_N" *)
inout wire [1 : 0] DDR_DQS_n;
(* X_INTERFACE_PARAMETER = "XIL_INTERFACENAME DDR, CAN_DEBUG false, TIMEPERIOD_PS 1250, MEMORY_TYPE COMPONENTS, DATA_WIDTH 8, CS_ENABLED true, DATA_MASK_ENABLED true, SLOT Single, MEM_ADDR_MAP ROW_COLUMN_BANK, BURST_LENGTH 8, AXI_ARBITRATION_SCHEME TDM, CAS_LATENCY 11, CAS_WRITE_LATENCY 11" *)
(* X_INTERFACE_INFO = "xilinx.com:interface:ddrx:1.0 DDR DQS_P" *)
inout wire [1 : 0] DDR_DQS;
(* X_INTERFACE_INFO = "xilinx.com:display_processing_system7:fixedio:1.0 FIXED_IO PS_SRSTB" *)
inout wire PS_SRSTB;
(* X_INTERFACE_INFO = "xilinx.com:display_processing_system7:fixedio:1.0 FIXED_IO PS_CLK" *)
inout wire PS_CLK;
(* X_INTERFACE_PARAMETER = "XIL_INTERFACENAME FIXED_IO, CAN_DEBUG false" *)
(* X_INTERFACE_INFO = "xilinx.com:display_processing_system7:fixedio:1.0 FIXED_IO PS_PORB" *)
inout wire PS_PORB;

  processing_system7_v5_5_processing_system7 #(
    .C_EN_EMIO_PJTAG(0),
    .C_EN_EMIO_ENET0(0),
    .C_EN_EMIO_ENET1(0),
    .C_EN_EMIO_TRACE(0),
    .C_INCLUDE_TRACE_BUFFER(0),
    .C_TRACE_BUFFER_FIFO_SIZE(128),
    .USE_TRACE_DATA_EDGE_DETECTOR(0),
    .C_TRACE_PIPELINE_WIDTH(8),
    .C_TRACE_BUFFER_CLOCK_DELAY(12),
    .C_EMIO_GPIO_WIDTH(64),
    .C_INCLUDE_ACP_TRANS_CHECK(0),
    .C_USE_DEFAULT_ACP_USER_VAL(0),
    .C_S_AXI_ACP_ARUSER_VAL(31),
    .C_S_AXI_ACP_AWUSER_VAL(31),
    .C_M_AXI_GP0_ID_WIDTH(12),
    .C_M_AXI_GP0_ENABLE_STATIC_REMAP(0),
    .C_M_AXI_GP1_ID_WIDTH(12),
    .C_M_AXI_GP1_ENABLE_STATIC_REMAP(0),
    .C_S_AXI_GP0_ID_WIDTH(6),
    .C_S_AXI_GP1_ID_WIDTH(6),
    .C_S_AXI_ACP_ID_WIDTH(3),
    .C_S_AXI_HP0_ID_WIDTH(6),
    .C_S_AXI_HP0_DATA_WIDTH(64),
    .C_S_AXI_HP1_ID_WIDTH(6),
    .C_S_AXI_HP1_DATA_WIDTH(64),
    .C_S_AXI_HP2_ID_WIDTH(6),
    .C_S_AXI_HP2_DATA_WIDTH(64),
    .C_S_AXI_HP3_ID_WIDTH(6),
    .C_S_AXI_HP3_DATA_WIDTH(64),
    .C_M_AXI_GP0_THREAD_ID_WIDTH(12),
    .C_M_AXI_GP1_THREAD_ID_WIDTH(12),
    .C_NUM_F2P_INTR_INPUTS(1),
    .C_IRQ_F2P_MODE("DIRECT"),
    .C_DQ_WIDTH(16),
    .C_DQS_WIDTH(2),
    .C_DM_WIDTH(2),
    .C_MIO_PRIMITIVE(32),
    .C_TRACE_INTERNAL_WIDTH(2),
    .C_USE_AXI_NONSECURE(0),
    .C_USE_M_AXI_GP0(1),
    .C_USE_M_AXI_GP1(0),
    .C_USE_S_AXI_GP0(1),
    .C_USE_S_AXI_GP1(1),
    .C_USE_S_AXI_HP0(0),
    .C_USE_S_AXI_HP1(0),
    .C_USE_S_AXI_HP2(0),
    .C_USE_S_AXI_HP3(0),
    .C_USE_S_AXI_ACP(0),
    .C_PS7_SI_REV("PRODUCTION"),
    .C_FCLK_CLK0_BUF("TRUE"),
    .C_FCLK_CLK1_BUF("FALSE"),
    .C_FCLK_CLK2_BUF("FALSE"),
    .C_FCLK_CLK3_BUF("FALSE"),
    .C_PACKAGE_NAME("clg225"),
    .C_GP0_EN_MODIFIABLE_TXN(1),
    .C_GP1_EN_MODIFIABLE_TXN(1)
  ) inst (
    .CAN0_PHY_TX(),
    .CAN0_PHY_RX(1'B0),
    .CAN1_PHY_TX(),
    .CAN1_PHY_RX(1'B0),
    .ENET0_GMII_TX_EN(),
    .ENET0_GMII_TX_ER(),
    .ENET0_MDIO_MDC(),
    .ENET0_MDIO_O(),
    .ENET0_MDIO_T(),
    .ENET0_PTP_DELAY_REQ_RX(),
    .ENET0_PTP_DELAY_REQ_TX(),
    .ENET0_PTP_PDELAY_REQ_RX(),
    .ENET0_PTP_PDELAY_REQ_TX(),
    .ENET0_PTP_PDELAY_RESP_RX(),
    .ENET0_PTP_PDELAY_RESP_TX(),
    .ENET0_PTP_SYNC_FRAME_RX(),
    .ENET0_PTP_SYNC_FRAME_TX(),
    .ENET0_SOF_RX(),
    .ENET0_SOF_TX(),
    .ENET0_GMII_TXD(),
    .ENET0_GMII_COL(1'B0),
    .ENET0_GMII_CRS(1'B0),
    .ENET0_GMII_RX_CLK(1'B0),
    .ENET0_GMII_RX_DV(1'B0),
    .ENET0_GMII_RX_ER(1'B0),
    .ENET0_GMII_TX_CLK(1'B0),
    .ENET0_MDIO_I(1'B0),
    .ENET0_EXT_INTIN(1'B0),
    .ENET0_GMII_RXD(8'B0),
    .ENET1_GMII_TX_EN(),
    .ENET1_GMII_TX_ER(),
    .ENET1_MDIO_MDC(),
    .ENET1_MDIO_O(),
    .ENET1_MDIO_T(),
    .ENET1_PTP_DELAY_REQ_RX(),
    .ENET1_PTP_DELAY_REQ_TX(),
    .ENET1_PTP_PDELAY_REQ_RX(),
    .ENET1_PTP_PDELAY_REQ_TX(),
    .ENET1_PTP_PDELAY_RESP_RX(),
    .ENET1_PTP_PDELAY_RESP_TX(),
    .ENET1_PTP_SYNC_FRAME_RX(),
    .ENET1_PTP_SYNC_FRAME_TX(),
    .ENET1_SOF_RX(),
    .ENET1_SOF_TX(),
    .ENET1_GMII_TXD(),
    .ENET1_GMII_COL(1'B0),
    .ENET1_GMII_CRS(1'B0),
    .ENET1_GMII_RX_CLK(1'B0),
    .ENET1_GMII_RX_DV(1'B0),
    .ENET1_GMII_RX_ER(1'B0),
    .ENET1_GMII_TX_CLK(1'B0),
    .ENET1_MDIO_I(1'B0),
    .ENET1_EXT_INTIN(1'B0),
    .ENET1_GMII_RXD(8'B0),
    .GPIO_I(64'B0),
    .GPIO_O(),
    .GPIO_T(),
    .I2C0_SDA_I(1'B0),
    .I2C0_SDA_O(),
    .I2C0_SDA_T(),
    .I2C0_SCL_I(1'B0),
    .I2C0_SCL_O(),
    .I2C0_SCL_T(),
    .I2C1_SDA_I(1'B0),
    .I2C1_SDA_O(),
    .I2C1_SDA_T(),
    .I2C1_SCL_I(1'B0),
    .I2C1_SCL_O(),
    .I2C1_SCL_T(),
    .PJTAG_TCK(1'B0),
    .PJTAG_TMS(1'B0),
    .PJTAG_TDI(1'B0),
    .PJTAG_TDO(),
    .SDIO0_CLK(),
    .SDIO0_CLK_FB(1'B0),
    .SDIO0_CMD_O(),
    .SDIO0_CMD_I(1'B0),
    .SDIO0_CMD_T(),
    .SDIO0_DATA_I(4'B0),
    .SDIO0_DATA_O(),
    .SDIO0_DATA_T(),
    .SDIO0_LED(),
    .SDIO0_CDN(1'B0),
    .SDIO0_WP(1'B0),
    .SDIO0_BUSPOW(),
    .SDIO0_BUSVOLT(),
    .SDIO1_CLK(),
    .SDIO1_CLK_FB(1'B0),
    .SDIO1_CMD_O(),
    .SDIO1_CMD_I(1'B0),
    .SDIO1_CMD_T(),
    .SDIO1_DATA_I(4'B0),
    .SDIO1_DATA_O(),
    .SDIO1_DATA_T(),
    .SDIO1_LED(),
    .SDIO1_CDN(1'B0),
    .SDIO1_WP(1'B0),
    .SDIO1_BUSPOW(),
    .SDIO1_BUSVOLT(),
    .SPI0_SCLK_I(1'B0),
    .SPI0_SCLK_O(),
    .SPI0_SCLK_T(),
    .SPI0_MOSI_I(1'B0),
    .SPI0_MOSI_O(),
    .SPI0_MOSI_T(),
    .SPI0_MISO_I(1'B0),
    .SPI0_MISO_O(),
    .SPI0_MISO_T(),
    .SPI0_SS_I(1'B0),
    .SPI0_SS_O(),
    .SPI0_SS1_O(),
    .SPI0_SS2_O(),
    .SPI0_SS_T(),
    .SPI1_SCLK_I(1'B0),
    .SPI1_SCLK_O(),
    .SPI1_SCLK_T(),
    .SPI1_MOSI_I(1'B0),
    .SPI1_MOSI_O(),
    .SPI1_MOSI_T(),
    .SPI1_MISO_I(1'B0),
    .SPI1_MISO_O(),
    .SPI1_MISO_T(),
    .SPI1_SS_I(1'B0),
    .SPI1_SS_O(),
    .SPI1_SS1_O(),
    .SPI1_SS2_O(),
    .SPI1_SS_T(),
    .UART0_DTRN(),
    .UART0_RTSN(),
    .UART0_TX(),
    .UART0_CTSN(1'B0),
    .UART0_DCDN(1'B0),
    .UART0_DSRN(1'B0),
    .UART0_RIN(1'B0),
    .UART0_RX(1'B1),
    .UART1_DTRN(),
    .UART1_RTSN(),
    .UART1_TX(),
    .UART1_CTSN(1'B0),
    .UART1_DCDN(1'B0),
    .UART1_DSRN(1'B0),
    .UART1_RIN(1'B0),
    .UART1_RX(1'B1),
    .TTC0_WAVE0_OUT(),
    .TTC0_WAVE1_OUT(),
    .TTC0_WAVE2_OUT(),
    .TTC0_CLK0_IN(1'B0),
    .TTC0_CLK1_IN(1'B0),
    .TTC0_CLK2_IN(1'B0),
    .TTC1_WAVE0_OUT(),
    .TTC1_WAVE1_OUT(),
    .TTC1_WAVE2_OUT(),
    .TTC1_CLK0_IN(1'B0),
    .TTC1_CLK1_IN(1'B0),
    .TTC1_CLK2_IN(1'B0),
    .WDT_CLK_IN(1'B0),
    .WDT_RST_OUT(),
    .TRACE_CLK(1'B0),
    .TRACE_CLK_OUT(),
    .TRACE_CTL(),
    .TRACE_DATA(),
    .USB0_PORT_INDCTL(),
    .USB0_VBUS_PWRSELECT(),
    .USB0_VBUS_PWRFAULT(1'B0),
    .USB1_PORT_INDCTL(),
    .USB1_VBUS_PWRSELECT(),
    .USB1_VBUS_PWRFAULT(1'B0),
    .SRAM_INTIN(1'B0),
    .M_AXI_GP0_ARVALID(M_AXI_GP0_ARVALID),
    .M_AXI_GP0_AWVALID(M_AXI_GP0_AWVALID),
    .M_AXI_GP0_BREADY(M_AXI_GP0_BREADY),
    .M_AXI_GP0_RREADY(M_AXI_GP0_RREADY),
    .M_AXI_GP0_WLAST(M_AXI_GP0_WLAST),
    .M_AXI_GP0_WVALID(M_AXI_GP0_WVALID),
    .M_AXI_GP0_ARID(M_AXI_GP0_ARID),
    .M_AXI_GP0_AWID(M_AXI_GP0_AWID),
    .M_AXI_GP0_WID(M_AXI_GP0_WID),
    .M_AXI_GP0_ARBURST(M_AXI_GP0_ARBURST),
    .M_AXI_GP0_ARLOCK(M_AXI_GP0_ARLOCK),
    .M_AXI_GP0_ARSIZE(M_AXI_GP0_ARSIZE),
    .M_AXI_GP0_AWBURST(M_AXI_GP0_AWBURST),
    .M_AXI_GP0_AWLOCK(M_AXI_GP0_AWLOCK),
    .M_AXI_GP0_AWSIZE(M_AXI_GP0_AWSIZE),
    .M_AXI_GP0_ARPROT(M_AXI_GP0_ARPROT),
    .M_AXI_GP0_AWPROT(M_AXI_GP0_AWPROT),
    .M_AXI_GP0_ARADDR(M_AXI_GP0_ARADDR),
    .M_AXI_GP0_AWADDR(M_AXI_GP0_AWADDR),
    .M_AXI_GP0_WDATA(M_AXI_GP0_WDATA),
    .M_AXI_GP0_ARCACHE(M_AXI_GP0_ARCACHE),
    .M_AXI_GP0_ARLEN(M_AXI_GP0_ARLEN),
    .M_AXI_GP0_ARQOS(M_AXI_GP0_ARQOS),
    .M_AXI_GP0_AWCACHE(M_AXI_GP0_AWCACHE),
    .M_AXI_GP0_AWLEN(M_AXI_GP0_AWLEN),
    .M_AXI_GP0_AWQOS(M_AXI_GP0_AWQOS),
    .M_AXI_GP0_WSTRB(M_AXI_GP0_WSTRB),
    .M_AXI_GP0_ACLK(M_AXI_GP0_ACLK),
    .M_AXI_GP0_ARREADY(M_AXI_GP0_ARREADY),
    .M_AXI_GP0_AWREADY(M_AXI_GP0_AWREADY),
    .M_AXI_GP0_BVALID(M_AXI_GP0_BVALID),
    .M_AXI_GP0_RLAST(M_AXI_GP0_RLAST),
    .M_AXI_GP0_RVALID(M_AXI_GP0_RVALID),
    .M_AXI_GP0_WREADY(M_AXI_GP0_WREADY),
    .M_AXI_GP0_BID(M_AXI_GP0_BID),
    .M_AXI_GP0_RID(M_AXI_GP0_RID),
    .M_AXI_GP0_BRESP(M_AXI_GP0_BRESP),
    .M_AXI_GP0_RRESP(M_AXI_GP0_RRESP),
    .M_AXI_GP0_RDATA(M_AXI_GP0_RDATA),
    .M_AXI_GP1_ARVALID(),
    .M_AXI_GP1_AWVALID(),
    .M_AXI_GP1_BREADY(),
    .M_AXI_GP1_RREADY(),
    .M_AXI_GP1_WLAST(),
    .M_AXI_GP1_WVALID(),
    .M_AXI_GP1_ARID(),
    .M_AXI_GP1_AWID(),
    .M_AXI_GP1_WID(),
    .M_AXI_GP1_ARBURST(),
    .M_AXI_GP1_ARLOCK(),
    .M_AXI_GP1_ARSIZE(),
    .M_AXI_GP1_AWBURST(),
    .M_AXI_GP1_AWLOCK(),
    .M_AXI_GP1_AWSIZE(),
    .M_AXI_GP1_ARPROT(),
    .M_AXI_GP1_AWPROT(),
    .M_AXI_GP1_ARADDR(),
    .M_AXI_GP1_AWADDR(),
    .M_AXI_GP1_WDATA(),
    .M_AXI_GP1_ARCACHE(),
    .M_AXI_GP1_ARLEN(),
    .M_AXI_GP1_ARQOS(),
    .M_AXI_GP1_AWCACHE(),
    .M_AXI_GP1_AWLEN(),
    .M_AXI_GP1_AWQOS(),
    .M_AXI_GP1_WSTRB(),
    .M_AXI_GP1_ACLK(1'B0),
    .M_AXI_GP1_ARREADY(1'B0),
    .M_AXI_GP1_AWREADY(1'B0),
    .M_AXI_GP1_BVALID(1'B0),
    .M_AXI_GP1_RLAST(1'B0),
    .M_AXI_GP1_RVALID(1'B0),
    .M_AXI_GP1_WREADY(1'B0),
    .M_AXI_GP1_BID(12'B0),
    .M_AXI_GP1_RID(12'B0),
    .M_AXI_GP1_BRESP(2'B0),
    .M_AXI_GP1_RRESP(2'B0),
    .M_AXI_GP1_RDATA(32'B0),
    .S_AXI_GP0_ARREADY(S_AXI_GP0_ARREADY),
    .S_AXI_GP0_AWREADY(S_AXI_GP0_AWREADY),
    .S_AXI_GP0_BVALID(S_AXI_GP0_BVALID),
    .S_AXI_GP0_RLAST(S_AXI_GP0_RLAST),
    .S_AXI_GP0_RVALID(S_AXI_GP0_RVALID),
    .S_AXI_GP0_WREADY(S_AXI_GP0_WREADY),
    .S_AXI_GP0_BRESP(S_AXI_GP0_BRESP),
    .S_AXI_GP0_RRESP(S_AXI_GP0_RRESP),
    .S_AXI_GP0_RDATA(S_AXI_GP0_RDATA),
    .S_AXI_GP0_BID(S_AXI_GP0_BID),
    .S_AXI_GP0_RID(S_AXI_GP0_RID),
    .S_AXI_GP0_ACLK(S_AXI_GP0_ACLK),
    .S_AXI_GP0_ARVALID(S_AXI_GP0_ARVALID),
    .S_AXI_GP0_AWVALID(S_AXI_GP0_AWVALID),
    .S_AXI_GP0_BREADY(S_AXI_GP0_BREADY),
    .S_AXI_GP0_RREADY(S_AXI_GP0_RREADY),
    .S_AXI_GP0_WLAST(S_AXI_GP0_WLAST),
    .S_AXI_GP0_WVALID(S_AXI_GP0_WVALID),
    .S_AXI_GP0_ARBURST(S_AXI_GP0_ARBURST),
    .S_AXI_GP0_ARLOCK(S_AXI_GP0_ARLOCK),
    .S_AXI_GP0_ARSIZE(S_AXI_GP0_ARSIZE),
    .S_AXI_GP0_AWBURST(S_AXI_GP0_AWBURST),
    .S_AXI_GP0_AWLOCK(S_AXI_GP0_AWLOCK),
    .S_AXI_GP0_AWSIZE(S_AXI_GP0_AWSIZE),
    .S_AXI_GP0_ARPROT(S_AXI_GP0_ARPROT),
    .S_AXI_GP0_AWPROT(S_AXI_GP0_AWPROT),
    .S_AXI_GP0_ARADDR(S_AXI_GP0_ARADDR),
    .S_AXI_GP0_AWADDR(S_AXI_GP0_AWADDR),
    .S_AXI_GP0_WDATA(S_AXI_GP0_WDATA),
    .S_AXI_GP0_ARCACHE(S_AXI_GP0_ARCACHE),
    .S_AXI_GP0_ARLEN(S_AXI_GP0_ARLEN),
    .S_AXI_GP0_ARQOS(S_AXI_GP0_ARQOS),
    .S_AXI_GP0_AWCACHE(S_AXI_GP0_AWCACHE),
    .S_AXI_GP0_AWLEN(S_AXI_GP0_AWLEN),
    .S_AXI_GP0_AWQOS(S_AXI_GP0_AWQOS),
    .S_AXI_GP0_WSTRB(S_AXI_GP0_WSTRB),
    .S_AXI_GP0_ARID(S_AXI_GP0_ARID),
    .S_AXI_GP0_AWID(S_AXI_GP0_AWID),
    .S_AXI_GP0_WID(S_AXI_GP0_WID),
    .S_AXI_GP1_ARREADY(S_AXI_GP1_ARREADY),
    .S_AXI_GP1_AWREADY(S_AXI_GP1_AWREADY),
    .S_AXI_GP1_BVALID(S_AXI_GP1_BVALID),
    .S_AXI_GP1_RLAST(S_AXI_GP1_RLAST),
    .S_AXI_GP1_RVALID(S_AXI_GP1_RVALID),
    .S_AXI_GP1_WREADY(S_AXI_GP1_WREADY),
    .S_AXI_GP1_BRESP(S_AXI_GP1_BRESP),
    .S_AXI_GP1_RRESP(S_AXI_GP1_RRESP),
    .S_AXI_GP1_RDATA(S_AXI_GP1_RDATA),
    .S_AXI_GP1_BID(S_AXI_GP1_BID),
    .S_AXI_GP1_RID(S_AXI_GP1_RID),
    .S_AXI_GP1_ACLK(S_AXI_GP1_ACLK),
    .S_AXI_GP1_ARVALID(S_AXI_GP1_ARVALID),
    .S_AXI_GP1_AWVALID(S_AXI_GP1_AWVALID),
    .S_AXI_GP1_BREADY(S_AXI_GP1_BREADY),
    .S_AXI_GP1_RREADY(S_AXI_GP1_RREADY),
    .S_AXI_GP1_WLAST(S_AXI_GP1_WLAST),
    .S_AXI_GP1_WVALID(S_AXI_GP1_WVALID),
    .S_AXI_GP1_ARBURST(S_AXI_GP1_ARBURST),
    .S_AXI_GP1_ARLOCK(S_AXI_GP1_ARLOCK),
    .S_AXI_GP1_ARSIZE(S_AXI_GP1_ARSIZE),
    .S_AXI_GP1_AWBURST(S_AXI_GP1_AWBURST),
    .S_AXI_GP1_AWLOCK(S_AXI_GP1_AWLOCK),
    .S_AXI_GP1_AWSIZE(S_AXI_GP1_AWSIZE),
    .S_AXI_GP1_ARPROT(S_AXI_GP1_ARPROT),
    .S_AXI_GP1_AWPROT(S_AXI_GP1_AWPROT),
    .S_AXI_GP1_ARADDR(S_AXI_GP1_ARADDR),
    .S_AXI_GP1_AWADDR(S_AXI_GP1_AWADDR),
    .S_AXI_GP1_WDATA(S_AXI_GP1_WDATA),
    .S_AXI_GP1_ARCACHE(S_AXI_GP1_ARCACHE),
    .S_AXI_GP1_ARLEN(S_AXI_GP1_ARLEN),
    .S_AXI_GP1_ARQOS(S_AXI_GP1_ARQOS),
    .S_AXI_GP1_AWCACHE(S_AXI_GP1_AWCACHE),
    .S_AXI_GP1_AWLEN(S_AXI_GP1_AWLEN),
    .S_AXI_GP1_AWQOS(S_AXI_GP1_AWQOS),
    .S_AXI_GP1_WSTRB(S_AXI_GP1_WSTRB),
    .S_AXI_GP1_ARID(S_AXI_GP1_ARID),
    .S_AXI_GP1_AWID(S_AXI_GP1_AWID),
    .S_AXI_GP1_WID(S_AXI_GP1_WID),
    .S_AXI_ACP_ARREADY(),
    .S_AXI_ACP_AWREADY(),
    .S_AXI_ACP_BVALID(),
    .S_AXI_ACP_RLAST(),
    .S_AXI_ACP_RVALID(),
    .S_AXI_ACP_WREADY(),
    .S_AXI_ACP_BRESP(),
    .S_AXI_ACP_RRESP(),
    .S_AXI_ACP_BID(),
    .S_AXI_ACP_RID(),
    .S_AXI_ACP_RDATA(),
    .S_AXI_ACP_ACLK(1'B0),
    .S_AXI_ACP_ARVALID(1'B0),
    .S_AXI_ACP_AWVALID(1'B0),
    .S_AXI_ACP_BREADY(1'B0),
    .S_AXI_ACP_RREADY(1'B0),
    .S_AXI_ACP_WLAST(1'B0),
    .S_AXI_ACP_WVALID(1'B0),
    .S_AXI_ACP_ARID(3'B0),
    .S_AXI_ACP_ARPROT(3'B0),
    .S_AXI_ACP_AWID(3'B0),
    .S_AXI_ACP_AWPROT(3'B0),
    .S_AXI_ACP_WID(3'B0),
    .S_AXI_ACP_ARADDR(32'B0),
    .S_AXI_ACP_AWADDR(32'B0),
    .S_AXI_ACP_ARCACHE(4'B0),
    .S_AXI_ACP_ARLEN(4'B0),
    .S_AXI_ACP_ARQOS(4'B0),
    .S_AXI_ACP_AWCACHE(4'B0),
    .S_AXI_ACP_AWLEN(4'B0),
    .S_AXI_ACP_AWQOS(4'B0),
    .S_AXI_ACP_ARBURST(2'B0),
    .S_AXI_ACP_ARLOCK(2'B0),
    .S_AXI_ACP_ARSIZE(3'B0),
    .S_AXI_ACP_AWBURST(2'B0),
    .S_AXI_ACP_AWLOCK(2'B0),
    .S_AXI_ACP_AWSIZE(3'B0),
    .S_AXI_ACP_ARUSER(5'B0),
    .S_AXI_ACP_AWUSER(5'B0),
    .S_AXI_ACP_WDATA(64'B0),
    .S_AXI_ACP_WSTRB(8'B0),
    .S_AXI_HP0_ARREADY(),
    .S_AXI_HP0_AWREADY(),
    .S_AXI_HP0_BVALID(),
    .S_AXI_HP0_RLAST(),
    .S_AXI_HP0_RVALID(),
    .S_AXI_HP0_WREADY(),
    .S_AXI_HP0_BRESP(),
    .S_AXI_HP0_RRESP(),
    .S_AXI_HP0_BID(),
    .S_AXI_HP0_RID(),
    .S_AXI_HP0_RDATA(),
    .S_AXI_HP0_RCOUNT(),
    .S_AXI_HP0_WCOUNT(),
    .S_AXI_HP0_RACOUNT(),
    .S_AXI_HP0_WACOUNT(),
    .S_AXI_HP0_ACLK(1'B0),
    .S_AXI_HP0_ARVALID(1'B0),
    .S_AXI_HP0_AWVALID(1'B0),
    .S_AXI_HP0_BREADY(1'B0),
    .S_AXI_HP0_RDISSUECAP1_EN(1'B0),
    .S_AXI_HP0_RREADY(1'B0),
    .S_AXI_HP0_WLAST(1'B0),
    .S_AXI_HP0_WRISSUECAP1_EN(1'B0),
    .S_AXI_HP0_WVALID(1'B0),
    .S_AXI_HP0_ARBURST(2'B0),
    .S_AXI_HP0_ARLOCK(2'B0),
    .S_AXI_HP0_ARSIZE(3'B0),
    .S_AXI_HP0_AWBURST(2'B0),
    .S_AXI_HP0_AWLOCK(2'B0),
    .S_AXI_HP0_AWSIZE(3'B0),
    .S_AXI_HP0_ARPROT(3'B0),
    .S_AXI_HP0_AWPROT(3'B0),
    .S_AXI_HP0_ARADDR(32'B0),
    .S_AXI_HP0_AWADDR(32'B0),
    .S_AXI_HP0_ARCACHE(4'B0),
    .S_AXI_HP0_ARLEN(4'B0),
    .S_AXI_HP0_ARQOS(4'B0),
    .S_AXI_HP0_AWCACHE(4'B0),
    .S_AXI_HP0_AWLEN(4'B0),
    .S_AXI_HP0_AWQOS(4'B0),
    .S_AXI_HP0_ARID(6'B0),
    .S_AXI_HP0_AWID(6'B0),
    .S_AXI_HP0_WID(6'B0),
    .S_AXI_HP0_WDATA(64'B0),
    .S_AXI_HP0_WSTRB(8'B0),
    .S_AXI_HP1_ARREADY(),
    .S_AXI_HP1_AWREADY(),
    .S_AXI_HP1_BVALID(),
    .S_AXI_HP1_RLAST(),
    .S_AXI_HP1_RVALID(),
    .S_AXI_HP1_WREADY(),
    .S_AXI_HP1_BRESP(),
    .S_AXI_HP1_RRESP(),
    .S_AXI_HP1_BID(),
    .S_AXI_HP1_RID(),
    .S_AXI_HP1_RDATA(),
    .S_AXI_HP1_RCOUNT(),
    .S_AXI_HP1_WCOUNT(),
    .S_AXI_HP1_RACOUNT(),
    .S_AXI_HP1_WACOUNT(),
    .S_AXI_HP1_ACLK(1'B0),
    .S_AXI_HP1_ARVALID(1'B0),
    .S_AXI_HP1_AWVALID(1'B0),
    .S_AXI_HP1_BREADY(1'B0),
    .S_AXI_HP1_RDISSUECAP1_EN(1'B0),
    .S_AXI_HP1_RREADY(1'B0),
    .S_AXI_HP1_WLAST(1'B0),
    .S_AXI_HP1_WRISSUECAP1_EN(1'B0),
    .S_AXI_HP1_WVALID(1'B0),
    .S_AXI_HP1_ARBURST(2'B0),
    .S_AXI_HP1_ARLOCK(2'B0),
    .S_AXI_HP1_ARSIZE(3'B0),
    .S_AXI_HP1_AWBURST(2'B0),
    .S_AXI_HP1_AWLOCK(2'B0),
    .S_AXI_HP1_AWSIZE(3'B0),
    .S_AXI_HP1_ARPROT(3'B0),
    .S_AXI_HP1_AWPROT(3'B0),
    .S_AXI_HP1_ARADDR(32'B0),
    .S_AXI_HP1_AWADDR(32'B0),
    .S_AXI_HP1_ARCACHE(4'B0),
    .S_AXI_HP1_ARLEN(4'B0),
    .S_AXI_HP1_ARQOS(4'B0),
    .S_AXI_HP1_AWCACHE(4'B0),
    .S_AXI_HP1_AWLEN(4'B0),
    .S_AXI_HP1_AWQOS(4'B0),
    .S_AXI_HP1_ARID(6'B0),
    .S_AXI_HP1_AWID(6'B0),
    .S_AXI_HP1_WID(6'B0),
    .S_AXI_HP1_WDATA(64'B0),
    .S_AXI_HP1_WSTRB(8'B0),
    .S_AXI_HP2_ARREADY(),
    .S_AXI_HP2_AWREADY(),
    .S_AXI_HP2_BVALID(),
    .S_AXI_HP2_RLAST(),
    .S_AXI_HP2_RVALID(),
    .S_AXI_HP2_WREADY(),
    .S_AXI_HP2_BRESP(),
    .S_AXI_HP2_RRESP(),
    .S_AXI_HP2_BID(),
    .S_AXI_HP2_RID(),
    .S_AXI_HP2_RDATA(),
    .S_AXI_HP2_RCOUNT(),
    .S_AXI_HP2_WCOUNT(),
    .S_AXI_HP2_RACOUNT(),
    .S_AXI_HP2_WACOUNT(),
    .S_AXI_HP2_ACLK(1'B0),
    .S_AXI_HP2_ARVALID(1'B0),
    .S_AXI_HP2_AWVALID(1'B0),
    .S_AXI_HP2_BREADY(1'B0),
    .S_AXI_HP2_RDISSUECAP1_EN(1'B0),
    .S_AXI_HP2_RREADY(1'B0),
    .S_AXI_HP2_WLAST(1'B0),
    .S_AXI_HP2_WRISSUECAP1_EN(1'B0),
    .S_AXI_HP2_WVALID(1'B0),
    .S_AXI_HP2_ARBURST(2'B0),
    .S_AXI_HP2_ARLOCK(2'B0),
    .S_AXI_HP2_ARSIZE(3'B0),
    .S_AXI_HP2_AWBURST(2'B0),
    .S_AXI_HP2_AWLOCK(2'B0),
    .S_AXI_HP2_AWSIZE(3'B0),
    .S_AXI_HP2_ARPROT(3'B0),
    .S_AXI_HP2_AWPROT(3'B0),
    .S_AXI_HP2_ARADDR(32'B0),
    .S_AXI_HP2_AWADDR(32'B0),
    .S_AXI_HP2_ARCACHE(4'B0),
    .S_AXI_HP2_ARLEN(4'B0),
    .S_AXI_HP2_ARQOS(4'B0),
    .S_AXI_HP2_AWCACHE(4'B0),
    .S_AXI_HP2_AWLEN(4'B0),
    .S_AXI_HP2_AWQOS(4'B0),
    .S_AXI_HP2_ARID(6'B0),
    .S_AXI_HP2_AWID(6'B0),
    .S_AXI_HP2_WID(6'B0),
    .S_AXI_HP2_WDATA(64'B0),
    .S_AXI_HP2_WSTRB(8'B0),
    .S_AXI_HP3_ARREADY(),
    .S_AXI_HP3_AWREADY(),
    .S_AXI_HP3_BVALID(),
    .S_AXI_HP3_RLAST(),
    .S_AXI_HP3_RVALID(),
    .S_AXI_HP3_WREADY(),
    .S_AXI_HP3_BRESP(),
    .S_AXI_HP3_RRESP(),
    .S_AXI_HP3_BID(),
    .S_AXI_HP3_RID(),
    .S_AXI_HP3_RDATA(),
    .S_AXI_HP3_RCOUNT(),
    .S_AXI_HP3_WCOUNT(),
    .S_AXI_HP3_RACOUNT(),
    .S_AXI_HP3_WACOUNT(),
    .S_AXI_HP3_ACLK(1'B0),
    .S_AXI_HP3_ARVALID(1'B0),
    .S_AXI_HP3_AWVALID(1'B0),
    .S_AXI_HP3_BREADY(1'B0),
    .S_AXI_HP3_RDISSUECAP1_EN(1'B0),
    .S_AXI_HP3_RREADY(1'B0),
    .S_AXI_HP3_WLAST(1'B0),
    .S_AXI_HP3_WRISSUECAP1_EN(1'B0),
    .S_AXI_HP3_WVALID(1'B0),
    .S_AXI_HP3_ARBURST(2'B0),
    .S_AXI_HP3_ARLOCK(2'B0),
    .S_AXI_HP3_ARSIZE(3'B0),
    .S_AXI_HP3_AWBURST(2'B0),
    .S_AXI_HP3_AWLOCK(2'B0),
    .S_AXI_HP3_AWSIZE(3'B0),
    .S_AXI_HP3_ARPROT(3'B0),
    .S_AXI_HP3_AWPROT(3'B0),
    .S_AXI_HP3_ARADDR(32'B0),
    .S_AXI_HP3_AWADDR(32'B0),
    .S_AXI_HP3_ARCACHE(4'B0),
    .S_AXI_HP3_ARLEN(4'B0),
    .S_AXI_HP3_ARQOS(4'B0),
    .S_AXI_HP3_AWCACHE(4'B0),
    .S_AXI_HP3_AWLEN(4'B0),
    .S_AXI_HP3_AWQOS(4'B0),
    .S_AXI_HP3_ARID(6'B0),
    .S_AXI_HP3_AWID(6'B0),
    .S_AXI_HP3_WID(6'B0),
    .S_AXI_HP3_WDATA(64'B0),
    .S_AXI_HP3_WSTRB(8'B0),
    .IRQ_P2F_DMAC_ABORT(),
    .IRQ_P2F_DMAC0(),
    .IRQ_P2F_DMAC1(),
    .IRQ_P2F_DMAC2(),
    .IRQ_P2F_DMAC3(),
    .IRQ_P2F_DMAC4(),
    .IRQ_P2F_DMAC5(),
    .IRQ_P2F_DMAC6(),
    .IRQ_P2F_DMAC7(),
    .IRQ_P2F_SMC(),
    .IRQ_P2F_QSPI(),
    .IRQ_P2F_CTI(),
    .IRQ_P2F_GPIO(),
    .IRQ_P2F_USB0(),
    .IRQ_P2F_ENET0(),
    .IRQ_P2F_ENET_WAKE0(),
    .IRQ_P2F_SDIO0(),
    .IRQ_P2F_I2C0(),
    .IRQ_P2F_SPI0(),
    .IRQ_P2F_UART0(),
    .IRQ_P2F_CAN0(),
    .IRQ_P2F_USB1(),
    .IRQ_P2F_ENET1(),
    .IRQ_P2F_ENET_WAKE1(),
    .IRQ_P2F_SDIO1(),
    .IRQ_P2F_I2C1(),
    .IRQ_P2F_SPI1(),
    .IRQ_P2F_UART1(),
    .IRQ_P2F_CAN1(),
    .IRQ_F2P(1'B0),
    .Core0_nFIQ(1'B0),
    .Core0_nIRQ(1'B0),
    .Core1_nFIQ(1'B0),
    .Core1_nIRQ(1'B0),
    .DMA0_DATYPE(),
    .DMA0_DAVALID(),
    .DMA0_DRREADY(),
    .DMA1_DATYPE(),
    .DMA1_DAVALID(),
    .DMA1_DRREADY(),
    .DMA2_DATYPE(),
    .DMA2_DAVALID(),
    .DMA2_DRREADY(),
    .DMA3_DATYPE(),
    .DMA3_DAVALID(),
    .DMA3_DRREADY(),
    .DMA0_ACLK(1'B0),
    .DMA0_DAREADY(1'B0),
    .DMA0_DRLAST(1'B0),
    .DMA0_DRVALID(1'B0),
    .DMA1_ACLK(1'B0),
    .DMA1_DAREADY(1'B0),
    .DMA1_DRLAST(1'B0),
    .DMA1_DRVALID(1'B0),
    .DMA2_ACLK(1'B0),
    .DMA2_DAREADY(1'B0),
    .DMA2_DRLAST(1'B0),
    .DMA2_DRVALID(1'B0),
    .DMA3_ACLK(1'B0),
    .DMA3_DAREADY(1'B0),
    .DMA3_DRLAST(1'B0),
    .DMA3_DRVALID(1'B0),
    .DMA0_DRTYPE(2'B0),
    .DMA1_DRTYPE(2'B0),
    .DMA2_DRTYPE(2'B0),
    .DMA3_DRTYPE(2'B0),
    .FCLK_CLK0(FCLK_CLK0),
    .FCLK_CLK1(),
    .FCLK_CLK2(),
    .FCLK_CLK3(),
    .FCLK_CLKTRIG0_N(1'B0),
    .FCLK_CLKTRIG1_N(1'B0),
    .FCLK_CLKTRIG2_N(1'B0),
    .FCLK_CLKTRIG3_N(1'B0),
    .FCLK_RESET0_N(FCLK_RESET0_N),
    .FCLK_RESET1_N(),
    .FCLK_RESET2_N(),
    .FCLK_RESET3_N(),
    .FTMD_TRACEIN_DATA(32'B0),
    .FTMD_TRACEIN_VALID(1'B0),
    .FTMD_TRACEIN_CLK(1'B0),
    .FTMD_TRACEIN_ATID(4'B0),
    .FTMT_F2P_TRIG_0(1'B0),
    .FTMT_F2P_TRIGACK_0(),
    .FTMT_F2P_TRIG_1(1'B0),
    .FTMT_F2P_TRIGACK_1(),
    .FTMT_F2P_TRIG_2(1'B0),
    .FTMT_F2P_TRIGACK_2(),
    .FTMT_F2P_TRIG_3(1'B0),
    .FTMT_F2P_TRIGACK_3(),
    .FTMT_F2P_DEBUG(32'B0),
    .FTMT_P2F_TRIGACK_0(1'B0),
    .FTMT_P2F_TRIG_0(),
    .FTMT_P2F_TRIGACK_1(1'B0),
    .FTMT_P2F_TRIG_1(),
    .FTMT_P2F_TRIGACK_2(1'B0),
    .FTMT_P2F_TRIG_2(),
    .FTMT_P2F_TRIGACK_3(1'B0),
    .FTMT_P2F_TRIG_3(),
    .FTMT_P2F_DEBUG(),
    .FPGA_IDLE_N(1'B0),
    .EVENT_EVENTO(),
    .EVENT_STANDBYWFE(),
    .EVENT_STANDBYWFI(),
    .EVENT_EVENTI(1'B0),
    .DDR_ARB(4'B0),
    .MIO(MIO),
    .DDR_CAS_n(DDR_CAS_n),
    .DDR_CKE(DDR_CKE),
    .DDR_Clk_n(DDR_Clk_n),
    .DDR_Clk(DDR_Clk),
    .DDR_CS_n(DDR_CS_n),
    .DDR_DRSTB(DDR_DRSTB),
    .DDR_ODT(DDR_ODT),
    .DDR_RAS_n(DDR_RAS_n),
    .DDR_WEB(DDR_WEB),
    .DDR_BankAddr(DDR_BankAddr),
    .DDR_Addr(DDR_Addr),
    .DDR_VRN(DDR_VRN),
    .DDR_VRP(DDR_VRP),
    .DDR_DM(DDR_DM),
    .DDR_DQ(DDR_DQ),
    .DDR_DQS_n(DDR_DQS_n),
    .DDR_DQS(DDR_DQS),
    .PS_SRSTB(PS_SRSTB),
    .PS_CLK(PS_CLK),
    .PS_PORB(PS_PORB)
  );
endmodule
