SunnyYoshimitsu/CelestiCall/Hardwares/Library_vivado/ip/Pmods/PmodOLED_v1_0/drivers/PmodOLED_v1_0/src/PmodOLED.c

/******************************************************************************/
/*                                                                            */
/* PmodOLED.c -- Basic functions for PmodOLED IP Driver                       */
/*                                                                            */
/******************************************************************************/
/* Author: Thomas Kappenman                                                   */
/* Copyright 2015, Digilent Inc.                                              */
/******************************************************************************/
/* File Description:                                                          */
/*                                                                            */
/* Contains drivers for use with a PmodOLED                                   */
/*                                                                            */
/******************************************************************************/
/* Revision History:                                                          */
/*                                                                            */
/*    04/19/2016(TommyK):   Created                                           */
/*    06/30/2016(ArtVVB):   Updated for PmodOLED IP Drivers                   */
/*    12/15/2016(jPeyron):  Edited for better use for OnboardOLED in as well  */
/*                          as inverting the white and black                  */
/*    08/25/2017(ArtVVB):   Validated for Vivado 2015.4                       */
/*    08/25/2017(ArtVVB):   Validated for Vivado 2016.4                       */
/*                          Removed MB_Sleep calls                            */
/*    02/17/2018(atangzwj): Validated for Vivado 2017.4                       */
/*    08/09/2023(MihaiR):   Updated OLED_SetGPIOTristateBits fValue parameter */
/*                          explanation and moved the XSpi_Stop command from  */
/*                          the OLED_End() function to OLED_HostTerm()        */
/*                          function.                                         */
/*                                                                            */
/******************************************************************************/

/***************************** Include Files *******************************/

#include "PmodOLED.h"
#include "sleep.h"


XSpi_Config OLEDConfig =
{
   0,
   0,
   1,
   0,
   1,
   8,
   0,
   0,
   0,
   0,
   0
};

/************************** Function Definitions ***************************/

/* ------------------------------------------------------------ */
/*** void OLED_Begin(PmodOLED *InstancePtr, u32 GPIO_Address, u32 SPI_Address)
**
**   Parameters:
**      InstancePtr:  A PmodOLED device to start
**      GPIO_Address: The Base address of the PmodOLED GPIO
**      SPI_Address:  The Base address of the PmodOLED SPI
**
**   Return Value:
**      none
**
**   Errors:
**      none
**
**   Description:
**      Initialize the PmodOLED.
*/
void OLED_Begin(PmodOLED *InstancePtr, u32 GPIO_Address, u32 SPI_Address,
      u8 orientation, u8 invert) {
   OLED_Init(InstancePtr, GPIO_Address, SPI_Address, orientation, invert);
}
/* ------------------------------------------------------------ */
/*** OLED_End(void)
**
**   Parameters:
**      InstancePtr: PmodOLED device to stop
**
**   Return Value:
**      none
**
**   Errors:
**      none
**
**   Description:
**      Stops the device
*/
void OLED_End(PmodOLED *InstancePtr) {
    OLED_Term(InstancePtr);
}
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
